gaucho1978/BACCAble/hardware/box/baccable_lastest_case_for_new_PCB/preview5.jpg

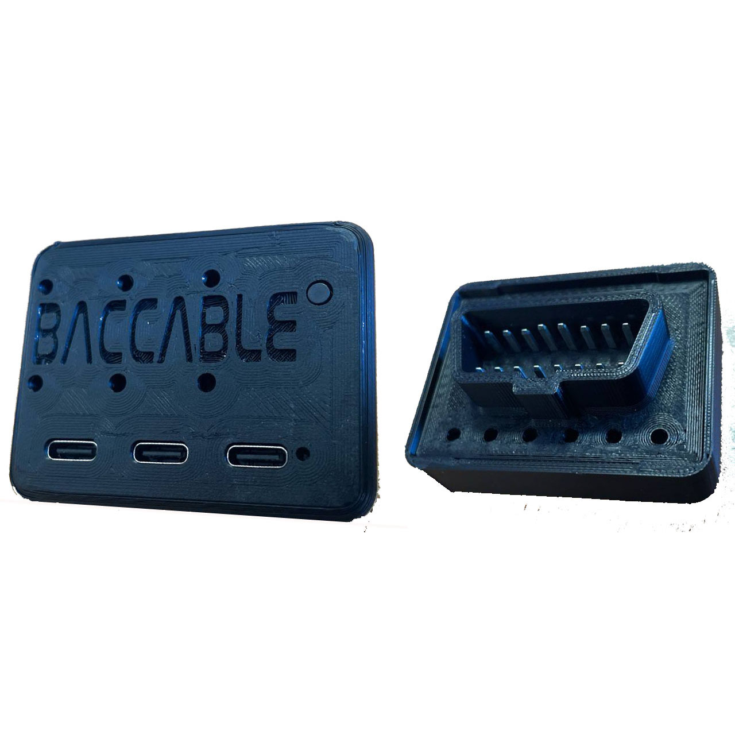
hardware/box/baccable_lastest_case_for_new_PCB/preview5.jpg
