gaucho1978/BACCAble/hardware/box/canableDykbRadioNanoOnly/box.png

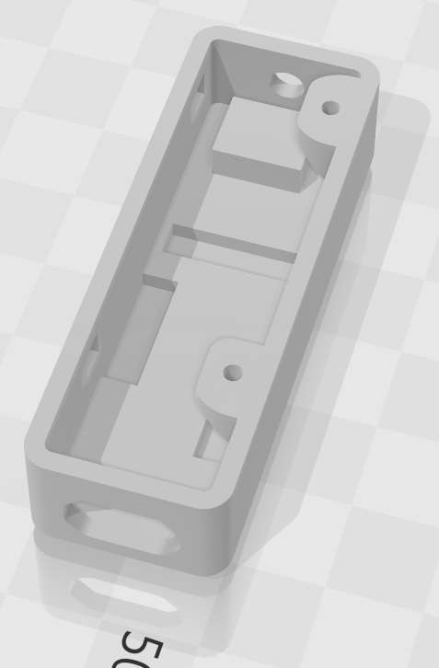
hardware/box/canableDykbRadioNanoOnly/box.png
