gaucho1978/BACCAble/hardware/box/canableDykbRadioNanoOnly/cap.png

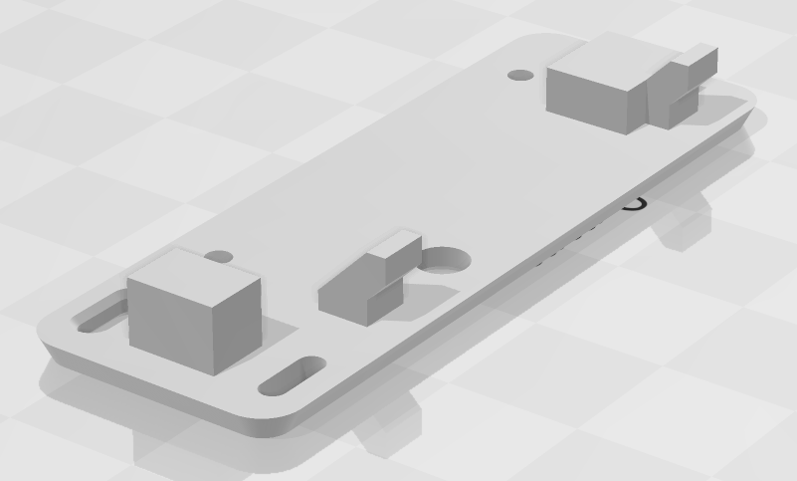
hardware/box/canableDykbRadioNanoOnly/cap.png
