gaucho1978/BACCAble/hardware/box/canableWithDcDcAndTB/box.png

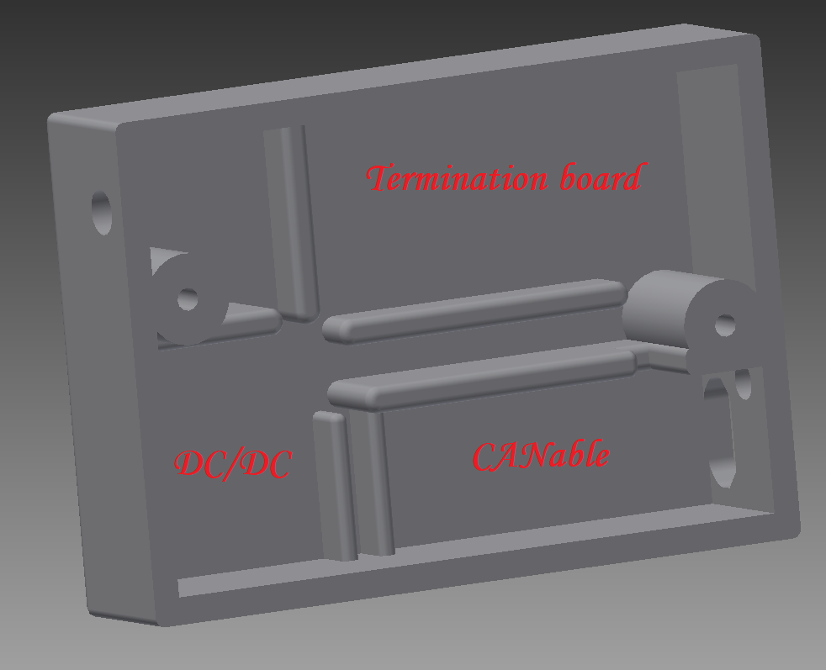
hardware/box/canableWithDcDcAndTB/box.png
