gaucho1978/BACCAble/hardware/box/canableWithDcDcAndTB/cap.png

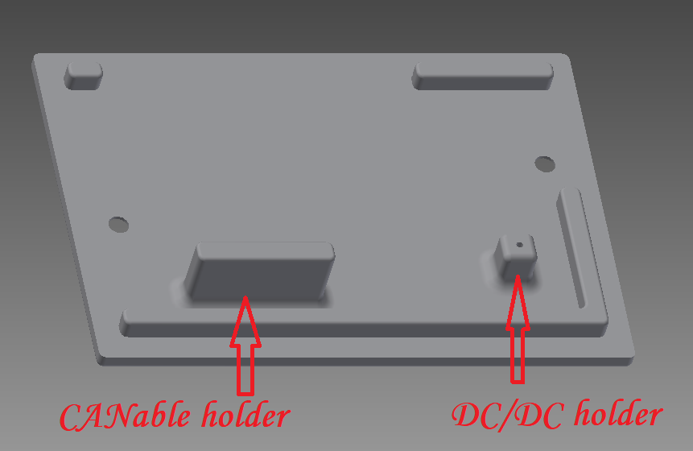
hardware/box/canableWithDcDcAndTB/cap.png
