gaucho1978/BACCAble/hardware/newBaccableDedicatedPcb/pinout.png

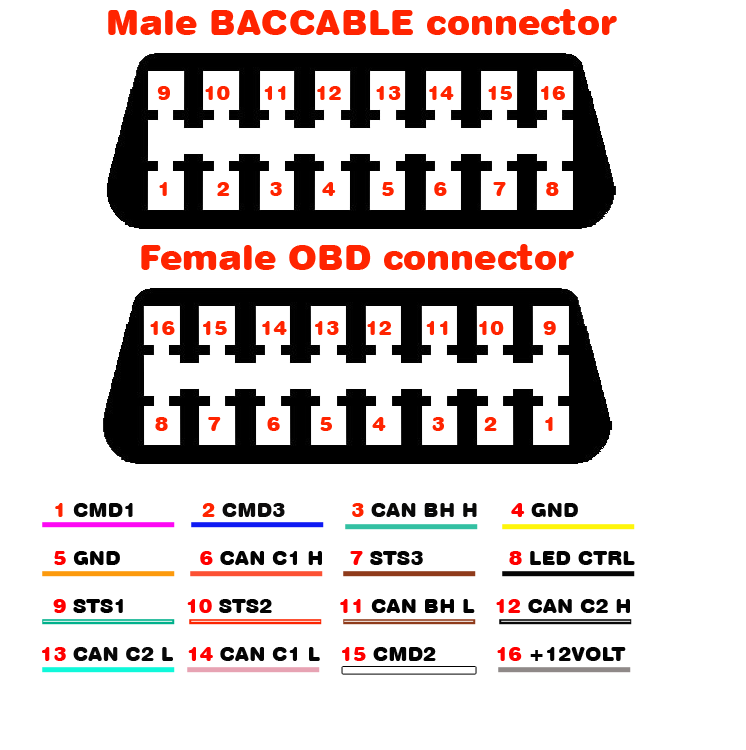
hardware/newBaccableDedicatedPcb/pinout.png
