gaucho1978/BACCAble/hardware/sticker/baccableLabe1l.png

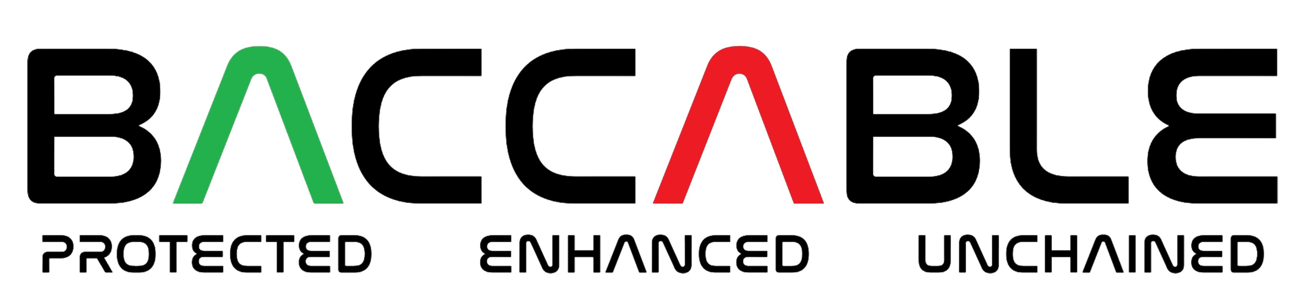
hardware/sticker/baccableLabe1l.png
