gaucho1978/BACCAble/hardware/system_interconnection/IMG_3511.jpeg

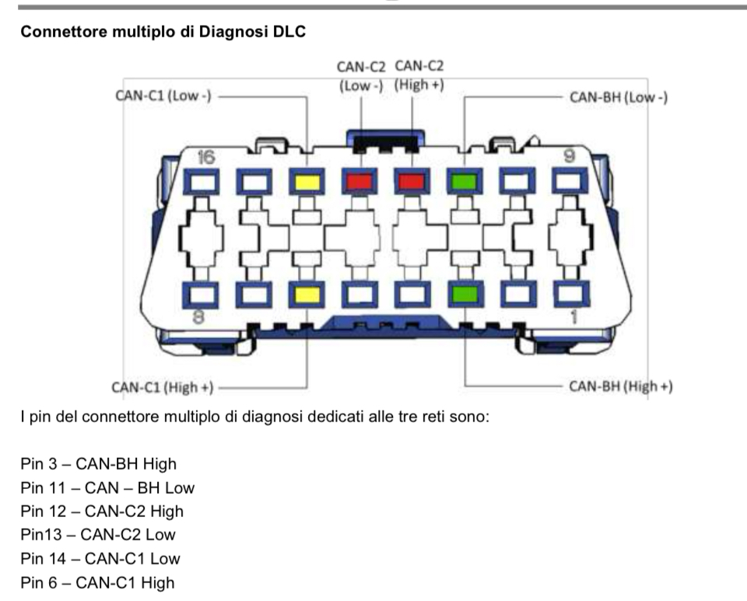
hardware/system_interconnection/IMG_3511.jpeg
