gaucho1978/BACCAble/hardware/system_interconnection/route.png

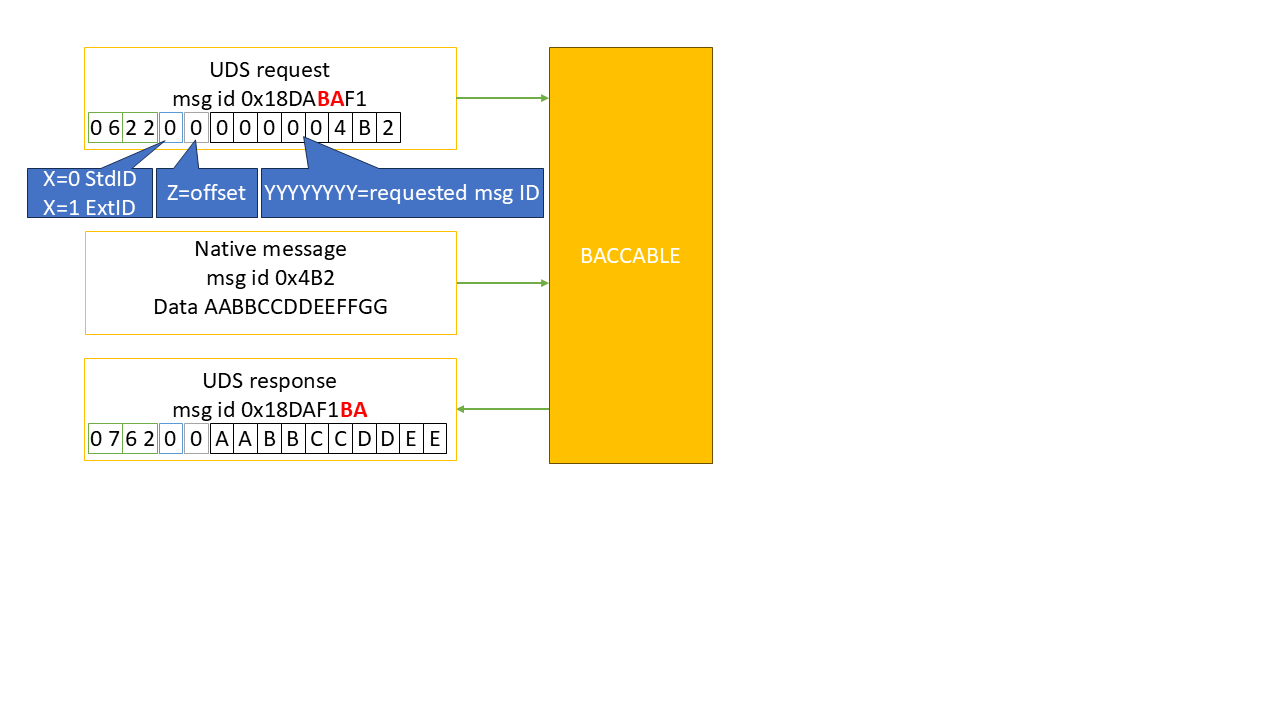
hardware/system_interconnection/route.png
