gaucho1978/BACCAble/hardware/system_interconnection/SCHEMA_DI_INTERCONNESSIONE.png

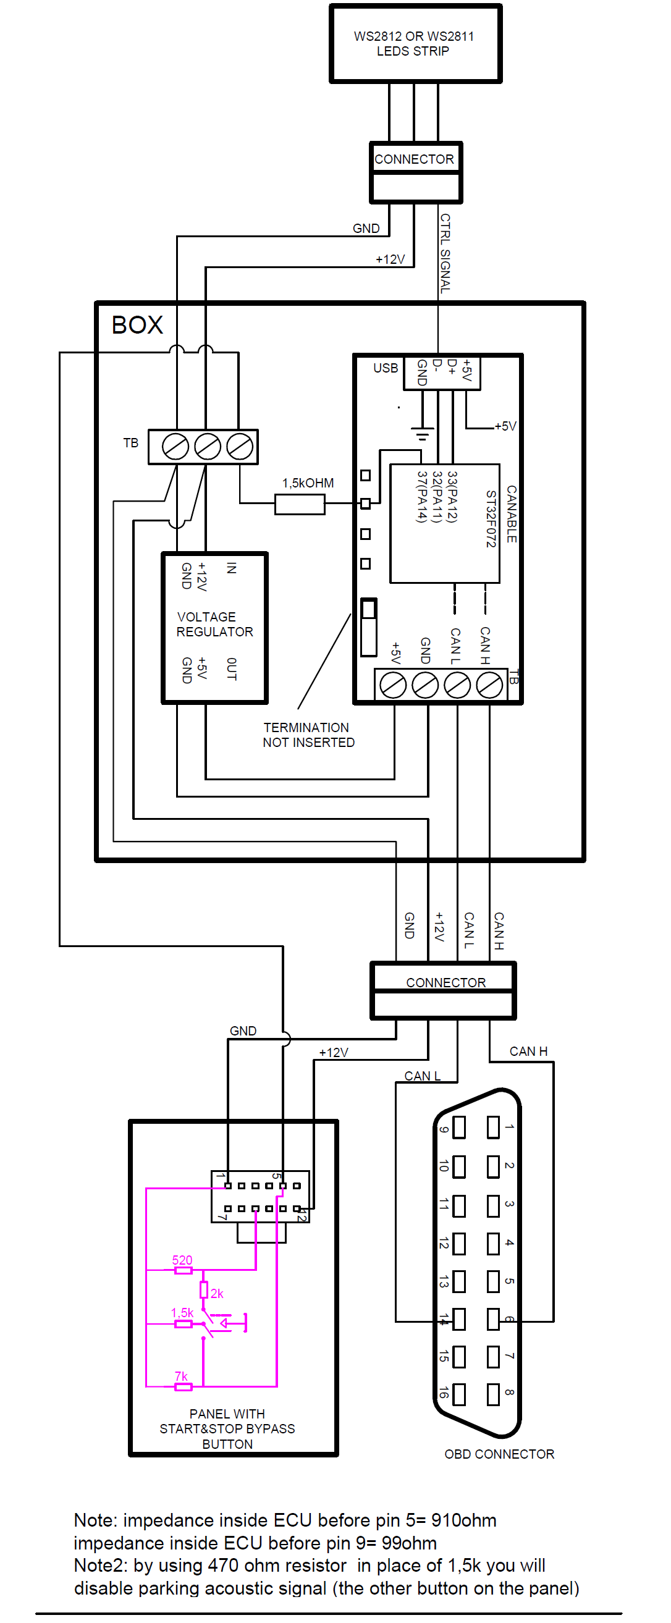
hardware/system_interconnection/SCHEMA_DI_INTERCONNESSIONE.png
