gaucho1978/BACCAble/hardware/box/baccable_lastest_case_for_new_PCB_V2/Imported Components/Baccable4/Baccable4.htm

Autodesk Inventor Translation Report | mercoledì 9 aprile 2025 (18:47)
Source File: | E:\Dati\Documenti_Emanuele\Linguaggi_di_Programmazione\ST MCU\baccable\canable\CANableAndLedsStripController\hardware\box\baccable_lastest_case_for_new_PCB\Baccable4.stp
Translator Type: | STEP | Sending System: | Open CASCADE 6.2
Author: | Author | Translation Time: | 00:00:15
Options
Import Type: | N/A
Entity Types to Import: | Solids, Surfaces
Import into Repair Environment: | No
Import Assembly as Single Part: | Multiple Solid Part
Create Surfaces As: | Single Composite Feature
Check Parts during Load: | No
Auto Stitch: | N/A
Enable Advanced Healing: | No
+/- | Name | Inventor File | Status
[+] [-] | Baccable4.ipt | E:\Dati\Documenti_Emanuele\Linguaggi_di_Programmazione\ST MCU\baccable\canable\CANableAndLedsStripController\hardware\box\baccable_lastest_case_for_new_PCB\Imported Components\Baccable4\Baccable4.ipt | Warning
Severity | Entity Id | Message
Warning | 10938 | Some Surfaces have been simplified
Warning | 19486 | Some Surfaces have been simplified
Warning | 34496 | Some Surfaces have been simplified
Warning | 38605 | Some Surfaces have been simplified
Warning | 52556 | Some Surfaces have been simplified
Warning | 58078 | Degenerate Surface Detected - Please Run the Quality Check Tool
Warning | 58159 | Degenerate Surface Detected - Please Run the Quality Check Tool
Warning | 58291 | Degenerate Surface Detected - Please Run the Quality Check Tool
Warning | 58372 | Degenerate Surface Detected - Please Run the Quality Check Tool
Warning | 56693 | Some Surfaces have been simplified
Warning | 61650 | Degenerate Surface Detected - Please Run the Quality Check Tool
Warning | 61729 | Degenerate Surface Detected - Please Run the Quality Check Tool
Warning | 61811 | Degenerate Surface Detected - Please Run the Quality Check Tool
Warning | 61890 | Degenerate Surface Detected - Please Run the Quality Check Tool
Warning | 64640 | Degenerate Surface Detected - Please Run the Quality Check Tool
Warning | 64721 | Degenerate Surface Detected - Please Run the Quality Check Tool
Warning | 64853 | Degenerate Surface Detected - Please Run the Quality Check Tool
Warning | 64934 | Degenerate Surface Detected - Please Run the Quality Check Tool
Warning | 67202 | Degenerate Surface Detected - Please Run the Quality Check Tool
Warning | 67281 | Degenerate Surface Detected - Please Run the Quality Check Tool
Warning | 67363 | Degenerate Surface Detected - Please Run the Quality Check Tool
Warning | 67442 | Degenerate Surface Detected - Please Run the Quality Check Tool
Warning | 64459 | Some Surfaces have been simplified
Warning | 72437 | Some Surfaces have been simplified
Warning | 244824 | Some Surfaces have been simplified
