gaucho1978/BACCAble/firmware/ledsStripController/Core/Src/functions_C1baccable.c

/*
 * C1baccableFunctions.c
 *
 *  Created on: May 2, 2025
 *      Author: GauchoHP
 *      Common functions for C1baccable
 */
#include <functions_C1baccable.h>

	extern uint32_t _end;      // Fine della sezione .bss (fornito dal linker)
	extern uint32_t _estack;   // Top dello stack (fornito dal linker)
	//uint8_t tmpArr3[2]={C2BusID,C2cmdRaceMaskDefault};

#if defined(C1baccable)
	void C1baccableInitCheck(){
		#ifndef DISABLE_LOW_CONSUME
			lowConsume_init();
		#endif
		immobilizerEnabled = (uint8_t)readFromFlash(1);  //parameter1 stored in ram, so that we can get it. By default Immo is enabled
		if(immobilizerEnabled) executeDashboardBlinks=2; //shows the user that the immobilizer is active (or not)
		function_smart_disable_start_stop_enabled=(uint8_t)readFromFlash(2);  //parameter2 stored in ram, so that we can get it. By default S&S is enabled
		function_led_strip_controller_enabled=(uint8_t)readFromFlash(3); //By default led is disabled
		function_shift_indicator_enabled=(uint8_t)readFromFlash(4); //By default it is disabled
		shift_threshold= (uint16_t)readFromFlash(5);
		function_ipc_my23_is_installed=	(uint8_t)readFromFlash(6);
		function_route_msg_enabled=(uint8_t)readFromFlash(7);
		function_dyno_mode_master_enabled=(uint8_t)readFromFlash(8);
		function_acc_virtual_pad_enabled=(uint8_t)readFromFlash(9);
		function_front_brake_forcer_master=(uint8_t)readFromFlash(10);
		function_4wd_disabler_enabled=(uint8_t)readFromFlash(11);
		function_remote_start_Enabled=(uint8_t)readFromFlash(12);
		function_clear_faults_enabled=(uint8_t)readFromFlash(13);
		function_esc_tc_customizator_enabled=(uint8_t)readFromFlash(14);
		function_read_faults_enabled=(uint8_t)readFromFlash(15);
		function_is_diesel_enabled=(uint8_t)readFromFlash(16);
		total_pages_in_params_setup_dashboard_menu = function_is_diesel_enabled ? total_pages_in_dashboard_menu_diesel : total_pages_in_dashboard_menu_gasoline;

		function_regeneration_alert_enabled=(uint8_t)readFromFlash(17);
		launch_torque_threshold= (uint16_t)readFromFlash(18);
		function_seatbelt_alarm_enabled= (uint16_t)readFromFlash(19);
		function_pedal_booster_enabled= (uint16_t)readFromFlash(20);
		function_disable_odometer_blink= (uint16_t)readFromFlash(21);
		function_show_race_mask= (uint16_t)readFromFlash(22);
		function_park_mirror= (uint16_t)readFromFlash(23);
		function_acc_autostart= (uint16_t)readFromFlash(24);
		function_close_windows_with_door_lock=(uint16_t)readFromFlash(25);
		function_open_windows_with_door_lock=(uint16_t)readFromFlash(26);
		HAS_function_enabled=(uint16_t)readFromFlash(27);
		QV_exhaust_flap_function_enabled=(uint16_t)readFromFlash(28);
		pedal_map_power=(int8_t)(uint8_t)readFromFlash(29);
		parkSensorsMuteFunctionEnabled=(uint8_t)readFromFlash(30);
		snifferFunctionEnabled=(uint8_t)readFromFlash(31); //sniffer function 24/08/2026
		//started here, at boot, so that snifferInUse blocks low consume straight away: lowConsume_process() runs
		//at the top of C1baccablePeriodicCheck() and its inactivity timeout (3500ms) expires 2ms BEFORE the
		//instructSlaveBoardsTriggerEnabled block below (3502ms), so anything that only sets snifferInUse down
		//there would lose that race and C1 would sleep (and pause the inter chip uart) first.
		//The detection window itself is realigned to the slaves later, see that same block. //sniffer function 24/08/2026
		if(snifferFunctionEnabled) snifferStart();
		//elm327 function 26/08/2026 - same lifecycle, but starting it only brings the usb port up and starts the
		//detection window: the baccable keeps working normally until a host actually enumerates us (see
		//elm327CheckActivationTimeout()). The two modes share the single usb cdc port, so they are mutually
		//exclusive: the setup menu already clears one when the other is enabled, this is just the safety net.
		elm327FunctionEnabled=(uint8_t)readFromFlash(32);
		if(elm327FunctionEnabled && snifferFunctionEnabled==0) elm327Start();
		//arise trigger to notify enabled functions to slave boards with dedicated messages,after some seconds
		allProcessorsWakeupTime=currentTime;
		instructSlaveBoardsTriggerEnabled=1;

		readShownParamsFromFlash();
	}

	void setSchizzaforteMap(uint8_t map){
		uint8_t tmpArr0[UART1_BUFFER_SIZE]={'#',0xb6,};

		// Schizzaforte Operative commands:
		//				First Character: #
		//				Second Character:	0x00=set Bypass map, 0x49=set All weather map, 0x92=set Natural map, 0xdb=set Dynamic map,
		//													0x24=set Race map, 0x6d=get current Map, 0xb6=define a Map
		//				Next Characters:	In case of command 0xb6(Define a Map), more 7 chars are sent:
		//													3)map to write (0x00=set Bypass map, 0x49=set All weather map, 0x92=set Natural map,
		//														0xdb=set Dynamic map, 0x24=set Race map),
		//													4)polynomialcurve[][0]
		//													5)polynomialcurve[][1]
		//													6)polynomialcurve[][2]
		//													7)polynomialcurve[][3]
		//													8)polynomialcurve[][4]
		//													9)checksum (calculated)
		// Current selected Map is sent as Reply: 0x10=Bypass, 0x59=All weather, 0xa2=Natural, 0xeb=Dynamic, 0x34=Race

		//map: 2=Bypass, 3=All Weather Map, 4=Natural Map, 5=Dynamic Map, 6=Race Map



		switch(map){
			case 3: //A map
				//prepare power amplification factor
				//input range -10+10, output range -16+16
				if (pedal_map_power >= 0){
					pedal_map_power_adapted = (int8_t)(pedal_map_power * 1.6f+0.5f);
				}else{
					pedal_map_power_adapted = (int8_t)(pedal_map_power * 0.6f-0.5f);
				}

				tmpArr0[2]=0x49;	//A map
				tmpArr0[3]=96+pedal_map_power_adapted;	//amplitude
				tmpArr0[4]=128;		//width
				tmpArr0[5]=154;		//position
				break;
			case 4: //N map
				//prepare power amplification factor
				//input range -10+10, output range -16+32
				if (pedal_map_power >= 0) {
					pedal_map_power_adapted = (int8_t)(pedal_map_power * 3.2f + 0.5f);
				} else {
					pedal_map_power_adapted = (int8_t)(pedal_map_power * 1.6f - 0.5f);
				}

				tmpArr0[2]=0x92;
				tmpArr0[3]=128+pedal_map_power_adapted;		//amplitude
				tmpArr0[4]=128;		//width
				tmpArr0[5]=154;		//position
				break;
			case 5: //D Map
				//prepare power amplification factor
				//input range -10+10, output range -32+20
				if (pedal_map_power >= 0) {
					pedal_map_power_adapted = (int8_t)(pedal_map_power * 2.0f + 0.5f);
				} else {
					pedal_map_power_adapted = (int8_t)(pedal_map_power * 3.2f - 0.5f);
				}
				tmpArr0[2]=0xdb;
				tmpArr0[3]=192+pedal_map_power_adapted;		//amplitude
				tmpArr0[4]=128;		//width
				tmpArr0[5]=154;		//position
				break;
			case 6: //R map
				//prepare power amplification factor
				//input range -10+10, output range -18+24
				if (pedal_map_power >= 0) {
					pedal_map_power_adapted = (int8_t)(pedal_map_power * 2.4f + 0.5f);
				} else {
					pedal_map_power_adapted = (int8_t)(pedal_map_power * 1.8f - 0.5f);
				}
				tmpArr0[2]=0x24;
				tmpArr0[3]=230+pedal_map_power_adapted;		//amplitude
				tmpArr0[4]=128;		//width
				tmpArr0[5]=154;		//position
				break;
			case 2: //bypass
			default: //bypass
				tmpArr0[2]=0x00;
				break;
		}

		tmpArr0[8]=calculateCRC(tmpArr0,UART1_BUFFER_SIZE); //calculate checksum

		//send message
		addToUART1SendQueue(tmpArr0, 9);

	}


	//elm327 function 26/08/2026 - BEGIN
	//Only ram is touched here, so this is safe from anywhere: bringing usb up blocks for a few milliseconds and
	//is deferred to elm327UsbStartIfRequested(), exactly like snifferStart() does.
	void elm327Start(void){
		elm327InUse=1;
		elm327ActivationConfirmed=0;
		elm327ActivationTime=currentTime;	//starts the host detection window (SNIFFER_ACTIVATION_TIMEOUT_MS)
		elm327UsbStartRequested=1;
	}

	//Leaves the mode for good: interpreter off, bridge disarmed on all three chips, usb port down.
	//elm327_set_enabled(0) does all of that (see elm327.c), including usb_device_detach().
	void elm327Stop(void){
		uint8_t wasConfirmed=elm327ActivationConfirmed;
		elm327InUse=0;
		elm327ActivationConfirmed=0;
		elm327UsbStartRequested=0;
		if(wasConfirmed){
			elm327_set_enabled(0);
		}else{
			usb_device_detach(); //never confirmed: the port was only up waiting for a host, nothing else to undo
		}
		//while the mode was running we were not watching the can bus at all, so the last received message would
		//look minutes old and low consume would reset the other two chips the moment we resume. Start the
		//inactivity count from now instead.
		lastReceivedCanMsgTime=currentTime;
		//the slaves spent that time serving the bridge: resend them every function status, as after a wake up
		allProcessorsWakeupTime=currentTime;
		instructSlaveBoardsTriggerEnabled=1;
	}

	//Brings the usb port up. Called from the main loop only: usb_device_attach() waits on HAL_Delay().
	void elm327UsbStartIfRequested(void){
		if(elm327UsbStartRequested==0) return;
		elm327UsbStartRequested=0;
		usb_device_attach(); //idempotent, and it selects the elm327 descriptors on its own
	}

	//Called every main loop iteration while the function is on. Mirrors snifferCheckActivationTimeout(), but
	//the interpreter is switched on only once a host has really enumerated us: until then the baccable must
	//keep working normally, because turning ELM327 on freezes the dashboard and takes over the serial line.
	void elm327CheckActivationTimeout(void){
		if(elm327InUse==0) return;
		if(hUsbDeviceFS.dev_state==USBD_STATE_CONFIGURED){
			if(elm327ActivationConfirmed==0){
				elm327ActivationConfirmed=1;
				elm327_set_enabled(1); //only NOW the baccable steps aside and the bridge is armed
			}
			elm327ActivationTime=currentTime;
			return;
		}
		if(currentTime-elm327ActivationTime<SNIFFER_ACTIVATION_TIMEOUT_MS) return; //still within the grace window
		elm327Stop(); //host never showed up, or went away: back to being a plain baccable
	}
	//elm327 function 26/08/2026 - END

	void C1baccablePeriodicCheck(){
		#ifndef DISABLE_LOW_CONSUME
			lowConsume_process();
		#endif

		if(QV_exhaust_flap_function_enabled){

			// Timeout management for chinese valves radiocontrol
			if (exhaustValveMosfetCommandTime) {
				if(currentTime - exhaustValveMosfetCommandTime > 1000){ //if timeout has passed
					HAL_GPIO_WritePin(Q10mosfet, GPIO_PIN_RESET); //open the transistor (release the button)
					HAL_GPIO_WritePin(Q11mosfet, GPIO_PIN_RESET); //open the transistor (release the button)
					exhaustValveMosfetCommandTime = 0;
				}
			}

			// if a request to press the button on the radiocontrol was made
			if (ChineseExhaustValveRequest){ //O=open, C=close, 0x00=none
			    HAL_GPIO_WritePin(Q10mosfet_Port,(ChineseExhaustValveRequest == 'O') ? Q10mosfet_Pin : Q11mosfet_Pin,GPIO_PIN_SET); //close transistor (press button)
			    chineseValveIsOpened = (ChineseExhaustValveRequest == 'O'); //store valves status
			    exhaustValveMosfetCommandTime = currentTime; //store time when button was pressed
			    ChineseExhaustValveRequest = 0; //mark the request as executed
			}

			// if valve was open and engine had been shutted off
			if (chineseValveIsOpened && currentRpmSpeed == 0){
			    HAL_GPIO_WritePin(Q11mosfet, GPIO_PIN_SET); //close transistor
			    exhaustValveMosfetCommandTime = currentTime; //store time when button was pressed
			    chineseValveIsOpened = 0; //update valves status
			}


			switch(ForceQVexhaustValveOpened){
				case 1: //send connection request
				case 2: //send presence
				case 3: //overwrite param
				case 4: //return control to ECU
					if(currentTime-lastSentQVexhaustValveMsgTime>500){ //each 500msec send a message
						if(currentRpmSpeed==0) ForceQVexhaustValveOpened=4; //return control to ecu
						onboardLed_blue_on();
						//onboardLed_red_on();
						can_tx(&forceQVexhaustValveMsgHeader[ForceQVexhaustValveOpened-1], forceQVexhaustValveMsgData[ForceQVexhaustValveOpened-1]); //send connect message
						lastSentQVexhaustValveMsgTime=currentTime;
						switch(ForceQVexhaustValveOpened){
							case 1: //connection request was sent
							case 2: //presence was sent
								ForceQVexhaustValveOpened++; //prepare to send next
								break;
							case 3: //param overwrite was sent
								ForceQVexhaustValveOpened--; //prepare to send tester presence
								break;
							case 4: //return control to ECU was sent
								ForceQVexhaustValveOpened=0; //sequence end
								break;
							default:  //we will never come here
								break;
						}

					}
					break;
				default: //do nothing
					break;
			}

		}

		if(ESCandTCinversion){
			if(currentRpmSpeed==0) ESCandTCinversion=0;
			if((currentTime-lastSent384)>50){
				lastSent384=currentTime;
				DNA_msg_data[1] = (DNA_msg_data[1] & ~0x7C) | 0x30;  //set Race mode (0x30) to show on IPC the race screen
				//uint8_t tmpCounter=(DNA_msg_data[6] & 0x0F)+1;
				//if(tmpCounter>0x0F) tmpCounter=0;
				//DNA_msg_data[6]= (DNA_msg_data[6] & 0xF0) | tmpCounter;   //increment counter
				DNA_msg_data[7]=calculateCRC(DNA_msg_data,DNA_msg_header.DLC); //update CRC
				can_tx((CAN_TxHeaderTypeDef *)&DNA_msg_header, DNA_msg_data); //transmit the modified packet
			}
		}


		if(instructSlaveBoardsTriggerEnabled){
			if((currentTime-allProcessorsWakeupTime)>TIMING__C1____DELAY_BEFORE_SERIAL_INSTRUCT_OF_C2BH_AFTER_OTHER_CHIP_WAKE_MS){
				//onboardLed_red_blink(5);
				instructSlaveBoardsTriggerEnabled=0; //avoid to return here


				//send messages to slave boards
				uint8_t tmpArr0[2]={C2_Bh_BusID,C2_Bh_cmdFunction_ESC_TC_Enabled};
				if(!function_esc_tc_customizator_enabled) tmpArr0[1]=C2_Bh_cmdFunction_ESC_TC_Disabled;
				addToUARTSendQueue(tmpArr0, 2);

				//send messages to slave boards
				uint8_t tmpArr1[3]={C2_Bh_BusID,C2_Bh_cmdSetPedalBoostStatus,function_pedal_booster_enabled};
				addToUARTSendQueue(tmpArr1, 3);

				//send the message to BH to inform about the status of the function disable_odometer_blink
				uint8_t tmpArr2[2]={BhBusID,BHcmdOdometerBlinkDefault};
				if(function_disable_odometer_blink) tmpArr2[1]=BHcmdOdometerBlinkDisable;
				addToUARTSendQueue(tmpArr2, 2);

				//Now let's inform the C2 Baccable
				uint8_t tmpArr3[2]={C2BusID,C2cmdRaceMaskDefault};
				if(function_show_race_mask) tmpArr3[1]=C2cmdShowRaceMask;
				addToUARTSendQueue(tmpArr3, 2);

				//Now let's inform the BH Baccable
				uint8_t tmpArr4[2]={BhBusID,BHcmdFunctParkMirrorDisabled};
				if(function_park_mirror) tmpArr4[1]=BHcmdFunctParkMirrorEnabled;
				addToUARTSendQueue(tmpArr4, 2);

				//notify to C2 and BH HAS function status
				uint8_t tmpArr5[2]={C2_Bh_BusID,C2_Bh_cmdFunctHAS_Disabled};
				if(HAS_function_enabled) tmpArr5[1]=C2_Bh_cmdFunctHAS_Enabled;
				addToUARTSendQueue(tmpArr5, 2);

				//notify to C2 the park sensors mute function status
				uint8_t tmpArr6[2]={C2BusID,C2cmdFunctParkSensorsMuteDisabled};
				if(parkSensorsMuteFunctionEnabled) tmpArr6[1]=C2cmdFunctParkSensorsMuteEnabled;
				addToUARTSendQueue(tmpArr6, 2);
				parkMuteBrakeSent=0xFF; //C2 may have just woken up: the next 0x107 sends it the brake state again //park mute brake from C1 10/10/2026

				//notify to C2 and BH the sniffer function status //sniffer function 24/08/2026
				uint8_t tmpArr7[2]={C2_Bh_BusID,C2_Bh_cmdSnifferDisabled};
				if(snifferFunctionEnabled){
					tmpArr7[1]=C2_Bh_cmdSnifferEnabled;
					//restart our own host detection window from this instant, so it runs alongside the one the
					//slaves are starting right now on receiving this very message, instead of being measured from
					//our own earlier boot: otherwise C1 would give up (and allow sleep, pausing the inter chip
					//uart) while a slave is still legitimately waiting for its host. snifferInUse is already 1
					//since boot - see C1baccableInitCheck() - so this does not affect the sleep guard at all.
					snifferActivationTime=currentTime; //sniffer function 24/08/2026
				}
				addToUARTSendQueue(tmpArr7, 2);
			}
		}

		if(function_led_strip_controller_enabled==1){
			//don't act as canable. One USB port pin is used to control leds.
			vuMeterInit(); //initialize leds strip controller - this is called many times to divide the operations on more loops
			if(ledsStripIsOn){ //if the strip is on,
				if(currentTime-timeSinceLastReceivedAcceleratorMessage>10000 ){ //if no can interesting message for 10 seconds,  shutdown the leds to save energy
					shutdownLedsStrip();
					ledsStripIsOn=0; //entriamo solo una volta
				}
			}
		}

		//dyno debug 04/10/2026 - 4wd and dyno status changes, detected here in the main loop: _4wd_disabled is written by the
		//menu, the engine off logic and the sequence below, DynoModeEnabledOnMaster by the uart rx interrupt (no tracing allowed there)
		if(_4wd_disabled!=snifferLast4wdDisabled){
			SNIFFER_DEBUG2(0x2300, snifferLast4wdDisabled, ((uint32_t)function_4wd_disabler_enabled<<8)|_4wd_disabled); //4wd: status changed. v1=old, v2=new (byte1=function enabled, byte0=_4wd_disabled; 1 = ECU reset loop running) //dyno debug 04/10/2026
			snifferLast4wdDisabled=_4wd_disabled;
		}
		if(DynoModeEnabledOnMaster!=snifferLastDynoEnabledOnMaster){
			SNIFFER_DEBUG2(0x2301, DynoModeEnabledOnMaster, _4wd_disabled); //4wd: dyno status reported by C2 changed. v1=new dyno status, v2=current _4wd_disabled //dyno debug 04/10/2026
			snifferLastDynoEnabledOnMaster=DynoModeEnabledOnMaster;
		}

		faultsAbsProcess(); //ABS faults sent by C2 for Read Faults //readFaults ABS 10/10/2026
		//readFaults debug 05/10/2026 - read faults state changes, detected here in the main loop (start from menu, timeout, end, exit)
		if(faultsStateMachine!=snifferLastFaultsState){
			SNIFFER_DEBUG2(0x2500, snifferLastFaultsState, faultsStateMachine); //read faults: state changed. v1=old, v2=new (0xFF idle, 0 session, 1 ReadDTC, 2 multiframe, 3 list ready, 4 TIMEOUT) //readFaults debug 05/10/2026
			snifferLastFaultsState=faultsStateMachine;
		}

		if(function_4wd_disabler_enabled==1){
			if(_4wd_disabled>0){
				uint8_t tempDeltaTime=0;
				if(_4wd_disabled>1) tempDeltaTime=70;
				if(currentTime-last_sent_drive_train_msg_time>30+tempDeltaTime){ //enter here once each 100msec, then each 30msec
					last_sent_drive_train_msg_time=currentTime;
					onboardLed_blue_on();
					can_tx(&driveTrainControlModuleResetMsgHeader[_4wd_disabled-1], driveTrainControlModuleResetMsgData[_4wd_disabled-1]); //send drive train control module message
					if(_4wd_disabled>1) _4wd_disabled--;
				}
			}
		}

		if(executeDashboardBlinks>0){ //if we shall execute a blink to give a feedback to the user
			if(currentTime-last_sent_dashboard_blink_msg_time>500){ //enter here once each halfsecond
				last_sent_dashboard_blink_msg_time=currentTime;//return here after half second
				//change the message
				if(executeDashboardBlinks % 2==0){ //select one time reduced brightness and one time high brightness, so that in any condition the change is visible on the dashboard
					dashboardBlinkMsgData[4]=0x00; //max bright
				}else{
					dashboardBlinkMsgData[4]=0xF0; //reduced bright
				}
				executeDashboardBlinks = executeDashboardBlinks -1 ;//decrease blinks counter
				onboardLed_blue_on();
				//send the message
				can_tx(&dashboardBlinkMsgHeader, dashboardBlinkMsgData);
			}
		}


		if(immobilizerEnabled){
			//the following it is used only by IMMOBILIZER functionality
			if(floodTheBus){ //WHEN THIS IS ACTIVATED, THE THIEF WILL NOT BE ABLE TO CONNECT TO RFHUB, AND CAR WILL NOT SWITCH ON.
				if(currentTime-floodTheBusLastTimeSent>10){
					can_tx(&panicAlarmStartMsgHeader[0], panicAlarmStartMsgData[0]); //sends the message on can bus that resets the connection to RFHUB
					floodTheBusLastTimeSent=currentTime;
				}

				if(!panicAlarmActivated){ //if panic alarm is not activated, we shall activate it after 1 second (1 second to avoid stop and start simultaneous)
					if(currentTime-floodTheBusStartTime>1000){
						for (uint8_t i=0;i<15;i++){
							can_tx(&panicAlarmStartMsgHeader[1], panicAlarmStartMsgData[1]);
						}
						can_tx(&panicAlarmStartMsgHeader[2], panicAlarmStartMsgData[2]);
						panicAlarmActivated=1;
					}
				}
				if(currentTime-floodTheBusStartTime>10000){ //if the bus is flooded since 10 seconds, stop flooding it
					floodTheBus=0; //stop flooding
					//stop the panic alarm
					for (uint8_t i=0;i<15;i++){
						can_tx(&panicAlarmStartMsgHeader[1], panicAlarmStartMsgData[1]);
					}
					can_tx(&panicAlarmStartMsgHeader[2], panicAlarmStartMsgData[2]);
					panicAlarmActivated=0;
				}


			}
		}

		if(function_smart_disable_start_stop_enabled){
			if(startAndStopEnabled){
				if(currentTime>10000){ //first 10 seconds don't do anything to avoid to disturb other startup functions or immobilizer
					if(engineOnSinceMoreThan5seconds>=500){ //if motor is on since at least 5 seconds

						if(startAndstopCarStatus==0){//if start & stop was found disabled in car, we don't need to do anything. Avoid to enter here; We enter here in example if board is switched when the car is running and S&S was still manually disabled by the pilot
							startAndStopEnabled=0;
							requestToDisableStartAndStop=0;
						}else{
							if(lastTimeStartAndstopDisablerButtonPressed==0){ //first time we arrive here, go inside
								requestToDisableStartAndStop=1;
							}
						}
					}
				}
			}
		}

		/*
		if(seatbeltAlarmDisabled==0xff ){ //if the status is unknown
			if(engineOnSinceMoreThan5seconds>=200){ //if motor is on since at least 2 seconds
				//get the status of the seatbelt alarm

				uds_parameter_request_msg_header.ExtId=0x18DA60F1;
				uds_parameter_request_msg_data[0]=0x03;
				uds_parameter_request_msg_data[1]=0x22;
				uds_parameter_request_msg_data[2]=0x55;
				uds_parameter_request_msg_data[3]=0xA0;
				uds_parameter_request_msg_header.DLC=4;
				can_tx(&uds_parameter_request_msg_header, uds_parameter_request_msg_data); //transmit the request
				seatbeltAlarmDisabled=0xfe; //status is in aquisition
				seatbeltAlarmStatusRequestTime=currentTime;
				last_sent_uds_parameter_request_Time=currentTime;
			}
		}
		*/

		if(((seatbeltAlarmDisabled==0xfe) || (seatbeltAlarmDisabled==0x10) || (seatbeltAlarmDisabled==0x20) || (seatbeltAlarmDisabled==0x11) || (seatbeltAlarmDisabled==0x21)) && (currentTime-seatbeltAlarmStatusRequestTime>10000)){ //if operations in progress but timeout was reached
			seatbeltAlarmDisabled=0xff;//return to unknown status
		}


		if(((seatbeltAlarmDisabled==1) || (seatbeltAlarmDisabled==0xff) ) && (function_seatbelt_alarm_enabled==1)){ //the alarm is disabled (or unknown) and the use wants to enable it
			if(engineOnSinceMoreThan5seconds>=200){
				//request to enable Seatbelt Alarm
				//send diag session request
				uds_parameter_request_msg_header.ExtId=0x18DA60F1;
				uds_parameter_request_msg_data[0]=0x02;
				uds_parameter_request_msg_data[1]=0x10;
				uds_parameter_request_msg_data[2]=0x03;
				uds_parameter_request_msg_header.DLC=3;
				can_tx(&uds_parameter_request_msg_header, uds_parameter_request_msg_data); //transmit the diag session request

				seatbeltAlarmDisabled=0x20; //request to enable SeatBelt alarm in progress(send write param)
				seatbeltAlarmStatusRequestTime=currentTime;
				last_sent_uds_parameter_request_Time=currentTime;
			}
		}

		if((seatbeltAlarmDisabled==0 || seatbeltAlarmDisabled==0xff)  && function_seatbelt_alarm_enabled==0){ //alarm is enabled (or unknown) and user wants to disable it
			if(engineOnSinceMoreThan5seconds>=200){
				//request to disable Seatbelt Alarm
				//send diag session request
				uds_parameter_request_msg_header.ExtId=0x18DA60F1;
				uds_parameter_request_msg_data[0]=0x02;
				uds_parameter_request_msg_data[1]=0x10;
				uds_parameter_request_msg_data[2]=0x03;
				uds_parameter_request_msg_header.DLC=3;
				can_tx(&uds_parameter_request_msg_header, uds_parameter_request_msg_data); //transmit the diag session request

				seatbeltAlarmDisabled=0x10; //request to disable SeatBelt alarm in progress(send write param)
				seatbeltAlarmStatusRequestTime=currentTime;
				last_sent_uds_parameter_request_Time=currentTime;
			}
		}

		if(function_pedal_booster_enabled){ //if enabled, communicate with schizzaForte each 250msec
			if(currentRpmSpeed<400) currentSchizzaforteMap='-'; //if engine is stopped. Forget the pedal map setting, so that baccable will be forced to set it again on schizzaforte

			if(function_pedal_booster_enabled==8){ // Kids Limiter
				// Independent check 1: ensure map A with minimum power is active (handles boot and any drift)
				if(currentRpmSpeed>400 && currentSchizzaforteMap!='A'){
					if((currentTime-last_queued_serial_to_schizzaForte_msg_time)>(4*TIMING__C1____SCHIZZAFORTE_SERIAL_TIMEOUT_REPLY_MS)){
						last_queued_serial_to_schizzaForte_msg_time=currentTime;
						int8_t saved_pedal_map_power=pedal_map_power;
						pedal_map_power=-10;
						setSchizzaforteMap(3); //A map with minimum power
						pedal_map_power=saved_pedal_map_power;
					}
				}
				// Independent check 2: override throttle to 0 when RPM or speed exceed thresholds
				uint32_t kidsRpmLimit = function_is_diesel_enabled ? 3000 : 4000;
				if((currentRpmSpeed>kidsRpmLimit || currentSpeed_km_h>100.0f) && currentRpmSpeed>400){
					if((currentTime-last_queued_serial_to_schizzaForte_msg_time)>400){
						last_queued_serial_to_schizzaForte_msg_time=currentTime;
						uint8_t kidsLimMsg[UART1_BUFFER_SIZE]={'#',0xff,0x00,0,0,0,0,0,0};
						kidsLimMsg[8]=calculateCRC(kidsLimMsg,UART1_BUFFER_SIZE);
						addToUART1SendQueue(kidsLimMsg, 9);
					}
				}
			}else{
				if(mapCommandNotApplied() && (currentRpmSpeed>400)){ //only if the map command was not correctly received and engine is on
					if((currentTime - last_queued_serial_to_schizzaForte_msg_time)>(4 * TIMING__C1____SCHIZZAFORTE_SERIAL_TIMEOUT_REPLY_MS) ){
						last_queued_serial_to_schizzaForte_msg_time=currentTime; //avoid to Return Here

						if(function_pedal_booster_enabled==1){ // 1=Auto: set map according to DNA selector
							//function_pedal_booster_enabled: 0=disabled, 1=Automatic Map, 2=Bypass, 3=All Weather Map, 4=Natural Map, 5=Dynamic Map, 6=Race Map, 7=Hybrid Align, 8=Kids Limiter
							switch(currentDNAmode){
								case 0x00: //Natural
									setSchizzaforteMap(4);
									break;
								case 0x08: //Dynamic
									setSchizzaforteMap(5);
									break;
								case 0x10: //All Weather
									setSchizzaforteMap(3);
									break;
								case 0x30: //Race
									setSchizzaforteMap(6);
									break;
								default:
									setSchizzaforteMap(2); //bypass
							}
						}else if(function_pedal_booster_enabled==7){ // 7=Hybrid Align: N map in A/N/D, Race map in Race
							if(currentDNAmode==0x30){
								setSchizzaforteMap(6); //Race map when DNA is in Race
							}else{
								setSchizzaforteMap(4); //Natural map when DNA is in A, N or D
							}
						}else{
							setSchizzaforteMap(function_pedal_booster_enabled); //direct map for values 2-6
						}
					}
				}
			}
		}

		if(playMotorJingle){ //if  jingle was requested, check if we have to disable it
			if(currentDNAmode!=0 || currentRpmSpeed< 400){ //engine off or drive style not Natural
				playMotorJingle=0;
			}
		}

		if(playMotorJingle){ //if we have to execute jingle


			//once each 400msec play one note with the engine
			if((currentTime - last_queued_serial_to_schizzaForte_msg_time)>(4 * TIMING__C1____SCHIZZAFORTE_SERIAL_TIMEOUT_REPLY_MS) ){
				last_queued_serial_to_schizzaForte_msg_time=currentTime; //avoid to Return Here
				//play it: force motor RPM for one time slot

				// Schizzaforte Operative commands:
				//				First Character: #
				//				Second Character:	0x6d=get current Map, 0xb6=define a Map, 0xff=set accelerator percentage
				//				Next Characters:	In case of command 0xb6(Define a Map), more 7 chars are sent:
				//													3)map to write (0x00=set Bypass map, 0x49=set All weather map, 0x92=set Natural map,
				//														0xdb=set Dynamic map, 0x24=set Race map),
				//													4)polynomialcurve[][0]
				//													5)polynomialcurve[][1]
				//													6)polynomialcurve[][2]
				//													7)polynomialcurve[][3]
				//													8)polynomialcurve[][4]
				//													9)checksum (calculated)
				//				Next Characters:	In case of command 0xff (set Accelerator), more 7 chars are sent:
				//													3)accelerator value (0-255= 0 to 1 percentage)
				//													4)0 //not used
				//													5)0 //not used
				//													6)0 //not used
				//													7)0 //not used
				//													8)0 //not used
				//													9)checksum (calculated)
				// Current selected Map is sent as Reply to any request: 0x10=Bypass, 0x59=All weather, 0xa2=Natural, 0xeb=Dynamic, 0x34=Race

				uint8_t tmpArr0[UART1_BUFFER_SIZE]={'#',0xff,};
				tmpArr0[2]=jingleArray[255-(playMotorJingle--)]; //set accelerator value from jingle array
				tmpArr0[8]=calculateCRC(tmpArr0,UART1_BUFFER_SIZE); //calculate checksum

				//send message
				addToUART1SendQueue(tmpArr0, 9);
			}
		}


		if(shutdownDashboardMenuRequestTime>0){
			if(currentTime-shutdownDashboardMenuRequestTime>39000){
				baccableDashboardMenuVisible=0; //stop sending params request when motor is off
				clearDashboardBaccableMenu(); //ripulisci la stringa
				baccabledashboardMenuWasVisible=1; //allows the menu to automatically turn on when motor rotates
				shutdownDashboardMenuRequestTime=0; //avoid to return here
			}
		}
		//send a parameter request each xx msec if dashboard menu shall be visible
		//baccableDashboardMenuVisible=1; //force menu always on, just for debug
		if((currentTime-last_sent_uds_parameter_request_Time>500) && baccableDashboardMenuVisible ){
			last_sent_uds_parameter_request_Time=currentTime;


			switch(dashboard_menu_indent_level){
				case 0: //main menu
					sendMainDashboardPageToSlaveBaccable();
					break;
				case 1:
					if(main_dashboardPageIndex==1){ //we are in show params submenu
						clearFaultsRequest=0; //ensure we don't perform more tasks simoultaneously
						currentParamElementSelection=!currentParamElementSelection;
						if(uds_params_array[function_is_diesel_enabled][dashboardPageIndex].udsParamId[currentParamElementSelection]== uds_params_array[function_is_diesel_enabled][dashboardPageIndex].udsParamId[!currentParamElementSelection]){
							currentParamElementSelection=0; //single param
						}

						if(single_uds_params_array[uds_params_array[function_is_diesel_enabled][dashboardPageIndex].udsParamId[currentParamElementSelection]].reqId>0xFF){ //if req id is greather than 0xFF it is a standard UDS request.
							//request current parameter to ECU
							uds_parameter_request_msg_header.ExtId=single_uds_params_array[uds_params_array[function_is_diesel_enabled][dashboardPageIndex].udsParamId[currentParamElementSelection]].reqId;

							memcpy(&uds_parameter_request_msg_data[0],&single_uds_params_array[uds_params_array[function_is_diesel_enabled][dashboardPageIndex].udsParamId[currentParamElementSelection]].reqData,single_uds_params_array[uds_params_array[function_is_diesel_enabled][dashboardPageIndex].udsParamId[currentParamElementSelection]].reqLen );
							uds_parameter_request_msg_header.DLC=single_uds_params_array[uds_params_array[function_is_diesel_enabled][dashboardPageIndex].udsParamId[currentParamElementSelection]].reqLen;
							//onboardLed_blue_on();
							can_tx(&uds_parameter_request_msg_header, uds_parameter_request_msg_data); //transmit the request
						}else{ //<0xff reqId means special value that we use to get particular values
							float nativeVal=getNativeParam((uint8_t)uds_params_array[function_is_diesel_enabled][dashboardPageIndex].udsParamId[currentParamElementSelection]);
							if(maxHold_enabled){
								if(isnan(dashboardParamCouple[currentParamElementSelection])){
									dashboardParamMaxHold[currentParamElementSelection]=nativeVal; //first update after navigation: reset max hold
								}else if(nativeVal > dashboardParamMaxHold[currentParamElementSelection]){
									dashboardParamMaxHold[currentParamElementSelection]=nativeVal; //new maximum found
								}
								dashboardParamCouple[currentParamElementSelection]=dashboardParamMaxHold[currentParamElementSelection];
							}else{
								dashboardParamCouple[currentParamElementSelection]=nativeVal;
							}
							sendDashboardPageToSlaveBaccable();  //Send params to BH board
						}
					}

					if(main_dashboardPageIndex==9){
						sendSetupDashboardPageToSlaveBaccable();
					}
					if(main_dashboardPageIndex==10){
						sendParamsSetupDashboardPageToSlaveBaccable();
					}
					if(main_dashboardPageIndex==2){ //readFaults 12/08/2026
						// Timeout stati attesa 0/1/2: 2 secondi senza risposta dalla ECU in lettura (BODY o ECM) //readFaults ECM 10/10/2026
						if(faultsStateMachine < 3){
							// readFaults fix 05/10/2026 - dopo un 7F xx 78 (responsePending) la ECU ha fino a P2*server (5 s) per rispondere
							//readFaults ABS 10/10/2026 - ABS: C2 is asked about once a second (processUART), and answers 'B' while reading
							uint32_t faultsTimeout = (faultsEcu==FAULTS_ECU_ABS) ? 5000 : (faultsResponsePending ? 5000 : 2000);
							if(currentTime - faultsTimer > faultsTimeout){
								SNIFFER_DEBUG2(0x2507, faultsStateMachine, faultsResponsePending); //read faults: timeout, no reply from the ECU being read (BODY or ECM, see 0x2509). v1=state, v2=1 if waiting after responsePending //readFaults debug 05/10/2026
								faultsEcuEnded(1); // BODY: TIMEOUT display. ECM: list with the BODY faults //readFaults ECM 10/10/2026
							}
						}
						// Stato 4 TIMEOUT: dopo 1 secondo ritorna al menu principale
						if(faultsStateMachine == 4){
							if(currentTime - faultsTimer > 1000){
								faultsStateMachine = 0xFF;
								dashboard_menu_indent_level = 0;
							}
						}
						sendMainDashboardPageToSlaveBaccable(); // aggiorna display (WAIT / DTC / TIMEOUT)
					}
					break;
				default:
					break; //unexpected
			}
		}

		//pumpForce test25/07/2026 - BEGIN
		// -----------------------------------------------------------------------
		// PUMP FORCE — Innesco sequenza UDS e invio periodico IO Control
		//
		// Abilitato da function_pump_force_enabled = 1.
		// Dopo 10 secondi dal boot (currentTime > 10000) la macchina a stati viene
		// avviata inviando una richiesta di sessione diagnostica estesa (10 03) all'ECM.
		// Le risposte ECM (50 03, 67 01, 67 02, 7F) sono gestite in processingExtendedMessage.c
		// che aggiorna pumpForceStateMachine e preimposta pumpForceTxHeader/pumpForceTxData.
		//
		// In stato 3 (accesso sicurezza concesso): invia 2F 50 11 03 FF ogni 200ms.
		// Timeout negli stati 0/1/2: se non arriva risposta entro 500ms → abort senza retry.
		// In caso di errore o timeout: function_pump_force_enabled rimane =1 ma
		// pumpForceStateMachine va a 0xFF (inattivo) → nessun re-invio automatico.
		// -----------------------------------------------------------------------
		if (function_pump_force_enabled) {

			// Innesco iniziale: prima esecuzione dopo 10s, macchina ferma (stato 0xFF) per test
			/*
			if (pumpForceStateMachine == 0xFF && currentTime > 10000) {
				// Apri sessione diagnostica estesa con l'ECM: invia DiagnosticSessionControl 10 03
				pumpForceTxHeader.DLC = 3;
				pumpForceTxData[0] = 0x02; // PCI: single frame, 2 byte dati
				pumpForceTxData[1] = 0x10; // SID: DiagnosticSessionControl
				pumpForceTxData[2] = 0x03; // sessionType: extendedDiagnosticSession
				can_tx(&pumpForceTxHeader, pumpForceTxData);
				pumpForceStateMachine = 0;           // attendi risposta 50 03 dalla ECM
				lastPumpForceMsgTime = currentTime;  // timestamp di inizio per calcolo timeout
			}
			*/

			// Timeout handshake (stati 0, 1, 2): se non arriva risposta entro 500ms → abbandona
			// Il booleano function_pump_force_enabled NON viene reimpostato (nessun retry)
			if (pumpForceStateMachine < 3 && pumpForceStateMachine != 0xFF) {
				if (currentTime - lastPumpForceMsgTime > 500) {
					pumpForceStateMachine = 0xFF; // timeout: sequenza abortita definitivamente
				}
			}

			// Stato 3: accesso sicurezza concesso → invia IO Control ogni 200ms
			// pumpForceTxHeader (DLC=6) e pumpForceTxData ([05,2F,50,11,03,FF,...])
			// sono stati impostati in processingExtendedMessage.c alla transizione 2→3
			if (pumpForceStateMachine == 3) {
				if (currentTime - lastPumpForceMsgTime >= 200) {
					can_tx(&pumpForceTxHeader, pumpForceTxData); // 2F 50 11 03 FF
					lastPumpForceMsgTime = currentTime;
				}
			}
		}
		//pumpForce test25/07/2026 - END
	}

	//verifies if message sent to schizzaforte was correctly applied
	uint8_t mapCommandNotApplied(void){

		switch(function_pedal_booster_enabled){
			case 0: //0=disabled
				//return 0; //not required to set map
				break;
			case 1: //1=Automatic Map
				switch(currentDNAmode){
					case 0x00: //Natural
						if(currentSchizzaforteMap=='N') return 0; //map applied
						break;
					case 0x08: //Dynamic
						if(currentSchizzaforteMap=='D') return 0; //map applied
						break;
					case 0x10: //All Weather
						if(currentSchizzaforteMap=='A') return 0; //map applied
						break;
					case 0x30: //Race
						if(currentSchizzaforteMap=='R') return 0; //map applied
						break;
					default:
						//
				}

				break;
			case 2: //2=Bypass
				if(currentSchizzaforteMap=='B') return 0; //map applied
				break;
			case 3: //3=All Weather Map
				if(currentSchizzaforteMap=='A') return 0; //map applied
				break;
			case 4: //4=Natural Map
				if(currentSchizzaforteMap=='N') return 0; //map applied
				break;
			case 5: //5=Dynamic Map
				if(currentSchizzaforteMap=='D') return 0; //map applied
				break;
			case 6: //6=Race Map
				if(currentSchizzaforteMap=='R') return 0; //map applied
				break;
			case 7: //7=Hybrid Align: N map for A/N/D, Race map for Race
				if(currentDNAmode==0x30){ //Race
					if(currentSchizzaforteMap=='R') return 0; //map applied
				}else{ //A, N, D → Natural map
					if(currentSchizzaforteMap=='N') return 0; //map applied
				}
				break;
			case 8: //8=Kids Limiter: throttle override, map shall be bypass
				if(currentSchizzaforteMap=='B') return 0; //map applied
			default:
				//return 1; //not correctly applied
		}

		return 1; //not correctly applied
	}

	void sendMainDashboardPageToSlaveBaccable(){
		uint8_t tmpStrLen=0;
		uartTxMsg[0]= BhBusIDparamString;//first char shall be a # to talk with slave canable connected to BH can bus
		char tmpfloatString[5]; //temp array

		// 4WD disabled overlay management // 4wd constraint relax change 24/08/2026
		// writes go straight into uartTxMsg (the transient send buffer), never into
		// dashboard_main_menu_array: that array is persistent menu label storage, and many
		// switch cases below only patch a few characters or none at all, so overwriting a
		// whole row there would permanently corrupt that page's label after the overlay clears
		if(function_4wd_disabler_enabled && _4wd_disabled > 0) { // 4wd constraint relax change 24/08/2026
			if(currentTime - last_4wd_disabled_overlay_time >= 6000) { // 4wd constraint relax change 24/08/2026
				last_4wd_disabled_overlay_time = currentTime; // 4wd constraint relax change 24/08/2026
				show_4wd_disabled_overlay = 1; // 4wd constraint relax change 24/08/2026
			} // 4wd constraint relax change 24/08/2026
			if(show_4wd_disabled_overlay) { // 4wd constraint relax change 24/08/2026
				if(currentTime - last_4wd_disabled_overlay_time > 1000) { // 4wd constraint relax change 24/08/2026
					show_4wd_disabled_overlay = 0; // 1 sec elapsed. hide overlay // 4wd constraint relax change 24/08/2026
				} // 4wd constraint relax change 24/08/2026
				memset(&uartTxMsg[1], ' ', DASHBOARD_MESSAGE_MAX_LENGTH); // 4wd constraint relax change 24/08/2026
				uint8_t msg[] = ">>4WD DISABLED<<"; // 4wd constraint relax change 24/08/2026
				memcpy(&uartTxMsg[1], msg, 16); // 4wd constraint relax change 24/08/2026
				addToUARTSendQueue(uartTxMsg, UART_BUFFER_SIZE); // 4wd constraint relax change 24/08/2026
				return; // 4wd constraint relax change 24/08/2026
			} // 4wd constraint relax change 24/08/2026
		} // 4wd constraint relax change 24/08/2026

		//update records if required
		switch(main_dashboardPageIndex){
			case 2: //READ_FAULTS_ENABLED //readFaults 12/08/2026
				if(function_read_faults_enabled==1 && dashboard_menu_indent_level==1){
					static const char hx[16]={'0','1','2','3','4','5','6','7','8','9','A','B','C','D','E','F'};
					memset(dashboard_main_menu_array[2], ' ', DASHBOARD_MESSAGE_MAX_LENGTH);
					switch(faultsStateMachine){
						case 0: case 1: case 2: // in attesa risposta BODY o ECM //readFaults ECM 10/10/2026
							dashboard_main_menu_array[2][0]='W';
							dashboard_main_menu_array[2][1]='A';
							dashboard_main_menu_array[2][2]='I';
							dashboard_main_menu_array[2][3]='T';
							break;
						case 3: // lista DTC disponibile
							if(faultsDTCcount==0){
								dashboard_main_menu_array[2][0]='N';
								dashboard_main_menu_array[2][1]='O';
								dashboard_main_menu_array[2][2]=' ';
								dashboard_main_menu_array[2][3]='F';
								dashboard_main_menu_array[2][4]='A';
								dashboard_main_menu_array[2][5]='U';
								dashboard_main_menu_array[2][6]='L';
								dashboard_main_menu_array[2][7]='T';
								dashboard_main_menu_array[2][8]='S';
							}else{
								uint8_t b0=faultsDTCbytes[faultsDTCsubmenuIndex][0];
								uint8_t b1=faultsDTCbytes[faultsDTCsubmenuIndex][1];
								uint8_t b2=faultsDTCbytes[faultsDTCsubmenuIndex][2];
								// readFaults fix 05/10/2026 - DTC in formato SAE J2012, come negli strumenti di diagnosi:
								// "BODY B10AA-4A 1/2". I 2 bit alti del primo byte danno la lettera (P/C/B/U), i 2 successivi
								// la prima cifra, poi 3 cifre esadecimali; il terzo byte e' il tipo di guasto (FTB) dopo il
								// trattino. Prima si mostravano i 3 byte grezzi ("BODY 90AA4A").
								static const char dtcLetter[4]={'P','C','B','U'};
								// readFaults ECM 10/10/2026 - prefisso della ECU: i primi faultsDTCbodyCount guasti sono del BODY, i
								// successivi dell'ECM. "ENGINE " non ci sta nei 18 caratteri insieme al contatore: sul display
								// standard si usa "ECM" (allineato a "BODY", codice dalla colonna 5), sul display grande "ENGINE".
								#if DASHBOARD_MESSAGE_MAX_LENGTH >= 24
									static const char ecmPrefix[]="ENGINE ";
								#else
									static const char ecmPrefix[]="ECM  ";
								#endif
								static const char bodyPrefix[]="BODY ";
								static const char absPrefix[]="ABS  "; //readFaults ABS 10/10/2026
								const char* prefix=(faultsDTCsubmenuIndex<faultsDTCbodyCount) ? bodyPrefix : ((faultsDTCsubmenuIndex<faultsDTCecmEnd) ? ecmPrefix : absPrefix);
								uint8_t c=0; // colonna corrente
								while(prefix[c]){ dashboard_main_menu_array[2][c]=prefix[c]; c++; }
								dashboard_main_menu_array[2][c++]=dtcLetter[b0>>6];
								dashboard_main_menu_array[2][c++]=(char)('0'+((b0>>4)&0x3));
								dashboard_main_menu_array[2][c++]=hx[b0&0xF];
								dashboard_main_menu_array[2][c++]=hx[b1>>4];
								dashboard_main_menu_array[2][c++]=hx[b1&0xF];
								dashboard_main_menu_array[2][c++]='-';
								dashboard_main_menu_array[2][c++]=hx[b2>>4];
								dashboard_main_menu_array[2][c++]=hx[b2&0xF];
								// Contatore dopo uno spazio (colonna 14 con BODY/ECM; la riga ha 18 caratteri): "n/m" per n da 1 a 9 ("9/40" = 4
								// caratteri), solo "n" da 10 in poi ("10/40" non ci starebbe). m e' il totale dei guasti validi
								// nella risposta, anche oltre i FAULTS_DTC_MAX della lista: con 40 guasti si scorre da 1/40 a 20
								// e si sa che ce ne sono altri. Oltre 99 si mostra 99 (non ci sono altri caratteri).
								uint8_t n=(uint8_t)(faultsDTCsubmenuIndex+1);
								uint8_t m=(faultsDTCtotal>99)?99:(uint8_t)faultsDTCtotal;
								uint8_t pos=(uint8_t)(c+1); //readFaults ECM 10/10/2026
								if(n<10){
									dashboard_main_menu_array[2][pos++]=(char)('0'+n);
									dashboard_main_menu_array[2][pos++]='/';
									if(m>=10) dashboard_main_menu_array[2][pos++]=(char)('0'+m/10);
									dashboard_main_menu_array[2][pos]=(char)('0'+m%10);
								}else{
									dashboard_main_menu_array[2][pos++]=(char)('0'+n/10);
									dashboard_main_menu_array[2][pos]=(char)('0'+n%10);
								}
							}
							break;
						case 4: // TIMEOUT
							dashboard_main_menu_array[2][0]='T';
							dashboard_main_menu_array[2][1]='I';
							dashboard_main_menu_array[2][2]='M';
							dashboard_main_menu_array[2][3]='E';
							dashboard_main_menu_array[2][4]='O';
							dashboard_main_menu_array[2][5]='U';
							dashboard_main_menu_array[2][6]='T';
							break;
						default:
							break;
					}
				}else if(dashboard_menu_indent_level==0){
					//readFaults fix 05/10/2026 - while reading, WAIT / DTC / TIMEOUT are written into this very row of the main
					//menu: back on the main menu (RES, timeout, end of list) the row kept the last DTC shown instead of the
					//menu entry. Put the label back whenever the main menu is shown.
					static const uint8_t readFaultsLabel[]={'R','e','a','d',' ','F','a','u','l','t','s'};
					memset(dashboard_main_menu_array[2], ' ', DASHBOARD_MESSAGE_MAX_LENGTH);
					memcpy(dashboard_main_menu_array[2], readFaultsLabel, sizeof(readFaultsLabel));
				}
				break;
			case 3:
				if(function_clear_faults_enabled==1){
					if(clearFaultsRequest>0){
						memcpy(dashboard_main_menu_array[main_dashboardPageIndex], "WAIT...     ", 12);
						commandsMenuEnabled=0; //disable menu movement
					}else{
						memcpy(dashboard_main_menu_array[main_dashboardPageIndex], "CLEAR FAULTS", 12);
						commandsMenuEnabled=1; //enable menu movement
					}
				}
				break;
			case 4: //immo
				if(immobilizerEnabled){
					dashboard_main_menu_array[main_dashboardPageIndex][14]='N'; //on
					dashboard_main_menu_array[main_dashboardPageIndex][15]=' ';
				}else{
					dashboard_main_menu_array[main_dashboardPageIndex][14]='F'; //off
					dashboard_main_menu_array[main_dashboardPageIndex][15]='F';
				}
				break;
			case 5: //dyno
				if(printStopTheCar>0){
					printStopTheCar--;
					uint8_t stopTheCarMsg[13]={BhBusIDparamString,'S','T','O','P',' ','T','H','E',' ','C','A','R'};
					addToUARTSendQueue(stopTheCarMsg, 13);//print message "stop the car"
					return;
				}
				break;
			case 6: //ESC/TC
				break;
			case 7: //front brake
				if(printStopTheCar>0){
					printStopTheCar--;
					uint8_t stopTheCarMsg[13]={BhBusIDparamString,'S','T','O','P',' ','T','H','E',' ','C','A','R'};
					addToUARTSendQueue(stopTheCarMsg, 13);//print message "stop the car"
					return;
				}

				if(printEnableDyno>0){
					printEnableDyno--;
					uint8_t enableDynoMsg[12]={BhBusIDparamString,'E','N','A','B','L','E',' ','D','Y','N','O'};
					addToUARTSendQueue(enableDynoMsg, 12);//print message "Enable Dyno"
					return;
				}
				//update the string
				if(front_brake_forced==0){
					//update text {'F','r','o','n','t',' ','B','r','a','k','e',' ','N','o','r','m','a','l' },
					dashboard_main_menu_array[main_dashboardPageIndex][0]='F';
					dashboard_main_menu_array[main_dashboardPageIndex][1]='r';
					dashboard_main_menu_array[main_dashboardPageIndex][2]='o';
					dashboard_main_menu_array[main_dashboardPageIndex][3]='n';
					dashboard_main_menu_array[main_dashboardPageIndex][4]='t';
					dashboard_main_menu_array[main_dashboardPageIndex][5]=' ';
					dashboard_main_menu_array[main_dashboardPageIndex][6]='B';
					dashboard_main_menu_array[main_dashboardPageIndex][7]='r';
					dashboard_main_menu_array[main_dashboardPageIndex][8]='a';
					dashboard_main_menu_array[main_dashboardPageIndex][9]='k';
					dashboard_main_menu_array[main_dashboardPageIndex][10]='e';
					dashboard_main_menu_array[main_dashboardPageIndex][11]=' ';
					dashboard_main_menu_array[main_dashboardPageIndex][12]='N'; //normal
					dashboard_main_menu_array[main_dashboardPageIndex][13]='o'; //
					dashboard_main_menu_array[main_dashboardPageIndex][14]='r'; //
					dashboard_main_menu_array[main_dashboardPageIndex][15]='m';
					dashboard_main_menu_array[main_dashboardPageIndex][16]='a';
					dashboard_main_menu_array[main_dashboardPageIndex][17]='l';
				}else{
					if(launch_assist_enabled==1){
						if(torque>50){ //assist active and torque greather than minimum threshold. the minimum thr allows to view the menu "...assist" before the following string is printed
							//prepare variables

							//show torque
							dashboard_main_menu_array[main_dashboardPageIndex][0]='L';
							dashboard_main_menu_array[main_dashboardPageIndex][1]='a';
							dashboard_main_menu_array[main_dashboardPageIndex][2]='u';
							dashboard_main_menu_array[main_dashboardPageIndex][3]='n';
							dashboard_main_menu_array[main_dashboardPageIndex][4]='c';
							dashboard_main_menu_array[main_dashboardPageIndex][5]='h';
							dashboard_main_menu_array[main_dashboardPageIndex][6]=' ';

							floatToStr(tmpfloatString,(float)torque,0,4);
							switch(strlen(tmpfloatString)){
								case 1:
									dashboard_main_menu_array[main_dashboardPageIndex][7]=' ';
									dashboard_main_menu_array[main_dashboardPageIndex][8]=' ';
									dashboard_main_menu_array[main_dashboardPageIndex][9]=tmpfloatString[0];
									break;
								case 2:
									dashboard_main_menu_array[main_dashboardPageIndex][7]=' ';
									dashboard_main_menu_array[main_dashboardPageIndex][8]=tmpfloatString[0];
									dashboard_main_menu_array[main_dashboardPageIndex][9]=tmpfloatString[1];
									break;
								default:
									dashboard_main_menu_array[main_dashboardPageIndex][7]=tmpfloatString[0];
									dashboard_main_menu_array[main_dashboardPageIndex][8]=tmpfloatString[1];
									dashboard_main_menu_array[main_dashboardPageIndex][9]=tmpfloatString[2];
									break;
							}

							dashboard_main_menu_array[main_dashboardPageIndex][10]='N';
							dashboard_main_menu_array[main_dashboardPageIndex][11]='m';
							dashboard_main_menu_array[main_dashboardPageIndex][12]='/';

							floatToStr(tmpfloatString,(float)launch_torque_threshold,0,4);
							if(strlen(tmpfloatString)==2){
								dashboard_main_menu_array[main_dashboardPageIndex][13]=' ';
								dashboard_main_menu_array[main_dashboardPageIndex][14]=tmpfloatString[0];
								dashboard_main_menu_array[main_dashboardPageIndex][15]=tmpfloatString[1];
							}else{
								dashboard_main_menu_array[main_dashboardPageIndex][13]=tmpfloatString[0];
								dashboard_main_menu_array[main_dashboardPageIndex][14]=tmpfloatString[1];
								dashboard_main_menu_array[main_dashboardPageIndex][15]=tmpfloatString[2];
							}

							dashboard_main_menu_array[main_dashboardPageIndex][16]='N';
							dashboard_main_menu_array[main_dashboardPageIndex][17]='m';
						}else{
							//update text
							dashboard_main_menu_array[main_dashboardPageIndex][0]='F';
							dashboard_main_menu_array[main_dashboardPageIndex][1]='r';
							dashboard_main_menu_array[main_dashboardPageIndex][2]='o';
							dashboard_main_menu_array[main_dashboardPageIndex][3]='n';
							dashboard_main_menu_array[main_dashboardPageIndex][4]='t';
							dashboard_main_menu_array[main_dashboardPageIndex][5]=' ';
							dashboard_main_menu_array[main_dashboardPageIndex][6]='B';
							dashboard_main_menu_array[main_dashboardPageIndex][7]='r';
							dashboard_main_menu_array[main_dashboardPageIndex][8]='a';
							dashboard_main_menu_array[main_dashboardPageIndex][9]='k';
							dashboard_main_menu_array[main_dashboardPageIndex][10]='e';
							dashboard_main_menu_array[main_dashboardPageIndex][11]=' ';
							dashboard_main_menu_array[main_dashboardPageIndex][12]='A'; //assist (launch control)
							dashboard_main_menu_array[main_dashboardPageIndex][13]='s'; //
							dashboard_main_menu_array[main_dashboardPageIndex][14]='s'; //
							dashboard_main_menu_array[main_dashboardPageIndex][15]='i';
							dashboard_main_menu_array[main_dashboardPageIndex][16]='s';
							dashboard_main_menu_array[main_dashboardPageIndex][17]='t';
						}
					}else{ //launch assist not enabled
						//update text
						dashboard_main_menu_array[main_dashboardPageIndex][0]='F';
						dashboard_main_menu_array[main_dashboardPageIndex][1]='r';
						dashboard_main_menu_array[main_dashboardPageIndex][2]='o';
						dashboard_main_menu_array[main_dashboardPageIndex][3]='n';
						dashboard_main_menu_array[main_dashboardPageIndex][4]='t';
						dashboard_main_menu_array[main_dashboardPageIndex][5]=' ';
						dashboard_main_menu_array[main_dashboardPageIndex][6]='B';
						dashboard_main_menu_array[main_dashboardPageIndex][7]='r';
						dashboard_main_menu_array[main_dashboardPageIndex][8]='a';
						dashboard_main_menu_array[main_dashboardPageIndex][9]='k';
						dashboard_main_menu_array[main_dashboardPageIndex][10]='e';
						dashboard_main_menu_array[main_dashboardPageIndex][11]=' ';
						dashboard_main_menu_array[main_dashboardPageIndex][12]='F'; //forced
						dashboard_main_menu_array[main_dashboardPageIndex][13]='o'; //
						dashboard_main_menu_array[main_dashboardPageIndex][14]='r'; //
						dashboard_main_menu_array[main_dashboardPageIndex][15]='c';
						dashboard_main_menu_array[main_dashboardPageIndex][16]='e';
						dashboard_main_menu_array[main_dashboardPageIndex][17]='d';
					}
				}
				break;
			case 8: //4wd
				if(printStopTheCar>0){
					printStopTheCar--;
					uint8_t stopTheCarMsg[13]={BhBusIDparamString,'S','T','O','P',' ','T','H','E',' ','C','A','R'};
					addToUARTSendQueue(stopTheCarMsg, 13);//print message "stop the car"
					return;
				}
				//nothing to do
				break;
			case 15: //Max Hold: update ON/OFF text
				dashboard_main_menu_array[15][10] = maxHold_enabled ? 'N' : 'F';
				dashboard_main_menu_array[15][11] = maxHold_enabled ? ' ' : 'F';
				break;
			default:
				//nothing to do
				break;
		}

		//add string to record
		switch(main_dashboardPageIndex){
			case 0:
				tmpStrLen=strlen(FW_VERSION);
				if(tmpStrLen>DASHBOARD_MESSAGE_MAX_LENGTH) tmpStrLen=DASHBOARD_MESSAGE_MAX_LENGTH;
				memcpy(&uartTxMsg[1],FW_VERSION,tmpStrLen);
				if (tmpStrLen < DASHBOARD_MESSAGE_MAX_LENGTH) { //if required pad with spaces
					memset(&uartTxMsg[1+tmpStrLen], ' ', UART_BUFFER_SIZE-(1+tmpStrLen)); //set to zero remaining chars
				}
				break;
			default:
				memcpy(&uartTxMsg[1], dashboard_main_menu_array[main_dashboardPageIndex],UART_BUFFER_SIZE-1);
				break;
		}



		//send to slave baccable
		addToUARTSendQueue(uartTxMsg, UART_BUFFER_SIZE);

	}

	void sendSetupDashboardPageToSlaveBaccable(){
		//uint8_t tmpStrLen=0;
		uartTxMsg[0]= BhBusIDparamString;//first char shall be a # to talk with slave canable connected to BH can bus

		char tmpfloatString[5]; //temp array for shift and launch threshods
		//update records if required
		switch(setup_dashboardPageIndex){
			case 0: //{'S','A','V','E','&','E','X','I','T',},
				break;
			case 1: //{'[',' ',']','S','t','a','r','t','&','S','t','o','p'},
				dashboard_setup_menu_array[setup_dashboardPageIndex][0]=checkbox_symbols[function_smart_disable_start_stop_enabled];
				break;
			case 2: //{'[',' ',']','-','-','-','-','-','-','-','-','-','-','-',},
				floatToStr(tmpfloatString,(float)launch_torque_threshold,0,4);
				if(strlen(tmpfloatString)==2){
					dashboard_setup_menu_array[setup_dashboardPageIndex][13]=' ';
					dashboard_setup_menu_array[setup_dashboardPageIndex][14]=tmpfloatString[0];
					dashboard_setup_menu_array[setup_dashboardPageIndex][15]=tmpfloatString[1];
				}else{
					dashboard_setup_menu_array[setup_dashboardPageIndex][13]=tmpfloatString[0];
					dashboard_setup_menu_array[setup_dashboardPageIndex][14]=tmpfloatString[1];
					dashboard_setup_menu_array[setup_dashboardPageIndex][15]=tmpfloatString[2];
				}


				break;
			case 3: //{'[',' ',']','L','e','d',' ','C','o','n','t','r','o','l','l','e','r',},
				dashboard_setup_menu_array[setup_dashboardPageIndex][0]=checkbox_symbols[function_led_strip_controller_enabled];
				break;
			case 4: //{'[',' ',']','S','h','i','f','t',' ','I','n','d','i','c','a','t','o','r'},
				dashboard_setup_menu_array[setup_dashboardPageIndex][0]=checkbox_symbols[function_shift_indicator_enabled];
				break;
			case 5: //{'S','h','i','f','t',' ','R','P','M',' ','3','0','0','0',},
				floatToStr(tmpfloatString,(float)shift_threshold,0,5);
				dashboard_setup_menu_array[setup_dashboardPageIndex][10]=tmpfloatString[0];
				dashboard_setup_menu_array[setup_dashboardPageIndex][11]=tmpfloatString[1];
				dashboard_setup_menu_array[setup_dashboardPageIndex][12]=tmpfloatString[2];
				dashboard_setup_menu_array[setup_dashboardPageIndex][13]=tmpfloatString[3];
				break;
			case 6: //{'[',' ',']','M','y','2','3',' ','I','P','C', },
				dashboard_setup_menu_array[setup_dashboardPageIndex][0]=checkbox_symbols[function_ipc_my23_is_installed];
				break;
			case 7: //{'O',' ',' ','R','e','g','e','n','.',' ','A','l','e','r','t',' ',' ',' '},
				dashboard_setup_menu_array[setup_dashboardPageIndex][0]=checkbox_symbols[function_regeneration_alert_enabled];
				break;
			case 8: //{'O',' ',' ','S','e','a','t','b','e','l','t',' ','A','l','a','r','m',' '},
				dashboard_setup_menu_array[setup_dashboardPageIndex][0]=checkbox_symbols[function_seatbelt_alarm_enabled];
				break;
			case 9: //{'[',' ',']','R','o','u','t','e',' ','M','e','s','s','a','g','e','s', },
				dashboard_setup_menu_array[setup_dashboardPageIndex][0]=checkbox_symbols[function_route_msg_enabled];
				break;
			case 10: //{'[',' ',']','E','S','C','/','T','C',' ','C','u','s','t','o','m','.',},
				dashboard_setup_menu_array[setup_dashboardPageIndex][0]=checkbox_symbols[function_esc_tc_customizator_enabled];
				break;
			case 11: //{'[',' ',']','D','y','n','o',},
				dashboard_setup_menu_array[setup_dashboardPageIndex][0]=checkbox_symbols[function_dyno_mode_master_enabled];
				break;
			case 12: //{'[',' ',']','A','C','C',' ','V','i','r','t','u','a','l',' ','P','a','d'},
				dashboard_setup_menu_array[setup_dashboardPageIndex][0]=checkbox_symbols[function_acc_virtual_pad_enabled];
				break;
			case 13: //{'[',' ',']','B','r','a','k','e','s',' ','O','v','e','r','r','i','d','e'},
				dashboard_setup_menu_array[setup_dashboardPageIndex][0]=checkbox_symbols[function_front_brake_forcer_master];
				break;
			case 14: //{'[',' ',']','4','W','D',' ','D','i','s','a','b','l','e','r',},
				dashboard_setup_menu_array[setup_dashboardPageIndex][0]=checkbox_symbols[function_4wd_disabler_enabled];
				break;
			case 15: //{'[',' ',']','C','l','e','a','r',' ','F','a','u','l','t','s',},
				dashboard_setup_menu_array[setup_dashboardPageIndex][0]=checkbox_symbols[function_clear_faults_enabled];
				break;
			case 16: //{'[',' ',']','R','e','a','d',' ',' ','F','a','u','l','t','s',},
				dashboard_setup_menu_array[setup_dashboardPageIndex][0]=checkbox_symbols[function_read_faults_enabled];
				break;
			case 17: //{'[',' ',']','R','e','m','o','t','e',' ','S','t','a','r','t',},
				dashboard_setup_menu_array[setup_dashboardPageIndex][0]=checkbox_symbols[function_remote_start_Enabled];
				break;
			case 18: //{'Ø',' ',' ','D','i','e','s','e','l',' ',' ',' ','P','a','r','a','m','s'},
				if(function_is_diesel_enabled){
					dashboard_setup_menu_array[setup_dashboardPageIndex][3] ='D';
					dashboard_setup_menu_array[setup_dashboardPageIndex][4] ='i';
					dashboard_setup_menu_array[setup_dashboardPageIndex][5] ='e';
					dashboard_setup_menu_array[setup_dashboardPageIndex][6] ='s';
					dashboard_setup_menu_array[setup_dashboardPageIndex][7] ='e';
					dashboard_setup_menu_array[setup_dashboardPageIndex][8] ='l';
					dashboard_setup_menu_array[setup_dashboardPageIndex][9] =' ';
					dashboard_setup_menu_array[setup_dashboardPageIndex][10]=' ';
				}else{
					dashboard_setup_menu_array[setup_dashboardPageIndex][3] ='G';
					dashboard_setup_menu_array[setup_dashboardPageIndex][4] ='a';
					dashboard_setup_menu_array[setup_dashboardPageIndex][5] ='s';
					dashboard_setup_menu_array[setup_dashboardPageIndex][6] ='o';
					dashboard_setup_menu_array[setup_dashboardPageIndex][7] ='l';
					dashboard_setup_menu_array[setup_dashboardPageIndex][8] ='i';
					dashboard_setup_menu_array[setup_dashboardPageIndex][9] ='n';
					dashboard_setup_menu_array[setup_dashboardPageIndex][10]='e';
				}
				break;
			case 19: //odometer blink
				dashboard_setup_menu_array[setup_dashboardPageIndex][0]=checkbox_symbols[function_disable_odometer_blink];
				break;
			case 20: //{'[',' ',']','P','e','d','a','l',' ','B','o','o','s','t','e','r'},
				dashboard_setup_menu_array[setup_dashboardPageIndex][0]=checkbox_symbols[!!function_pedal_booster_enabled]; // double ! coerces to bool
				switch(function_pedal_booster_enabled){
					case 0: //off
						dashboard_setup_menu_array[setup_dashboardPageIndex][10]='o';
						dashboard_setup_menu_array[setup_dashboardPageIndex][11]='o';
						dashboard_setup_menu_array[setup_dashboardPageIndex][12]='s';
						dashboard_setup_menu_array[setup_dashboardPageIndex][13]='t';
						dashboard_setup_menu_array[setup_dashboardPageIndex][14]='e';
						dashboard_setup_menu_array[setup_dashboardPageIndex][15]='r';
						dashboard_setup_menu_array[setup_dashboardPageIndex][16]=' ';
						dashboard_setup_menu_array[setup_dashboardPageIndex][17]=' ';


						break;
					case 1: //Auto
						dashboard_setup_menu_array[setup_dashboardPageIndex][10]='.';
						dashboard_setup_menu_array[setup_dashboardPageIndex][11]=' ';
						dashboard_setup_menu_array[setup_dashboardPageIndex][12]='A';
						dashboard_setup_menu_array[setup_dashboardPageIndex][13]='u';
						dashboard_setup_menu_array[setup_dashboardPageIndex][14]='t';
						dashboard_setup_menu_array[setup_dashboardPageIndex][15]='o';
						dashboard_setup_menu_array[setup_dashboardPageIndex][16]=' ';
						dashboard_setup_menu_array[setup_dashboardPageIndex][17]=' ';
						break;
					case 2: //Bypass
						dashboard_setup_menu_array[setup_dashboardPageIndex][10]='.';
						dashboard_setup_menu_array[setup_dashboardPageIndex][11]=' ';
						dashboard_setup_menu_array[setup_dashboardPageIndex][12]='B';
						dashboard_setup_menu_array[setup_dashboardPageIndex][13]='y';
						dashboard_setup_menu_array[setup_dashboardPageIndex][14]='p';
						dashboard_setup_menu_array[setup_dashboardPageIndex][15]='a';
						dashboard_setup_menu_array[setup_dashboardPageIndex][16]='s';
						dashboard_setup_menu_array[setup_dashboardPageIndex][17]='s';
						break;
					case 3: //All Weather Map
						dashboard_setup_menu_array[setup_dashboardPageIndex][10]='.';
						dashboard_setup_menu_array[setup_dashboardPageIndex][11]=' ';
						dashboard_setup_menu_array[setup_dashboardPageIndex][12]='A';
						dashboard_setup_menu_array[setup_dashboardPageIndex][13]=' ';
						dashboard_setup_menu_array[setup_dashboardPageIndex][14]='M';
						dashboard_setup_menu_array[setup_dashboardPageIndex][15]='a';
						dashboard_setup_menu_array[setup_dashboardPageIndex][16]='p';
						dashboard_setup_menu_array[setup_dashboardPageIndex][17]=' ';
						break;
					case 4: //Natural Map
						dashboard_setup_menu_array[setup_dashboardPageIndex][10]='.';
						dashboard_setup_menu_array[setup_dashboardPageIndex][11]=' ';
						dashboard_setup_menu_array[setup_dashboardPageIndex][12]='N';
						dashboard_setup_menu_array[setup_dashboardPageIndex][13]=' ';
						dashboard_setup_menu_array[setup_dashboardPageIndex][14]='M';
						dashboard_setup_menu_array[setup_dashboardPageIndex][15]='a';
						dashboard_setup_menu_array[setup_dashboardPageIndex][16]='p';
						dashboard_setup_menu_array[setup_dashboardPageIndex][17]=' ';
						break;
					case 5: //Dynamic Map
						dashboard_setup_menu_array[setup_dashboardPageIndex][10]='.';
						dashboard_setup_menu_array[setup_dashboardPageIndex][11]=' ';
						dashboard_setup_menu_array[setup_dashboardPageIndex][12]='D';
						dashboard_setup_menu_array[setup_dashboardPageIndex][13]=' ';
						dashboard_setup_menu_array[setup_dashboardPageIndex][14]='M';
						dashboard_setup_menu_array[setup_dashboardPageIndex][15]='a';
						dashboard_setup_menu_array[setup_dashboardPageIndex][16]='p';
						dashboard_setup_menu_array[setup_dashboardPageIndex][17]=' ';
						break;
					case 6: //Race Map
						dashboard_setup_menu_array[setup_dashboardPageIndex][10]='.';
						dashboard_setup_menu_array[setup_dashboardPageIndex][11]=' ';
						dashboard_setup_menu_array[setup_dashboardPageIndex][12]='R';
						dashboard_setup_menu_array[setup_dashboardPageIndex][13]=' ';
						dashboard_setup_menu_array[setup_dashboardPageIndex][14]='M';
						dashboard_setup_menu_array[setup_dashboardPageIndex][15]='a';
						dashboard_setup_menu_array[setup_dashboardPageIndex][16]='p';
						dashboard_setup_menu_array[setup_dashboardPageIndex][17]=' ';
						break;
					case 7: //Hybrid Align
						dashboard_setup_menu_array[setup_dashboardPageIndex][10]='.';
						dashboard_setup_menu_array[setup_dashboardPageIndex][11]=' ';
						dashboard_setup_menu_array[setup_dashboardPageIndex][12]='H';
						dashboard_setup_menu_array[setup_dashboardPageIndex][13]='y';
						dashboard_setup_menu_array[setup_dashboardPageIndex][14]='b';
						dashboard_setup_menu_array[setup_dashboardPageIndex][15]='r';
						dashboard_setup_menu_array[setup_dashboardPageIndex][16]='i';
						dashboard_setup_menu_array[setup_dashboardPageIndex][17]='d';
						break;
					case 8: //Kids Limiter
						dashboard_setup_menu_array[setup_dashboardPageIndex][10]='.';
						dashboard_setup_menu_array[setup_dashboardPageIndex][11]=' ';
						dashboard_setup_menu_array[setup_dashboardPageIndex][12]='K';
						dashboard_setup_menu_array[setup_dashboardPageIndex][13]='i';
						dashboard_setup_menu_array[setup_dashboardPageIndex][14]='d';
						dashboard_setup_menu_array[setup_dashboardPageIndex][15]='s';
						dashboard_setup_menu_array[setup_dashboardPageIndex][16]=' ';
						dashboard_setup_menu_array[setup_dashboardPageIndex][17]=' ';
						break;
					default: //we will never end here
						break;
				}
				break;
			case 21: // 'P','e','d','a','l',' ','P','o','w','e','r',':',' ','0',' ',' ',' ',' '
				floatToStr(tmpfloatString,(float)pedal_map_power,0,4);
				dashboard_setup_menu_array[setup_dashboardPageIndex][12]=tmpfloatString[0];
				dashboard_setup_menu_array[setup_dashboardPageIndex][13]=tmpfloatString[1];
				dashboard_setup_menu_array[setup_dashboardPageIndex][14]=tmpfloatString[2];
				dashboard_setup_menu_array[setup_dashboardPageIndex][15]=tmpfloatString[3];
				break;
			case 22:
				dashboard_setup_menu_array[setup_dashboardPageIndex][0]=checkbox_symbols[function_park_mirror];
				break;
			case 23:
				dashboard_setup_menu_array[setup_dashboardPageIndex][0]=checkbox_symbols[!!function_acc_autostart];
				switch(function_acc_autostart){
					case 0: //off
						dashboard_setup_menu_array[setup_dashboardPageIndex][17]=' ';
						break;
					case 1: //simulates RES button press
						dashboard_setup_menu_array[setup_dashboardPageIndex][17]='R';
						break;
					case 2: //simulates + button press
						dashboard_setup_menu_array[setup_dashboardPageIndex][17]='+';
						break;
					default: //we will never end here
						break;
				}
				break;
			case 24:
				dashboard_setup_menu_array[setup_dashboardPageIndex][0]=checkbox_symbols[!!function_close_windows_with_door_lock];
				switch(function_close_windows_with_door_lock){
					case 0: //off
						dashboard_setup_menu_array[setup_dashboardPageIndex][17]=' ';
						break;
					case 1: //Close Windows 1
						dashboard_setup_menu_array[setup_dashboardPageIndex][17]='1';
						break;
					case 2: //Close Windows 2
						dashboard_setup_menu_array[setup_dashboardPageIndex][17]='2';
						break;
					default: //we will never end here
						break;
				}
				break;
			case 25:
				dashboard_setup_menu_array[setup_dashboardPageIndex][0]=checkbox_symbols[!!function_open_windows_with_door_lock];
				switch(function_open_windows_with_door_lock){
					case 0: //off
						dashboard_setup_menu_array[setup_dashboardPageIndex][17]=' ';
						break;
					case 1: //Close Windows 1
						dashboard_setup_menu_array[setup_dashboardPageIndex][17]='1';
						break;
					case 2: //Close Windows 2
						dashboard_setup_menu_array[setup_dashboardPageIndex][17]='2';
						break;
					default: //we will never end here
						break;
				}
				break;
			case 26:
				dashboard_setup_menu_array[setup_dashboardPageIndex][0]=checkbox_symbols[HAS_function_enabled];
				break;
			case 27:
				dashboard_setup_menu_array[setup_dashboardPageIndex][0]=checkbox_symbols[QV_exhaust_flap_function_enabled];
				break;
			case 28: //{'O',' ',' ','F','r','o','n','t',' ','P','a','r','k',' ','M','u','t','e'}
				dashboard_setup_menu_array[setup_dashboardPageIndex][0]=checkbox_symbols[parkSensorsMuteFunctionEnabled];
				break;
			case 29: //{'O',' ',' ','S','N','I','F','F','E','R'} //sniffer function 24/08/2026
				dashboard_setup_menu_array[setup_dashboardPageIndex][0]=checkbox_symbols[snifferFunctionEnabled];
				break;
			case 30: //{'O',' ',' ','E','L','M','3','2','7'} //elm327 function 26/08/2026
				dashboard_setup_menu_array[setup_dashboardPageIndex][0]=checkbox_symbols[elm327FunctionEnabled];
				break;
			default:
				break;
		}

		memcpy(&uartTxMsg[1], &dashboard_setup_menu_array[setup_dashboardPageIndex],UART_BUFFER_SIZE-1);
		//send to slave baccable
		addToUARTSendQueue(uartTxMsg, UART_BUFFER_SIZE);


	}

	void sendParamsSetupDashboardPageToSlaveBaccable(){
		uartTxMsg[0]= BhBusIDparamString;//first char shall be a # to talk with slave canable connected to BH can bus
		switch(params_setup_dashboardPageIndex){
			case 0: //{'S','A','V','E','&','E','X','I','T',},
				uartTxMsg[1]='S';
				uartTxMsg[2]='A';
				uartTxMsg[3]='V';
				uartTxMsg[4]='E';
				uartTxMsg[5]=' ';
				uartTxMsg[6]='&';
				uartTxMsg[7]=' ';
				uartTxMsg[8]='E';
				uartTxMsg[9]='X';
				uartTxMsg[10]='I';
				uartTxMsg[11]='T';
				uartTxMsg[12]=0;
				uartTxMsg[13]=0;
				uartTxMsg[14]=0;
				uartTxMsg[15]=0;
				uartTxMsg[16]=0;
				uartTxMsg[17]=0;
				uartTxMsg[18]=0;

				break;
			default: //hidden or shown params
				uartTxMsg[1]=checkbox_symbols[shownParamsArray[params_setup_dashboardPageIndex-1]];
				uartTxMsg[2]=' ';
				uartTxMsg[3]=' ';

				char tmpName[DASHBOARD_MESSAGE_MAX_LENGTH + 5];

				memcpy(
				    tmpName,
				    uds_params_array[function_is_diesel_enabled][params_setup_dashboardPageIndex - 1].name,
				    strlen(uds_params_array[function_is_diesel_enabled][params_setup_dashboardPageIndex - 1].name) + 1
				);

				uint8_t tmpStrLen=removePatterns(tmpName); //remove special patterns from template
				if(tmpStrLen>UART_BUFFER_SIZE-4) tmpStrLen=UART_BUFFER_SIZE-4;
				memcpy(&uartTxMsg[4], tmpName,tmpStrLen); //copy entire string, to fill it with 0 at the end.
				memset(&uartTxMsg[4+tmpStrLen], 0x20, UART_BUFFER_SIZE-4-tmpStrLen);

				//uint8_t tmpStrLenName=strlen((char *)uds_params_array[function_is_diesel_enabled][params_setup_dashboardPageIndex-1].name);
				//uint8_t tmpStrLenUnits=strlen((char *)single_uds_params_array[uds_params_array[function_is_diesel_enabled][params_setup_dashboardPageIndex-1].udsParamId[currentParamElementSelection]].replyMeasurementUnit);
				//uint8_t tmpCharsToWrite=UART_BUFFER_SIZE-4-tmpStrLenName; //number of chars that we can still use in the string
				//if(tmpCharsToWrite>tmpStrLenUnits+1) tmpCharsToWrite= tmpStrLenUnits+1; //if we have more space than what we have to write, set the total number of chars to write
				//if(tmpCharsToWrite>0){
				//	uartTxMsg[4+tmpStrLenName]=' '; //add a space
				//	tmpCharsToWrite--;
				//}
				//if(tmpCharsToWrite>0) memcpy(&uartTxMsg[4+tmpStrLenName+1], &single_uds_params_array[uds_params_array[function_is_diesel_enabled][params_setup_dashboardPageIndex-1].udsParamId[currentParamElementSelection]].replyMeasurementUnit,tmpCharsToWrite);

				break;
		}

		//send to slave baccable
		addToUARTSendQueue(uartTxMsg, UART_BUFFER_SIZE);


	}

	void sendDashboardPageToSlaveBaccable(){
		uartTxMsg[0]= BhBusIDparamString;//first char shall be a # to talk with slave canable connected to BH can bus

		// 4WD disabled overlay management // 4wd constraint relax change 24/08/2026
		if(function_4wd_disabler_enabled && _4wd_disabled > 0) { // 4wd constraint relax change 24/08/2026
			if(currentTime - last_4wd_disabled_overlay_time >= 5000) { // 4wd constraint relax change 24/08/2026
				last_4wd_disabled_overlay_time = currentTime; // 4wd constraint relax change 24/08/2026
				show_4wd_disabled_overlay = 1; // 4wd constraint relax change 24/08/2026
			} // 4wd constraint relax change 24/08/2026
			if(show_4wd_disabled_overlay) { // 4wd constraint relax change 24/08/2026
				if(currentTime - last_4wd_disabled_overlay_time > 1000) { // 4wd constraint relax change 24/08/2026
					show_4wd_disabled_overlay = 0; // 1 sec elapsed. hide overlay // 4wd constraint relax change 24/08/2026
				} // 4wd constraint relax change 24/08/2026
				memset(&uartTxMsg[1], ' ', DASHBOARD_MESSAGE_MAX_LENGTH); // 4wd constraint relax change 24/08/2026
				uint8_t msg[] = ">>4WD DISABLED<<"; // 4wd constraint relax change 24/08/2026
				memcpy(&uartTxMsg[1], msg, 16); // 4wd constraint relax change 24/08/2026
				addToUARTSendQueue(uartTxMsg, UART_BUFFER_SIZE); // 4wd constraint relax change 24/08/2026
				return; // 4wd constraint relax change 24/08/2026
			} // 4wd constraint relax change 24/08/2026
		} // 4wd constraint relax change 24/08/2026

		char stringToPrint[25];
		buildLineWithFormat( uds_params_array[function_is_diesel_enabled][dashboardPageIndex].name ,  dashboardParamCouple, uds_params_array[function_is_diesel_enabled][dashboardPageIndex].udsParamId, stringToPrint); //build string to print

		uint8_t tmpStrLen=strlen(stringToPrint);
		if(tmpStrLen>DASHBOARD_MESSAGE_MAX_LENGTH) tmpStrLen=DASHBOARD_MESSAGE_MAX_LENGTH; //truncate it. no space left
		memcpy(&uartTxMsg[1], &stringToPrint,tmpStrLen); //prepare name of parameter

		if (tmpStrLen < DASHBOARD_MESSAGE_MAX_LENGTH) { //if required pad with zeros
			memset(&uartTxMsg[1+tmpStrLen], ' ', UART_BUFFER_SIZE-(1+tmpStrLen)); //set to zero remaining chars
		}
		addToUARTSendQueue(uartTxMsg, UART_BUFFER_SIZE);
	}

	float getNativeParam(uint8_t paramId){

		switch(paramId){ //do preliminary additional stuff for special parameters (not uds)
			case 0: //print oil pressure
				return (float) oilPressure * single_uds_params_array[paramId].replyScale;
				break;
			case 1: //power in CV
				return (float)torque * (float)currentRpmSpeed * single_uds_params_array[paramId].replyScale ;
				break;
			case 2: //torque in NM
				return (float)torque;
				break;
			case 3: //battery state of charge (%)
				return (float)batteryStateOfCharge  * single_uds_params_array[paramId].replyScale;
				break;
			case 4: //battery current (A)
				return ((float)batteryCurrent * single_uds_params_array[paramId].replyScale) + single_uds_params_array[paramId].replyScaleOffset;
				break;
			case 5: //engine oil temperature
				return ((float)oilTemperature * single_uds_params_array[paramId].replyScale) + single_uds_params_array[paramId].replyScaleOffset;
				break;
			case 6: //current gear
				return (float)currentGear;
				break;
			case 7: //current speed (km/h)
				return currentSpeed_km_h;
				break;
			case 8: //DPF Regeneration type
				return (float)dieselEngineRegenerationMode;
				break;
			case 9: //stat 0-100km/h
				return chronometerElapsedTime_0_100_km_h; // >=20=MISSED , increase in progress= GO
				break;
			case 10: //stat 100-200km/h
				return chronometerElapsedTime_100_200_km_h; // >=40=MISSED , increase in progress= GO
				break;
			case 11: //Best stat 0-100km/h
				return readStatisticsFromFlash(1);
				break;
			case 12: //Best stat 100-200km/h
				return readStatisticsFromFlash(2);
				break;
			case 13: //seat belt alarm status
				return seatbeltAlarmDisabled;
				break;
			case 14://debug param.
				break;
			case 15://current Drive Style
				return currentDNAmode;
				break;
			case 16://free RAM
				return getFreeRAM();
				break;
			case 17://Pedal current Map
				return currentSchizzaforteMap;
				break;
			case 18://brake pedal press percentage, from 0x107 //brake in show params 10/10/2026
				return brakeTravelStatus;
				break;
			default:
				break;
		}
		return 0;
		}

	//buildLineWithFormat composes string to print, starting from template string and float parameters
	// syntax: $n.yf or $enum
	// n = 0..6 (integer part), y = 0..3 (decimal)

	void buildLineWithFormat(const char* template, float values[2], const uint8_t paramId[2], char* result) {
		//onboardLed_red_blink(5);
	    int i = 0;   // indice output
	    int which = 0; // 0 = val1, 1 = val2

	    for (const char* p = template; *p && i < DASHBOARD_MESSAGE_MAX_LENGTH; p++) {
	        if (*p == '$'){ //special char. it could be a param in the format $x.yf or in the format $enum
	        	if (*(p+2) == '.'){ //it should be a param in the format $x.yf
	        		if(*(p+4) == 'f'){
	        			if ((*(p+1) >= '0' && *(p+1) <= '9')  && (*(p+3) >= '0' && *(p+3) <= '9')) {
							int n = *(p+1) - '0'; // parte intera max
							int y = *(p+3) - '0'; // decimali
							int maxLen = n + (y>0 ? 1 : 0) + y;

							char buf[maxLen+1]; // buffer dimensionato sul campo

							switch(single_uds_params_array[paramId[which]].reqId){
								case 0x1A: //0-100 stat
									if(values[which]>20.0){ //missed
										for (const char* q=speedStatisticEnumStrings[0]; *q && i<DASHBOARD_MESSAGE_MAX_LENGTH ; q++) result[i++] = *q; //MISSED
									}else{
										if(statistics_0_100_started){
											for (const char* q=speedStatisticEnumStrings[1]; *q && i<DASHBOARD_MESSAGE_MAX_LENGTH ; q++) result[i++] = *q; //GO
										}else{ //show time
											floatToStr(buf, values[which], y, maxLen+1);
											for (char* q=buf; *q && i<DASHBOARD_MESSAGE_MAX_LENGTH && (q-buf)<maxLen; q++) result[i++] = *q;
										}
									}
									break;
								case 0x1B: //100-200 stat
									if(values[which]>40.0){ //missed
										for (const char* q=speedStatisticEnumStrings[0]; *q && i<DASHBOARD_MESSAGE_MAX_LENGTH ; q++) result[i++] = *q; //MISSED
									}else{
										if(statistics_100_200_started){
											for (const char* q=speedStatisticEnumStrings[1]; *q && i<DASHBOARD_MESSAGE_MAX_LENGTH ; q++) result[i++] = *q; //GO
										}else{ //show time
											floatToStr(buf, values[which], y, maxLen+1);
											for (char* q=buf; *q && i<DASHBOARD_MESSAGE_MAX_LENGTH && (q-buf)<maxLen; q++) result[i++] = *q;
										}
									}
									break;
								case 0x1C: //Best 0-100
									if(values[which]>20.0){ //missed
										for (const char* q=speedStatisticEnumStrings[0]; *q && i<DASHBOARD_MESSAGE_MAX_LENGTH ; q++) result[i++] = *q; //MISSED
									}else{
										floatToStr(buf, values[which], y, maxLen+1);
										for (char* q=buf; *q && i<DASHBOARD_MESSAGE_MAX_LENGTH && (q-buf)<maxLen; q++) result[i++] = *q;
									}
									break;
								case 0x1D: //Best 100-200
									if(values[which]>40.0){ //missed
										for (const char* q=speedStatisticEnumStrings[0]; *q && i<DASHBOARD_MESSAGE_MAX_LENGTH ; q++) result[i++] = *q; //MISSED
									}else{
										floatToStr(buf, values[which], y, maxLen+1);
										for (char* q=buf; *q && i<DASHBOARD_MESSAGE_MAX_LENGTH && (q-buf)<maxLen; q++) result[i++] = *q;
									}
									break;

								default:
									floatToStr(buf, values[which], y, maxLen+1);

									for (char* q=buf; *q && i<DASHBOARD_MESSAGE_MAX_LENGTH && (q-buf)<maxLen; q++) result[i++] = *q;
							}


							which++;
							p += 4; // salta "n.yf"
	        			}else { result[i++] = *p; }
	        		}else { result[i++] = *p; }
	        	}else if (*(p+4) == 'm'){ //$enum enumerator

	        		switch(single_uds_params_array[paramId[which]].reqId){
						case 0x17: //if Current gear request data - currentGear
							if ((uint8_t)values[which]<11){
								result[i++] = gearArray[(uint8_t)values[which]];
							}else{
								result[i++] = '-';
							}
							break;
						case 0x19:
							if((uint8_t)values[which]>6) values[which]=7;
							for (const char* q=dpfRegenEnumStrings[(uint8_t)values[which]]; *q && i<DASHBOARD_MESSAGE_MAX_LENGTH ; q++) result[i++] = *q;
							break;

						case 0x1E:
							if((uint8_t)values[which]>1) values[which]=2;
							for (const char* q=setbeltEnumStrings[(uint8_t)values[which]]; *q && i<DASHBOARD_MESSAGE_MAX_LENGTH ; q++) result[i++] = *q;
							break;
						case 0x20:
							switch(currentDNAmode){
								case 0x00: //Natural
									result[i++]='N';
									break;
								case 0x08: //Dynamic
									result[i++]='D';
									break;
								case 0x10: //All Weather
									result[i++]='A';
									break;
								case 0x30: //Race
									result[i++]='R';
									break;
								default:
									result[i++]='?';
							}
							break;
						case 0x22: //current Pedal Map
							result[i++]=currentSchizzaforteMap;
							break;
						default:
							break;
	        		}
	        		which++;
	        		p += 4; // salta "enum"
	        	}else { result[i++] = *p; }
	        }else { result[i++] = *p; }
	    }
	    result[i] = '\0';
	}

	uint8_t removePatterns(char *str) {
	    char *p;
	    while ((p = strstr(str, "$")) != NULL) {
	        // Controllo che ci siano almeno 5 caratteri dopo '$'
	        if (strlen(p) >= 5) {
	            // pattern valido se termina con 'f' o 'm'
	            if (p[4] == 'f' || p[4] == 'm') {
	                // Rimuovo i 5 caratteri ($xxx[fm])
	                memmove(p, p + 5, strlen(p + 5) + 1);
	                continue; // riparto da qui
	            }
	        }
	        str = p + 1; // continuo la ricerca
	    }
	    return (uint8_t)strlen(str);

	}


	/**
	 * Calcola la RAM libera approssimativa
	 * Ritorna: bytes di RAM libera tra heap e stack
	 */
	uint32_t getFreeRAM(void) {
	    uint32_t stack_top;
	    uint32_t heap_end = (uint32_t)&_end;

	    // Ottieni il valore corrente dello stack pointer
	    stack_top = (uint32_t)__get_MSP();

	    // La RAM libera è lo spazio tra la fine dell'heap e lo stack corrente
	    if (stack_top > heap_end) {
	        return stack_top - heap_end;
	    }
	    return 0;
	}



	void clearDashboardBaccableMenu(){
		//prepare empty message
		uartTxMsg[0]=BhBusIDparamString; //# to send message to baccable slave connected to BH can bus
		for(uint8_t i=1;i<UART_BUFFER_SIZE;i++){
			uartTxMsg[i]=0x20; //space char
		}
		//send it
		addToUARTSendQueue(uartTxMsg, UART_BUFFER_SIZE);

	}

	// this function scales value received from can bus. It is assumed that pedal position (or motor rpm) will change vumeter volume represented with the leds strip
	float scaleVolume(uint8_t vol){
		//Scale this value to get a percentage between 0 and 100
		//sniffed data on can bus: msg id=0x412 , fourth byte goes from 0x33(51) to 0xE6(230)
		if (vol>50){
			vol=vol-51;
		}
		return (float)(((float)vol*100.0f)/180.0f);
	}

	uint8_t saveOnflash(){ //store params permanently on flash
		//last page to store on flash is 0x0801 F800 (we can store 2 bytes each time)
		// and we shall erase entire page before write. one page size is FLASH_PAGE_SIZE (2048 bytes in st32F072)
		HAL_FLASH_Unlock(); //unlock flash

		//erase flash
		FLASH_EraseInitTypeDef eraseInitStruct;
		uint32_t pageError=0;
		eraseInitStruct.TypeErase= FLASH_TYPEERASE_PAGES;
		eraseInitStruct.PageAddress=LAST_PAGE_ADDRESS; //last page address begin
		eraseInitStruct.NbPages=1;
		if(HAL_FLASHEx_Erase(&eraseInitStruct,&pageError)!=HAL_OK){ //error during erase
			HAL_FLASH_Lock();
			onboardLed_red_blink(8);
			return 254; //error
		}

		//it seems that stm32F072 supports only writing 2byte words
		//write parameter
		uint8_t paramsNumber=32; //elm327 function 26/08/2026 - was 31
		uint16_t params[40] = {
		  immobilizerEnabled,
		  function_smart_disable_start_stop_enabled,
		  function_led_strip_controller_enabled,
		  function_shift_indicator_enabled,
		  shift_threshold,
		  function_ipc_my23_is_installed,
		  function_route_msg_enabled,
		  function_dyno_mode_master_enabled,
		  function_acc_virtual_pad_enabled,
		  function_front_brake_forcer_master,
		  function_4wd_disabler_enabled,
		  function_remote_start_Enabled,
		  function_clear_faults_enabled,
		  function_esc_tc_customizator_enabled,
		  function_read_faults_enabled,
		  function_is_diesel_enabled,
		  function_regeneration_alert_enabled,
		  launch_torque_threshold,
		  function_seatbelt_alarm_enabled,
		  function_pedal_booster_enabled,
		  function_disable_odometer_blink,
		  function_show_race_mask,
		  function_park_mirror,
		  function_acc_autostart,
		  function_close_windows_with_door_lock,
		  function_open_windows_with_door_lock,
		  HAS_function_enabled,
		  QV_exhaust_flap_function_enabled,
		  (uint8_t)pedal_map_power,
		  parkSensorsMuteFunctionEnabled,  //slot 30: FRONT_PARK_MUTE
		  snifferFunctionEnabled,  //slot 31: SNIFFER //sniffer function 24/08/2026
		  elm327FunctionEnabled,  //slot 32: ELM327 //elm327 function 26/08/2026
		};

		for (uint8_t i = 0; i < paramsNumber; i++) {
		    if (HAL_FLASH_Program(FLASH_TYPEPROGRAM_HALFWORD, LAST_PAGE_ADDRESS + (i * 4), params[i]) != HAL_OK) {
		        HAL_FLASH_Lock();
		        onboardLed_red_blink(9);
		        return 255;
		    }
		}

		//lock the flash
		HAL_FLASH_Lock();
		return 0;
	}

	uint8_t resetStatisticsOnFlash(){

	HAL_FLASH_Unlock(); //unlock flash

			//erase flash
			FLASH_EraseInitTypeDef eraseInitStruct;
			uint32_t pageError=0;
			eraseInitStruct.TypeErase= FLASH_TYPEERASE_PAGES;
			eraseInitStruct.PageAddress=LAST_PAGE_ADDRESS_STATISTICS;
			eraseInitStruct.NbPages=1;
			if(HAL_FLASHEx_Erase(&eraseInitStruct,&pageError)!=HAL_OK){ //error during erase
				HAL_FLASH_Lock();
				onboardLed_red_blink(8);
				return 254; //error
			}
			HAL_FLASH_Lock();
			return 0;
	}

	uint8_t saveStatisticsOnFlash(){
		//compare current stats with best stored times
		uint8_t weShallWriteFlash=0;
		uint16_t params[10];
		if(chronometerElapsedTime_0_100_km_h<readStatisticsFromFlash(1)){
			params[0]=(uint16_t)(chronometerElapsedTime_0_100_km_h *1000);
			weShallWriteFlash=1;
		}else{
			params[0]=(uint16_t)(readStatisticsFromFlash(1) * 1000);
		}

		if(chronometerElapsedTime_100_200_km_h<readStatisticsFromFlash(2)){
			params[1]=(uint16_t)(chronometerElapsedTime_100_200_km_h *1000);
			weShallWriteFlash=1;
		}else{
			params[1]=(uint16_t)(readStatisticsFromFlash(2) * 1000);
		}


		if(weShallWriteFlash){ //if new best time was found, save again all stats
			HAL_FLASH_Unlock(); //unlock flash

			//erase flash
			FLASH_EraseInitTypeDef eraseInitStruct;
			uint32_t pageError=0;
			eraseInitStruct.TypeErase= FLASH_TYPEERASE_PAGES;
			eraseInitStruct.PageAddress=LAST_PAGE_ADDRESS_STATISTICS;
			eraseInitStruct.NbPages=1;
			if(HAL_FLASHEx_Erase(&eraseInitStruct,&pageError)!=HAL_OK){ //error during erase
				HAL_FLASH_Lock();
				onboardLed_red_blink(8);
				return 254; //error
			}

			//it seems that stm32F072 supports only writing 2byte words
			//write parameter

			for (uint8_t i = 0; i < 9; i++) {
				if (HAL_FLASH_Program(FLASH_TYPEPROGRAM_HALFWORD, LAST_PAGE_ADDRESS_STATISTICS + (i * 4), params[i]) != HAL_OK) {
					HAL_FLASH_Lock();
					onboardLed_red_blink(9);
					return 255;
				}
			}

			//lock the flash
			HAL_FLASH_Lock();
			return 0;

		}
		return 253;
	}


	uint8_t saveShownParamsOnflash(){
		//compare current stats with best stored times
		uint8_t weShallWriteFlash=0;
		uint16_t params[30];
		weShallWriteFlash=1;
		if(weShallWriteFlash){ //save shown params
			HAL_FLASH_Unlock(); //unlock flash

			//erase flash
			FLASH_EraseInitTypeDef eraseInitStruct;
			uint32_t pageError=0;
			eraseInitStruct.TypeErase= FLASH_TYPEERASE_PAGES;
			eraseInitStruct.PageAddress=LAST_PAGE_ADDRESS_SHOWN_PARAMS;
			eraseInitStruct.NbPages=1;
			if(HAL_FLASHEx_Erase(&eraseInitStruct,&pageError)!=HAL_OK){ //error during erase
				HAL_FLASH_Lock();
				onboardLed_red_blink(8);
				return 254; //error
			}

			//let's prepare variables
			compress_to_uint16(shownParamsArray, total_pages_in_params_setup_dashboard_menu, params);

			//it seems that stm32F072 supports only writing 2byte words
			//write parameter

			for (uint8_t i = 0; i < 30; i++) {
				if (HAL_FLASH_Program(FLASH_TYPEPROGRAM_HALFWORD, LAST_PAGE_ADDRESS_SHOWN_PARAMS + (i * 4), params[i]) != HAL_OK) {
					HAL_FLASH_Lock();
					onboardLed_red_blink(9);
					return 255;
				}
			}

			//lock the flash
			HAL_FLASH_Lock();
			return 0;

		}
		return 253;
	}

	void compress_to_uint16(const uint8_t *input, size_t input_len, uint16_t *output) {
	    size_t out_index = 0;
	    uint16_t acc = 0;
	    uint8_t bit_count = 0;

	    for (size_t i = 0; i < input_len; ++i) {
	        acc = (acc << 1) | (input[i] & 1); // inserisce il bit in MSB-first
	        bit_count++;

	        if (bit_count == 16) {
	            output[out_index++] = acc;
	            acc = 0;
	            bit_count = 0;
	        }
	    }

	    // Scrive l'ultimo uint16_t se ci sono bit residui
	    if (bit_count > 0) {
	        acc <<= (16 - bit_count); // allinea i bit a sinistra
	        output[out_index] = acc;
	    }
	}


	void decompress_from_uint16(const uint16_t *input, size_t input_len, uint8_t *output, size_t output_len) {
	    size_t out_index = 0;

	    for (size_t i = 0; i < input_len && out_index < output_len; ++i) {
	        uint16_t value = input[i];
	        for (int b = 15; b >= 0 && out_index < output_len; --b) {
	            output[out_index++] = (value >> b) & 1;
	        }
	    }
	}

	void readShownParamsFromFlash(){
		//read from flash
		uint16_t params[30];
		for (uint8_t b = 0; b<30; b++) {
			params[b]=*(volatile uint16_t*)(LAST_PAGE_ADDRESS_SHOWN_PARAMS+(b*4));
		}

		//decompress
		decompress_from_uint16(params, 30, shownParamsArray, 240);

		}

	float readStatisticsFromFlash(uint8_t paramId){ // 1=0-100km/h, 2=100/200km/h
		if(paramId<1) return 0;
		uint16_t tmpParam=*(volatile uint16_t*)(LAST_PAGE_ADDRESS_STATISTICS+((paramId-1)*4));

		return (float)(((float)tmpParam)/1000.0);

	}

	uint16_t readFromFlash(uint8_t paramId){
		if(paramId<1) return 0;
		uint16_t tmpParam=*(volatile uint16_t*)(LAST_PAGE_ADDRESS+((paramId-1)*4));
		switch(paramId){
			case 1: //IMMOBILIZER_ENABLED (1=enabled 0=disabled)
				if(tmpParam>1){
					#if defined(IMMOBILIZER_ENABLED)
						return 1;
					#else
						return 0;
					#endif
				}
				break;
			case 2: //SMART_DISABLE_START_STOP enable status (1=enabled 0=disabled)
				if(tmpParam>1){
					#if defined(SMART_DISABLE_START_STOP)
						return 1;
					#else
						return 0;
					#endif
				}
				break;
			case 3: //LED_STRIP_CONTROLLER_ENABLED  (1=enabled 0=disabled)
				if(tmpParam>1){
					#if defined(LED_STRIP_CONTROLLER_ENABLED)
						return 1;
					#else
						return 0;
					#endif
				}
				break;
			case 4: //SHIFT_INDICATOR_ENABLED  (1=enabled 0=disabled)
				if(tmpParam>1){
					#if defined(SHIFT_INDICATOR_ENABLED)
						return 1;
					#else
						return 0;
					#endif
				}
				break;
			case 5: //SHIFT_THRESHOLD
				if(tmpParam==0xFFFF){
					#if defined(SHIFT_THRESHOLD)
						return SHIFT_THRESHOLD;
					#else
						return 3500; // another default value
					#endif
				}
				break;
			case 6: //IPC_MY23_IS_INSTALLED  (1=enabled 0=disabled)
				if(tmpParam>1){
					#if defined(IPC_MY23_IS_INSTALLED)
						return 1;
					#else
						return 0;
					#endif
				}
				break;
			case 7: //ROUTE_MSG  (1=enabled 0=disabled)
				if(tmpParam>1){
					#if defined(ROUTE_MSG)
						return 1;
					#else
						return 0;
					#endif
				}
				break;
			case 8: //DYNO_MODE_MASTER  (1=enabled 0=disabled)
				if(tmpParam>1){
					#if defined(DYNO_MODE_MASTER)
						return 1;
					#else
						return 0;
					#endif
				}
				break;
			case 9: //ACC_VIRTUAL_PAD  (1=enabled 0=disabled)
				if(tmpParam>1){
					#if defined(ACC_VIRTUAL_PAD)
						return 1;
					#else
						return 0;
					#endif
				}
				break;
			case 10: //FRONT_BRAKE_FORCER_MASTER  (1=enabled 0=disabled)
				if(tmpParam>1){
					#if defined(FRONT_BRAKE_FORCER_MASTER)
						return 1;
					#else
						return 0;
					#endif
				}
				break;
			case 11: //_4WD_DISABLER  (1=enabled 0=disabled)
				if(tmpParam>1){
					#if defined(_4WD_DISABLER)
						return 1;
					#else
						return 0;
					#endif
				}
				break;
			case 12: //REMOTE_START_ENABLED  (1=enabled 0=disabled)
				if(tmpParam>1){
					#if defined(REMOTE_START_ENABLED)
						return 1;
					#else
						return 0;
					#endif
				}
				break;
			case 13: //CLEAR_FAULTS_ENABLED  (1=enabled 0=disabled)
				if(tmpParam>1){
					#if defined(CLEAR_FAULTS_ENABLED)
						return 1;
					#else
						return 0;
					#endif
				}
				break;
			case 14: //ESC_TC_CUSTOMIZATOR_MASTER  (1=enabled 0=disabled)
				if(tmpParam>1){
					#if defined(ESC_TC_CUSTOMIZATOR_MASTER)
						return 1;
					#else
						return 0;
					#endif
				}
				break;
			case 15: //READ_FAULTS_ENABLED  (1=enabled 0=disabled)
				if(tmpParam>1){
					#if defined(READ_FAULTS_ENABLED)
						return 1;
					#else
						return 0;
					#endif
				}
				break;
			case 16: //IS_DIESEL  (1=enabled 0=disabled)
					if(tmpParam>1){
						#if defined(IS_DIESEL)
							return 1;
						#else
							return 0;
						#endif
					}
					break;
			case 17: //REGENERATION_ALERT_ENABLED  (1=enabled 0=disabled)
					if(tmpParam>1){
						#if defined(REGENERATION_ALERT_ENABLED)
							return 1;
						#else
							return 0;
						#endif
					}
					break;
			case 18: //LAUNCH_THRESHOLD
				if(tmpParam==0xFFFF){
					#if defined(LAUNCH_THRESHOLD)
						return LAUNCH_THRESHOLD;
					#else
						return 100; // another default value
					#endif
				}
				break;
			case 19: //SEATBELT_ALARM_DISABLED
				if(tmpParam>1){
					#if defined(SEATBELT_ALARM_DISABLED)
						return 0;
					#else
						return 1;
					#endif
				}
				break;
			case 20: //PEDAL_BOOSTER_ENABLED
				if(tmpParam>8){
					#if defined(PEDAL_BOOSTER_ENABLED)
						return PEDAL_BOOSTER_ENABLED;
					#else
						return 0;
					#endif
				}
				break;
			case 21: //DISABLE_ODOMETER_BLINK
				if(tmpParam>1){
					#if defined(DISABLE_ODOMETER_BLINK)
						return 1;
					#else
						return 0;
					#endif
				}
				break;
			case 22: //SHOW_RACE_MASK
				if(tmpParam>1){
					#if defined(SHOW_RACE_MASK)
						return 1;
					#else
						return 0;
					#endif
				}
				break;
			case 23: //PARK_MIRROR
				if(tmpParam>1){
					#if defined(PARK_MIRROR)
						return 1;
					#else
						return 0;
					#endif
				}
				break;
			case 24: //ACC_AUTOSTART
				if(tmpParam>2){
					#if defined(ACC_AUTOSTART)
						return ACC_AUTOSTART;
					#else
						return 0;
					#endif
				}
				break;
			case 25: //CLOSE_WINDOWS
				if(tmpParam>2){
					#if defined(CLOSE_WINDOWS)
						return CLOSE_WINDOWS;
					#else
						return 0;
					#endif
				}
				break;
			case 26: //OPEN_WINDOWS
				if(tmpParam>2){
					#if defined(OPEN_WINDOWS)
						return OPEN_WINDOWS;
					#else
						return 0;
					#endif
				}
				break;
			case 27: //HAS_VIRTUAL_PAD
				if(tmpParam>1){
					#if defined(HAS_VIRTUAL_PAD)
						return 1;
					#else
						return 0;
					#endif
				}
				break;
			case 28: //QV_EXHAUST_FLAP_FUNCTION_ENABLED
				if(tmpParam>1){
					#if defined(QV_EXHAUST_FLAP_FUNCTION_ENABLED)
						return 1;
					#else
						return 0;
					#endif
				}
				break;
			case 29: //pedal map amplification factor
				if(tmpParam==0xFFFF){
					#if defined(PEDAL_MAP_POWER)
						return PEDAL_MAP_POWER;
					#else
						return 0; // another default value
					#endif
				}
				break;
			case 30: //FRONT_PARK_MUTE (1=enabled 0=disabled)
				if(tmpParam>1){
					#if defined(FRONT_PARK_MUTE) //user_config 28/08/2026
						return 1;
					#else
					return 0; // flash non inizializzata: default disabilitato
					#endif
				}
				break;
			case 31: //SNIFFER (1=enabled 0=disabled) //sniffer function 24/08/2026
				if(tmpParam>1){
					#if defined(SNIFFER) //user_config 28/08/2026
						return 1;
					#else
					return 0; // flash non inizializzata: default disabilitato
					#endif
				}
				break;
			case 32: //ELM327 (1=enabled 0=disabled) //elm327 function 26/08/2026
				if(tmpParam>1){
					#if defined(ELM327) //user_config 28/08/2026
						return 1;
					#else
					return 0; // flash non inizializzata: default disabilitato
					#endif
				}
				break;
			default:
				return 0;
				break;
		}
		return tmpParam;
	}

	uint8_t getParamIndexFromReqId(uint32_t searchedReqId){

		for (uint8_t i=0;i<total_pages_in_params_setup_dashboard_menu;i++){
			if(single_uds_params_array[uds_params_array[function_is_diesel_enabled][i].udsParamId[0]].reqId==searchedReqId) return i;
		}
		//if not found, search it in second param
		for (uint8_t i=0;i<total_pages_in_params_setup_dashboard_menu;i++){
			if(single_uds_params_array[uds_params_array[function_is_diesel_enabled][i].udsParamId[1]].reqId==searchedReqId) return i;
		}
		return 0; //means not found, or param0 (it could be an exception)
	}




	uint8_t getNextVisibleParam(uint8_t curIndex) {

	    uint8_t index = curIndex;
	    while (index < total_pages_in_params_setup_dashboard_menu && !shownParamsArray[index]) index++;

	    if (index >= total_pages_in_params_setup_dashboard_menu) index = 0; //if all hidden, restart from the beginning
	    while (index < curIndex && !shownParamsArray[index]) index++;

	    return index;
	}

	uint8_t getPreviousVisibleParam(uint8_t curIndex) {

	    uint8_t index = curIndex;
	    while (index >= 0 && !shownParamsArray[index]) index--;

	    if (index >= total_pages_in_params_setup_dashboard_menu) index = total_pages_in_params_setup_dashboard_menu-1; //if all hidden, restart from the end
	    while (index > curIndex && !shownParamsArray[index]) index--;

	    return index;
	}

	// Event-driven max hold update for native CAN parameters.
	// Called directly at the extraction point of each native CAN variable,
	// so peaks are captured at CAN bus rate (e.g. every 10ms) rather than at the 500ms display cycle.
	// Only updates dashboardParamMaxHold; display (dashboardParamCouple) is still refreshed at 500ms.
	// Fast-returns if max hold is inactive or the params view is not shown.
	void nativeMaxHoldUpdate(uint8_t paramId){
		if(!maxHold_enabled || dashboard_menu_indent_level!=1 || main_dashboardPageIndex!=1 || !baccableDashboardMenuVisible) return;
		for(uint8_t sel=0; sel<2; sel++){
			if(uds_params_array[function_is_diesel_enabled][dashboardPageIndex].udsParamId[sel]==paramId){
				if(!isnan(dashboardParamCouple[sel])){ //only after the 500ms cycle has set the initial value
					float value=getNativeParam(paramId);
					if(value > dashboardParamMaxHold[sel]){
						dashboardParamMaxHold[sel]=value;
					}
				}
				break;
			}
		}
	}

	//readFaults ECM 10/10/2026 - Read Faults reads the BODY (0x18DA40F1 -> 0x18DAF140) and then, if the list is not full,
	//the ECM (0x18DA10F1 -> 0x18DAF110) in the same way: its faults are appended to the list, shown as ECM (ENGINE on the
	//large display). The UDS sequence is the same for both (see processingExtendedMessage.c).

	//starts the sequence towards one ECU: extended session request (10 03), the reply moves on to ReadDTC.
	//The DTC list (faultsDTCcount, faultsDTCtotal) is not touched: the ECM faults are added after the BODY ones.
	void faultsStartEcuSession(uint8_t ecu){
		faultsEcu              = ecu;
		faultsTxHeader.ExtId   = (ecu==FAULTS_ECU_ECM) ? 0x18DA10F1 : 0x18DA40F1;
		faultsRxReceived       = 0;
		faultsRxExpected       = 0;
		faultsRecordFill       = 0;
		faultsRxNextSN         = 1;
		faultsResponsePending  = 0;
		faultsTimer            = currentTime;
		faultsStateMachine     = 0;
		faultsTxHeader.DLC     = 3;
		faultsTxData[0]        = 0x02; // PCI: SF 2 byte
		faultsTxData[1]        = 0x10; // SID: DiagnosticSessionControl
		faultsTxData[2]        = 0x03; // sub: extendedDiagnosticSession
		can_tx(&faultsTxHeader, faultsTxData);
	}

	//readFaults ABS 10/10/2026 - the ABS is on the C2 bus: C2 reads it and C1 collects the faults over uart (uart.h, FAULTS
	//ABS PROTOCOL). Here only the start request is queued; the periodic message to C2 (processUART) then asks the faults
	//from faultsAbsNextIndex, and faultsAbsProcess decodes the answers. State 0 = waiting for C2, as for BODY and ECM.
	static void faultsStartAbs(void){
		faultsEcu              = FAULTS_ECU_ABS;
		faultsAbsNextIndex     = 0;
		faultsAbsInboxTail     = faultsAbsInboxHead; // answers of a previous reading are dropped
		faultsResponsePending  = 0;
		faultsTimer            = currentTime;
		faultsStateMachine     = 0;
		uint8_t tmpArr[2]={C2BusID,C2cmdAbsFaultsStart};
		addToUARTSendQueue(tmpArr, 2);
	}

	//the ECU being read has finished: failed=0 whole response decoded, failed=1 negative response or timeout.
	//BODY ok and list not full: the ECM is read too. BODY failed: TIMEOUT, as before. ECM ok or failed and list not full:
	//the ABS is read too (by C2). At the end the list is shown, with the faults of the ECUs that answered.
	void faultsEcuEnded(uint8_t failed){
		SNIFFER_DEBUG2(0x2509, ((uint32_t)faultsEcu<<8)|failed, ((uint32_t)faultsDTCtotal<<16)|faultsDTCcount); //read faults: one ECU finished. v1=byte1 ECU (0 BODY, 1 ECM, 2 ABS), byte0 1 if failed (refused/timeout), v2=high 16 bit valid DTC in total, low 16 bit DTC in the list //readFaults ECM 10/10/2026
		faultsResponsePending = 0;
		if(faultsEcu==FAULTS_ECU_BODY){
			if(failed){
				faultsStateMachine = 4; // TIMEOUT display
				faultsTimer        = currentTime;
				return;
			}
			faultsDTCbodyCount=faultsDTCcount;
			faultsDTCecmEnd=faultsDTCcount; //readFaults ABS 10/10/2026
			if(faultsDTCcount<FAULTS_DTC_MAX){
				faultsStartEcuSession(FAULTS_ECU_ECM); // the list has room: read the ECM too (display stays on WAIT)
				return;
			}
		}else if(faultsEcu==FAULTS_ECU_ECM){ //readFaults ABS 10/10/2026
			faultsDTCecmEnd=faultsDTCcount;
			if(faultsDTCcount<FAULTS_DTC_MAX){
				faultsStartAbs(); // the list has still room: the ABS too (display stays on WAIT)
				return;
			}
		}
		faultsDTCsubmenuIndex = 0;
		faultsStateMachine    = 3; // DTC list ready
	}

	//readFaults ABS 10/10/2026 - two hex chars ('0'-'9', 'A'-'F') to a byte, -1 if they are not hex digits
	static int16_t faultsHexByte(const uint8_t *p){
		int16_t v=0;
		for(uint8_t i=0; i<2; i++){
			uint8_t c=p[i];
			v=(int16_t)(v<<4);
			if(c>='0' && c<='9') v=(int16_t)(v+(c-'0'));
			else if(c>='A' && c<='F') v=(int16_t)(v+(c-'A'+10));
			else return -1;
		}
		return v;
	}

	//readFaults ABS 10/10/2026 - decodes the C1cmdAbsFaultsReply messages copied by the uart interrupt (main loop only).
	//'B' C2 is still reading, 'E' the ABS did not answer (or is busy with dyno/front brake): the list keeps BODY and ECM.
	//'R' the faults from index [6]: appended if it is the index asked, otherwise (late or repeated message) ignored.
	void faultsAbsProcess(void){
		while(faultsAbsInboxTail!=faultsAbsInboxHead){
			uint8_t m[UART_BUFFER_SIZE];
			for(uint8_t i=0; i<UART_BUFFER_SIZE; i++) m[i]=faultsAbsInbox[faultsAbsInboxTail][i];
			faultsAbsInboxTail=(uint8_t)((faultsAbsInboxTail+1)%FAULTS_ABS_INBOX_LEN);

			if(faultsEcu!=FAULTS_ECU_ABS || faultsStateMachine!=0) continue; //not collecting the ABS (any more): dropped
			SNIFFER_DEBUG2(0x250A, ((uint32_t)m[2])|((uint32_t)m[5]<<8)|((uint32_t)m[6]<<16), ((uint32_t)faultsAbsNextIndex<<8)|faultsDTCcount); //read faults: ABS answer from C2. v1=byte0 status ('B' reading, 'E' failed, 'R' ready), byte1 kept ('A'+n), byte2 first index ('A'+i), v2=byte1 index asked, byte0 DTC in the list

			if(m[2]=='B'){ faultsTimer=currentTime; continue; } //C2 is reading: the timeout restarts
			if(m[2]=='E'){ faultsEcuEnded(1); continue; }
			if(m[2]!='R') continue;

			int16_t total=faultsHexByte(&m[3]);
			uint8_t kept=(uint8_t)(m[5]-'A');
			uint8_t first=(uint8_t)(m[6]-'A');
			if(total<0 || kept>ABS_FAULTS_DTC_MAX || first!=faultsAbsNextIndex) continue;
			faultsTimer=currentTime;
			if(faultsAbsNextIndex==0) faultsDTCtotal=(uint16_t)(faultsDTCtotal+total); //the ABS total, counted once in "n/m"

			for(uint8_t j=0; j<2; j++){
				uint8_t i=(uint8_t)(first+j);
				if(i>=kept || faultsDTCcount>=FAULTS_DTC_MAX) break;
				int16_t b0=faultsHexByte(&m[7+6*j]);
				int16_t b1=faultsHexByte(&m[9+6*j]);
				int16_t b2=faultsHexByte(&m[11+6*j]);
				if(b0<0 || b1<0 || b2<0) break; //corrupted: asked again from this index
				faultsDTCbytes[faultsDTCcount][0]=(uint8_t)b0;
				faultsDTCbytes[faultsDTCcount][1]=(uint8_t)b1;
				faultsDTCbytes[faultsDTCcount][2]=(uint8_t)b2;
				faultsDTCcount++;
				faultsAbsNextIndex=(uint8_t)(i+1);
			}
			if(faultsAbsNextIndex>=kept || faultsDTCcount>=FAULTS_DTC_MAX) faultsEcuEnded(0); //all the ABS faults, or list full
		}
	}


#endif
