gaucho1978/BACCAble/firmware/ledsStripController/Core/Src/uart.c

#include "uart.h"
#include "stm32f0xx_hal.h"
#include "main.h"
//#include "globalVariables.h"
//extern void Error_Handler(void);

#define QUEUE_SIZE 10  // max queue size

typedef struct {
    uint8_t tx_buffer[QUEUE_SIZE][UART_BUFFER_SIZE];
    uint8_t head;
    uint8_t tail;
    uint8_t count;
} SendQueue;

SendQueue queue_instance= {0};
SendQueue *tx_queue = &queue_instance;



uint32_t last_sent_serial_msg_time=0;

uint32_t lastMsgSentToC2Time=0;
uint32_t lastMsgSentToBHTime=0;

uint8_t rxBuffer[UART_BUFFER_SIZE]; //buffer to receive the message from uart

#if defined(C1baccable)
	uint32_t last_sent_serial_to_schizzaForte_msg_time=0;
	uint8_t rxBufferUart1[UART1_BUFFER_SIZE]; //buffer to receive the message from uart (schizzaForte)
	SendQueue queue_instance_uart1= {0};
	SendQueue *tx_queue_uart1 = &queue_instance_uart1;

#endif

uint8_t rxIndex = 0;
uint8_t syncObtained=0;

//weCanSendAMessageReply identifies last time a message was received by BH and C2 baccable (used by BH and C2 baccable)
//requestToSendOneFrame is Set to 1 to send one frame on dashboard
//uartTxMsg array contains the serial message to send
//clearFaultsRequest, if enabled, sends  messages to clear faults

void uart_init(){

    __HAL_RCC_GPIOA_CLK_ENABLE(); //enable clock for Uart2

    // Configure PA14 as Half-Duplex TX/RX
    GPIO_InitTypeDef GPIO_InitStruct = {0};
    GPIO_InitStruct.Pin = GPIO_PIN_14;
    GPIO_InitStruct.Mode = GPIO_MODE_AF_OD;      // Open-Drain to support both TX and RX on the same pin
    GPIO_InitStruct.Pull = GPIO_PULLUP;          // Necessary to avoid floating states
    GPIO_InitStruct.Speed = GPIO_SPEED_FREQ_HIGH;
    GPIO_InitStruct.Alternate = GPIO_AF1_USART2;
    HAL_GPIO_Init(GPIOA, &GPIO_InitStruct);

	#if defined(C1baccable)
		__HAL_RCC_GPIOB_CLK_ENABLE(); //enable clock for Uart1 (to schizzaforte)

		// Configure PB6 as Half-Duplex TX/RX (to schizzaforte)
		GPIO_InitStruct.Pin = GPIO_PIN_6;
		//GPIO_InitStruct.Mode = GPIO_MODE_AF_PP;
		//GPIO_InitStruct.Pull = GPIO_NOPULL;
		GPIO_InitStruct.Speed = GPIO_SPEED_FREQ_MEDIUM;
		GPIO_InitStruct.Alternate = GPIO_AF0_USART1;
		HAL_GPIO_Init(GPIOB, &GPIO_InitStruct);
	    //HAL_GPIO_WritePin(GPIOB, GPIO_PIN_6, GPIO_PIN_SET);

	#endif

	HAL_Delay(4); //let's wait that electric signal on serial line get stabilized.
	//HAL_Delay(100);onboardLed_red_on();
	__HAL_RCC_USART2_CLK_ENABLE(); //enable clock for usart2

	// Configure USART2 in Half-Duplex mode
    huart2.Instance = USART2;
    huart2.Init.BaudRate = 38400; //38400;
    huart2.Init.WordLength = UART_WORDLENGTH_8B;
    huart2.Init.StopBits = UART_STOPBITS_1;
    huart2.Init.Parity = UART_PARITY_NONE;
    huart2.Init.Mode = UART_MODE_TX_RX;  // Enable both TX and RX
    huart2.Init.HwFlowCtl = UART_HWCONTROL_NONE;
    huart2.Init.OverSampling = UART_OVERSAMPLING_16;
    huart2.AdvancedInit.AdvFeatureInit = UART_ADVFEATURE_NO_INIT;

    if (HAL_HalfDuplex_Init(&huart2) != HAL_OK) Error_Handler(500); //error

    // **Enable the interrupt in the NVIC (if not already set in CubeMX)**
    HAL_NVIC_SetPriority(USART2_IRQn, 0, 0);
    HAL_NVIC_EnableIRQ(USART2_IRQn);

    // **Enable reception in interrupt mode**
    HAL_UART_Receive_IT(&huart2, &rxBuffer[0], 1);  // Start receiving one byte

	#if defined(C1baccable)
    	__HAL_RCC_USART1_CLK_ENABLE(); //enable clock for usart1 (to schizzaforte)

		huart1.Instance = USART1;
		huart1.Init.BaudRate = 9600;
		huart1.Init.WordLength = UART_WORDLENGTH_8B;
		huart1.Init.StopBits = UART_STOPBITS_1;
		huart1.Init.Parity = UART_PARITY_NONE;
		huart1.Init.Mode = UART_MODE_TX_RX;   // richiesto anche in half-duplex
		huart1.Init.HwFlowCtl = UART_HWCONTROL_NONE;
		huart1.Init.OverSampling = UART_OVERSAMPLING_16;
		huart1.AdvancedInit.AdvFeatureInit = UART_ADVFEATURE_NO_INIT;

		//volatile uint32_t tmp = huart1.Instance->CR1; //fake reading, just to let uart1 be prepared
		//(void)tmp;

		//for (voltile int i = 0; i < 10000; i++); //just for test, to allow electric signal to stabilize

		if (HAL_HalfDuplex_Init(&huart1) != HAL_OK) Error_Handler(750);

		// **Enable the interrupt in the NVIC (if not already set in CubeMX)**
		HAL_NVIC_SetPriority(USART1_IRQn, 0, 0);
		HAL_NVIC_EnableIRQ(USART1_IRQn);

		// **Enable reception in interrupt mode**
		HAL_UART_Receive_IT(&huart1, &rxBufferUart1[0], 1);  // Start receiving one byte


	#endif

}

//interrupt called when message is received
void HAL_UART_RxCpltCallback(UART_HandleTypeDef *huart) {
	#if defined(C1baccable)
		if (huart->Instance == USART1) { //message from schizzaForte
			//record current mode
			switch(rxBufferUart1[0]){ // 0x10=Bypass, 0x59=All weather, 0xa2=Natural, 0xeb=Dynamic, 0x34=Race
				case 0x10:
					currentSchizzaforteMap='B';
					break;
				case 0x59:
					currentSchizzaforteMap='A';
					break;
				case 0xa2:
					currentSchizzaforteMap='N';
					break;
				case 0xeb:
					currentSchizzaforteMap='D';
					break;
				case 0x34:
					currentSchizzaforteMap='R';
					break;
				default:
					currentSchizzaforteMap='?';
					break;
			}
			// rxBufferUart1[0]
			onboardLed_blue_on();
			HAL_UART_Receive_IT(&huart1, &rxBufferUart1[0], 1); //receive one char

			#if defined(ACT_AS_SCHIZZAFORTE_SERIAL_CONTROLLER) //if schizzaforte gateway is enabled
				CDC_Transmit_FS(rxBufferUart1, (uint16_t)1);
			#endif
		}

	#endif

    if (huart->Instance == USART2) { //message from other baccable chips
		// evaluate received message
		//elm327 function 28/08/2026 - the diagnostic bridge uses its own destinations (0x0E/0x0F/0x10), which
		//continue the numbering past C1_C2_BusID (0x0D): the upper bound of the valid-start-byte check is raised
		//to ELMLINK_TO_MASTER so the sync state machine assembles the whole 19-byte bridge frame before we touch
		//it. The bridge block is handed to elmlink_on_uart_frame() only once the frame is complete (inside the
		//syncObtained branch below): that is what makes the single-wire framing reliable.
		#if defined(C1baccable) || defined(C2baccable) || defined(BHbaccable)
			#define UART_LAST_MSG_ID ELMLINK_TO_MASTER
		#else
			#define UART_LAST_MSG_ID C1_C2_BusID
		#endif
    	if((rxBuffer[0]>=C1BusID) && (rxBuffer[0]<=UART_LAST_MSG_ID)){ //if the received char indicates the beginning of a message
			if(syncObtained){ //if we were sync, we can process the message, since the first char is correct and the sync indicates that te remaining part too is complete
				#if defined(ACT_AS_CANABLE)
					onboardLed_blue_on();
				#endif

				//elm327 function 28/08/2026 - a complete, synchronised bridge frame is now in rxBuffer. Return 2 means
				//the checksum is wrong, i.e. the framing slipped by a byte on the single-wire line: drop the sync and
				//re-acquire one byte at a time, otherwise the link stays desynced forever and every remote bus dies
				//after the first busy session. Return 1 means the block was ours and is consumed here.
				#if defined(C1baccable) || defined(C2baccable) || defined(BHbaccable)
				{
					uint8_t br = elmlink_on_uart_frame((const uint8_t *)rxBuffer);
					if(br == 2){
						syncObtained = 0;
						HAL_UART_Receive_IT(&huart2, &rxBuffer[0], 1);
						return;
					}
					if(br){
						HAL_UART_Receive_IT(&huart2, &rxBuffer[0], UART_BUFFER_SIZE);
						return;
					}
				}
				#endif

				switch(rxBuffer[0]){
					case C1BusID: //message directed to baccable connected to C1 bus

						#if defined(C1baccable)
							switch(rxBuffer[1]){
								case C1cmdForceFrontBrake:
									front_brake_forced=1; //update status
									launch_assist_enabled=1; //enable launch assist
									break;
								case C1cmdNormalFrontBrake:
									front_brake_forced=0;
									launch_assist_enabled=0; //disable launch assist
									break;
								case C1cmdDynoActive:
									DynoModeEnabledOnMaster=1; //dyno active
									break;
								case C1cmdDynoNotActive:
									DynoModeEnabledOnMaster=0; //dyno not active
									break;
								case C1cmdLaneDoubleTap:
									if(HAS_function_enabled) HAS_buttonPressRequested=5; //press HAS for 5 times (5 messages)
									break;
								case C1cmdLaneSingleTap: //request to C2 to execute the ESC/TC toggle
									//onboardLed_red_on();
									uint8_t tmpArr2[2]={C2BusID,C2cmdtoggleEscTc};
									addToUARTSendQueueDuringInterrupt(tmpArr2, 2);
									break;
								//sniffer function 24/08/2026 - BEGIN
								//tracked per slave: the sniffer enable command is broadcast to C2 and BH together,
								//so the one with no cable attached always times out, and with a single shared
								//command its "disconnected" would clear the state the other slave had just
								//legitimately reported (and C1 would sleep with a session still in use).
								case C1usbConnectedFromC2: //usb connected to C2. avoid sleep
									usbConnectedToC2=1;
									usbConnectedToSlave=1;
									break;
								case C1usbDisconnectedFromC2: //C2 usb no longer configured
									usbConnectedToC2=0;
									usbConnectedToSlave=usbConnectedToBH;
									break;
								case C1usbConnectedFromBH: //usb connected to BH. avoid sleep
									usbConnectedToBH=1;
									usbConnectedToSlave=1;
									break;
								case C1usbDisconnectedFromBH: //BH usb no longer configured
									usbConnectedToBH=0;
									usbConnectedToSlave=usbConnectedToC2;
									break;
								case C1cmdAbsFaultsReply: //ABS faults from C2: only copied here, decoded in the main loop (faultsAbsProcess) //readFaults ABS 10/10/2026
									{
										uint8_t next=(uint8_t)((faultsAbsInboxHead+1)%FAULTS_ABS_INBOX_LEN);
										if(next!=faultsAbsInboxTail){ //full: dropped, C1 asks the same index again
											for(uint8_t i=0; i<UART_BUFFER_SIZE; i++) faultsAbsInbox[faultsAbsInboxHead][i]=rxBuffer[i];
											faultsAbsInboxHead=next;
										}
									}
									break;
								//sniffer function 24/08/2026 - END
								default:
									break;
							}
							onboardLed_blue_on();
						#endif
						break;
					case C2BusID: //message directed to baccable connected to C2 bus
						#if defined(C2baccable)
							switch (rxBuffer[1]){
								case C2cmdtoggleDyno: //dyno request
									if(front_brake_forced==0) dynoToggle();
									break;
								case C2cmdtoggleEscTc: // ESC/TC request
									//if we can, enable it
									if(function_esc_tc_customizator_enabled){
										if(!(DynoModeEnabled || DynoStateMachine!=0xff)) ESCandTCinversion=!ESCandTCinversion;
										uint8_t tmpArr1[2]={C1_Bh_BusID, C1BHcmdShowRaceScreen};
										if(ESCandTCinversion && function_show_race_mask){ //if enabled and race screen requested, notify C1 and BH
											addToUARTSendQueueDuringInterrupt(tmpArr1, 2);
										}else{
											tmpArr1[1]=C1BHcmdStopShowRaceScreen;
											addToUARTSendQueueDuringInterrupt(tmpArr1, 2);
										}
									}
									break;
								case C2cmdForceFrontBrake: //force front brake
									front_brake_forced=5;
									break;
								case C2cmdNormalFrontBrake: //release the brake - we set it to 255, just to trigger serial msg sending in the main (sync) and not here (async), since async may cause concurrent variables write
									front_brake_forced=255;
									break;
								case C2cmdRaceMaskDefault: //do not request to show race mask
									function_show_race_mask=0;
									break;
								case C2cmdShowRaceMask: //request to show race mask
									function_show_race_mask=1;
									break;
								case C2cmdToggleHas: //request to press HAS button for more consecutive messages
									HAS_buttonPressRequested=5;
									break;
								case C2cmdGetStatus:
									//nothing to do, since we just need to set weCanSendAMessageReply
									break;
								case C2cmdFunctParkSensorsMuteDisabled: //park sensors mute disabled
									parkSensorsMuteFunctionEnabled = 0;
									break;
								case C2cmdFunctParkSensorsMuteEnabled: //park sensors mute enabled
									parkSensorsMuteFunctionEnabled = 1;
									break;
								case C2cmdParkMuteBrakeReleased: //brake released, from C1 //park mute brake from C1 10/10/2026
									parkMuteBrakePressed = 0;
									break;
								case C2cmdParkMuteBrakePressed: //brake pressed, from C1 //park mute brake from C1 10/10/2026
									parkMuteBrakePressed = 1;
									break;
								case C2cmdAbsFaultsStart: //C1 asks to read the ABS faults: started in the main loop (absFaultsProcess) //readFaults ABS 10/10/2026
									absFaultsStartRequest = 1;
									break;
								case C2cmdAbsFaultsGet: //C1 asks the ABS faults from index rxBuffer[2]-'A': answered in the main loop //readFaults ABS 10/10/2026
									if(rxBuffer[2]>='A' && rxBuffer[2]<('A'+ABS_FAULTS_DTC_MAX)) absFaultsGetIndex = (uint8_t)(rxBuffer[2]-'A');
									break;
								default:
									break;
							}


							onboardLed_blue_on();
							weCanSendAMessageReply=currentTime;
						#endif

						break;
					case BhBusID: //message directed to baccable connected to BH bus
						#if defined(BHbaccable)
							switch(rxBuffer[1]){
								case BHcmdOdometerBlinkDisable: //odometer blink disable request
									disable_odometer_blink=1;
									break;
								case BHcmdOdometerBlinkDefault: //odometer blink default request
									disable_odometer_blink=0;
									break;
								case BHcmdFunctParkMirrorDisabled: //park mirror disable
									function_park_mirror=0;
									parkMirrorOperativePositionNotStored=1;
									break;
								case BHcmdFunctParkMirrorEnabled: //park mirror enabled
									function_park_mirror=1;
									break;
								case BHcmdFunctParkMirrorStoreCurPos: //park mirror enabled and transfer current mirror position
									function_park_mirror=1;
									storeCurrentParkMirrorPosition=1;
									break;
								default:
							}
							weCanSendAMessageReply=currentTime;
							onboardLed_blue_on();
						#endif
						break;

					case BhBusIDparamString: //message directed to baccable connected to BH bus in order to transfer a parameter to print
						#if defined(BHbaccable)
							memcpy(&dashboardPageStringArray[0], &rxBuffer[1], DASHBOARD_MESSAGE_MAX_LENGTH); //copy array that we will use in the main

							if(ESCandTCinversion){ //if esc/tc is active, don't show baccable menu
								requestToSendOneFrame=0;
							}else{
								if (requestToSendOneFrame<=2) requestToSendOneFrame +=1;//Send one frame
							}
							weCanSendAMessageReply=currentTime;
							onboardLed_blue_on();
						#endif
						break;

					case BhBusIDgetStatus:
						#if defined(BHbaccable)
							weCanSendAMessageReply=currentTime;
							onboardLed_blue_on();
						#endif
						break;

					case BhBusChimeRequest:
						#if defined(BHbaccable)
							weCanSendAMessageReply=currentTime;
							requestToPlayChime=1;
							onboardLed_blue_on();
						#endif
						break;

					case AllSleep: //message directed to all the modules, in order to request low consumption
						//Not used for now..
						break;
					case C2BusIDAllSleepAck: //message directed to baccable on C1 bus, generated by C2 baccable, to inform that he received the sleep request
						//if we are the baccable on C1 bus
						break;
					case BHBusIDAllSleepAck: //message directed to baccable on C1 bus, generated by BH baccable, to inform that he received the sleep request
						//if we are the baccable on C1 bus
						//Not used for now..
						break;
					case AllResetFaults: //message received by baccable on BH and C2 bus. we shall reset all faults
						#if (defined(C2baccable) || defined(BHbaccable))
							clearFaultsRequest=255;

							#if defined(C2baccable)
								weCanSendAMessageReply=currentTime; //we decided that only C2 is allowed to reply
							#endif

							onboardLed_blue_on();
						#endif
						break;

					case C1_C2_BusID: //message received by C1 and C2 baccable.
						#if (defined(C1baccable) || defined(C2baccable))
							if(rxBuffer[1]==C1_C2_cmdLaneDoubleTap){
								if(HAS_function_enabled) HAS_buttonPressRequested=5; //press HAS for 5 times (5 messages)
							}
							onboardLed_blue_on();
						#endif
						break;

					case C1_Bh_BusID: //message received by C1 and BH baccable.
						#if (defined(C1baccable) || defined(BHbaccable))
						//#if defined(C1baccable)
							if(rxBuffer[1]==C1BHcmdShowRaceScreen){
								if(function_esc_tc_customizator_enabled) ESCandTCinversion=1;
							}
							if(rxBuffer[1]==C1BHcmdStopShowRaceScreen){
								ESCandTCinversion=0;
							}
							onboardLed_blue_on();
						#endif
						break;

					case C2_Bh_BusID: //message directed to baccable connected to C2 and BH bus
						#if defined(C2baccable) || defined(BHbaccable)
							switch(rxBuffer[1]){
								case C2_Bh_cmdSetPedalBoostStatus:
									//third byte contains the pedal booster status
									function_pedal_booster_enabled=rxBuffer[2];
									break;
								case C2_Bh_cmdFunctHAS_Disabled:
									HAS_function_enabled=0;
									break;
								case C2_Bh_cmdFunctHAS_Enabled:
									HAS_function_enabled=1;
									break;
								case C2_Bh_cmdFunction_ESC_TC_Disabled:
									function_esc_tc_customizator_enabled=0;
									ESCandTCinversion=0;
									break;
								case C2_Bh_cmdFunction_ESC_TC_Enabled:
									function_esc_tc_customizator_enabled=1;
									break;
								case C2_Bh_cmdFunction_Save_Log_to_File:
									saveToFilesystem();
									break;
								case C2_Bh_cmdSnifferDisabled: //sniffer function 24/08/2026
									snifferStop();
									break;
								case C2_Bh_cmdSnifferEnabled: //sniffer function 24/08/2026 - only ram is touched here, the usb bring up is served by the main loop
									snifferStart();
									break;
								default:
							}

							onboardLed_blue_on();
							#if defined(C2baccable)
								weCanSendAMessageReply=currentTime; //we decided that only C2 can reply, otherwise errors may arise
							#endif
						#endif
						break;

					default:
						//not expected to end up here
						break;
				}

				HAL_UART_Receive_IT(&huart2, &rxBuffer[0], UART_BUFFER_SIZE); //receive next frame  //commented for test
			}else{ //otherwise we were not sync, therefore we need to receive the remaining part of the message
				syncObtained=1;
				HAL_UART_Receive_IT(&huart2, &rxBuffer[1], UART_BUFFER_SIZE-1); //receive remaining part of the frame  //commented for test
			}
    	}else { //we did not receive the begin of the message. discard it
			syncObtained=0; //we lost sync
			//onboardLed_blue_on();
			HAL_UART_Receive_IT(&huart2, &rxBuffer[0], 1); //receive one char  //commented for test
		}
    }
}

// interrupt called when message send is complete
void HAL_UART_TxCpltCallback(UART_HandleTypeDef *huart){

	if (huart->Instance == USART2){
        //message sent. what do we do?
    	onboardLed_blue_on(); //successfully sent
    }

	#if defined(C1baccable)
		if(huart->Instance == USART1){
			//onboardLed_blue_on(); //successfully sent
			CLEAR_BIT(huart1.Instance->CR1, USART_CR1_TE);		//disable TX
			SET_BIT(huart1.Instance->CR1, USART_CR1_RE);		//enable RX
			HAL_UART_Receive_IT(&huart1, &rxBufferUart1[0], 1); //restart RX
		}
	#endif
}

//pause uart
void pauseUart(UART_HandleTypeDef *huart){
	__HAL_UART_DISABLE_IT(huart, UART_IT_RXNE); //disable RX interrupt (RXNE)
    __HAL_UART_DISABLE_IT(huart, UART_IT_ERR); //disable error interrupts (ORE overrun, FE framing, NE noise)

    // deletes all UARTS errors
    __HAL_UART_CLEAR_FLAG(huart,UART_CLEAR_FEF | UART_CLEAR_NEF | UART_CLEAR_OREF | UART_CLEAR_PEF);

	__HAL_UART_FLUSH_DRREGISTER(huart); // Clear RXNE by flushing the data register

	//__HAL_UART_DISABLE(huart);
}

//wake up serial line after pause
void restartUart(UART_HandleTypeDef *huart){
	syncObtained = 0; // sync lost
	// Clear RXNE by flushing the data register
	__HAL_UART_CLEAR_FLAG(huart,UART_CLEAR_FEF | UART_CLEAR_NEF | UART_CLEAR_OREF | UART_CLEAR_PEF);
	__HAL_UART_FLUSH_DRREGISTER(huart);

	//__HAL_UART_ENABLE(huart);

	// Reset HAL internal state
	huart->ErrorCode	= HAL_UART_ERROR_NONE;
	huart->State		= HAL_UART_STATE_READY;

	#if defined(C1baccable)
		if (huart->Instance == USART1) {

			HAL_UART_Receive_IT(huart, &rxBufferUart1[0], 1); //restart receiving one byte
			last_sent_serial_to_schizzaForte_msg_time=currentTime; //avoid to send message in the same moment when interrupt was restarted
		}
	#endif

	if (huart->Instance == USART2) {
		HAL_UART_Receive_IT(huart, &rxBuffer[0], 1);  //restart receiving one byte
		last_sent_serial_msg_time=currentTime; //avoid to send message in the same moment when interrupt was restarted
	}
}


//elm327 function 26/08/2026 - BEGIN
#if defined(C1baccable) || defined(C2baccable) || defined(BHbaccable)
	//Sends one bridge block by writing the data register directly, with reception off while transmitting.
	//HAL_UART_Transmit() is deliberately NOT used: it takes the same lock and the same State field as
	//HAL_UART_Receive_IT(), so if the rx interrupt completed a block mid transmission the re-arm would fail
	//with HAL_BUSY and the port would stay deaf for good. It also waits out any transmission already started
	//by the normal queue (HAL_UART_Transmit_IT), otherwise the two messages would interleave.
	//Every wait has a guard counter: this must never be able to block the main loop forever.
	void uart_link_send(const uint8_t *frame, uint8_t len){
		{
			uint32_t guard = 200000;
			while(((huart2.State == HAL_UART_STATE_BUSY_TX) ||
			       (huart2.State == HAL_UART_STATE_BUSY_TX_RX)) && --guard){}
		}
		{
			uint32_t guard = 200000;
			while(!__HAL_UART_GET_FLAG(&huart2, UART_FLAG_TC) && --guard){}
		}

		__HAL_UART_DISABLE_IT(&huart2, UART_IT_RXNE);
		CLEAR_BIT(huart2.Instance->CR1, USART_CR1_RE);		//reception off while we drive the single wire line

		for(uint8_t i = 0; i < len; i++){
			uint32_t guard = 200000;
			while(!__HAL_UART_GET_FLAG(&huart2, UART_FLAG_TXE) && --guard){}
			if(!guard) break;
			huart2.Instance->TDR = frame[i];
		}
		{
			uint32_t guard = 200000;
			while(!__HAL_UART_GET_FLAG(&huart2, UART_FLAG_TC) && --guard){}	//end of the last byte
		}

		//reception back on, resynchronised from the start of the next block
		syncObtained = 0;
		__HAL_UART_CLEAR_FLAG(&huart2, UART_CLEAR_FEF | UART_CLEAR_NEF | UART_CLEAR_OREF | UART_CLEAR_PEF);
		__HAL_UART_FLUSH_DRREGISTER(&huart2);
		SET_BIT(huart2.Instance->CR1, USART_CR1_RE);
		huart2.ErrorCode = HAL_UART_ERROR_NONE;
		huart2.State     = HAL_UART_STATE_READY;	//this HAL has a single state for TX and RX
		HAL_UART_Receive_IT(&huart2, &rxBuffer[0], 1);
	}
#endif
//elm327 function 26/08/2026 - END

void HAL_UART_ErrorCallback(UART_HandleTypeDef *huart){

	if (( currentTime - lastUartErrorCallback)>1000) onboardLed_red_on();
	lastUartErrorCallback = currentTime;

	/*
	if (huart->ErrorCode & HAL_UART_ERROR_ORE) {
		// Overrun error (full buffer, data loss)
		//onboardLed_red_on();
	}
	if (huart->ErrorCode & HAL_UART_ERROR_FE) {
		// Framing error (08/11/25: when we go to sleep a framing error is arised. why?)
		//onboardLed_red_on();
	}
	if (huart->ErrorCode & HAL_UART_ERROR_NE) {
		// Noise detected
		//onboardLed_red_on();
	}
	if (huart->ErrorCode & HAL_UART_ERROR_PE) {
		// Parity error
		//onboardLed_red_on();
	}

	if (huart->ErrorCode == HAL_UART_ERROR_NONE) {
		// Error not classified
		//onboardLed_red_on();
	}

	if (huart->ErrorCode & HAL_UART_ERROR_DMA) {
		//onboardLed_red_on();
	}

	*/
	pauseUart(huart);
	if ((lowConsumeIsActive==0) || (huart->Instance == USART1)) restartUart(huart);

}
/*
void enter_standby_mode(void) {
	onboardLed_blue_on();
    // Abilita SLEEPDEEP nel registro SCR
    SCB->SCR |= SCB_SCR_SLEEPDEEP_Msk;

    // Abilita la modalità Standby
    PWR->CR |= PWR_CR_PDDS;

    // Abilita il wake-up pin (opzionale)
    //PWR->CSR |= PWR_CSR_EWUP;

    // Entra in Standby Mode
    __WFI();
}

void resetOtherProcessorsSleepStatus(){
	baccableC2_IsSleeping=0;
	baccableBH_IsSleeping=0;
}

uint8_t getOtherProcessorsSleepingStatus(){
	return (baccableC2_IsSleeping && baccableBH_IsSleeping);
}
*/


void addToUARTSendQueue(const uint8_t *data, size_t length) {
	__disable_irq();
	addToUARTSendQueueDuringInterrupt(data,length);
	__enable_irq();
}




void addToUARTSendQueueDuringInterrupt(const uint8_t *data, size_t length) {

	if (tx_queue->count < QUEUE_SIZE) {  // Controlla se la coda è piena
		memset(tx_queue->tx_buffer[tx_queue->tail], 0x20, UART_BUFFER_SIZE);
		if (length>UART_BUFFER_SIZE) length= UART_BUFFER_SIZE;
		memcpy(tx_queue->tx_buffer[tx_queue->tail], data, length);
		tx_queue->tail = (tx_queue->tail + 1) % QUEUE_SIZE;
		tx_queue->count++;
	} else {
		// queue full, ignore the request
		onboardLed_red_on();

	}
}


#if(defined(C1baccable))

	void addToUART1SendQueue(const uint8_t *data, size_t length) { //add to queue message to schizzaforte
		__disable_irq();
		addToUART1SendQueueDuringInterrupt(data,length);
		__enable_irq();
	}

	void addToUART1SendQueueDuringInterrupt(const uint8_t *data, size_t length) {

		if (tx_queue_uart1->count < QUEUE_SIZE) {  // Controlla se la coda è piena
			memset(tx_queue_uart1->tx_buffer[tx_queue_uart1->tail], 0x20, UART1_BUFFER_SIZE);
			if (length>UART1_BUFFER_SIZE) length= UART1_BUFFER_SIZE;
			memcpy(tx_queue_uart1->tx_buffer[tx_queue_uart1->tail], data, length);
			tx_queue_uart1->tail = (tx_queue_uart1->tail + 1) % QUEUE_SIZE;
			tx_queue_uart1->count++;
		} else {
			// queue full, ignore the request
			onboardLed_red_on();

		}
	}

	void processUART1(void) { //process uart toward schizzaForte
		if(currentTime<TIMING__ALL___SERIAL_IGNORE_WINDOW_MS) return;  //give time to schizzaforte to start
		//process messages to schizzaForte

		if (tx_queue_uart1->count == 0) return; // queue empty

		if(currentTime-last_sent_serial_to_schizzaForte_msg_time>TIMING__C1____SCHIZZAFORTE_SERIAL_TIMEOUT_REPLY_MS){ //each 250msec send a message (so that we left the time to receiver to reply)
    		last_sent_serial_to_schizzaForte_msg_time=currentTime;

    		CLEAR_BIT(huart1.Instance->CR1, USART_CR1_RE);	// disable RX
    		SET_BIT(huart1.Instance->CR1, USART_CR1_TE);	// enable TX
    		__HAL_UART_CLEAR_FLAG(&huart1, UART_CLEAR_OREF | UART_CLEAR_NEF | UART_CLEAR_TCF); //clear any error
    		//onboardLed_red_on();
			if (HAL_UART_Transmit_IT(&huart1, tx_queue_uart1->tx_buffer[tx_queue_uart1->head], UART1_BUFFER_SIZE) == HAL_OK){
				// update head index in a circular way
				tx_queue_uart1->head = (tx_queue_uart1->head + 1) % QUEUE_SIZE;
				tx_queue_uart1->count--;

			}else{
				onboardLed_red_on();
			}
		}

	}

#endif

void processUART(void) {

	if(currentTime<TIMING__ALL___SERIAL_IGNORE_WINDOW_MS) return;  //too early

	#if(defined(C1baccable))
		if(lowConsumeIsActive)  return; //other chips are under reset, avoid to send messages   //|| (allProcessorsWakeupTime<TIMING__C1____DELAY_BEFORE_SERIAL_PROCESS_AFTER_OTHER_CHIP_WAKE_MS))
		//onboardLed_blue_on();

		if(currentTime-allProcessorsWakeupTime>TIMING__C1____DELAY_BEFORE_OTHER_CHIP_STATUS_REQUEST_MS){
			if(currentTime-lastMsgSentToC2Time>TIMING__C1____C2_STATUS_REQUEST_TIMEOUT_MS){ //1010
				lastMsgSentToC2Time=currentTime;
				//get status from C2
				//send request thu serial line
				uint8_t tmpArr1[3]={C2BusID,C2cmdGetStatus,' '};
				//readFaults ABS 10/10/2026 - while C1 is collecting the ABS faults, the periodic message to C2 asks them
				//(it opens the reply window of C2 as C2cmdGetStatus does): no extra message in the queue
				if(faultsEcu==FAULTS_ECU_ABS && faultsStateMachine==0){
					tmpArr1[1]=C2cmdAbsFaultsGet;
					tmpArr1[2]=(uint8_t)('A'+faultsAbsNextIndex);
				}
				addToUARTSendQueue(tmpArr1, 3); //commented for test
				onboardLed_blue_on();
			}
			if(currentTime-lastMsgSentToBHTime>TIMING__C1____BH_STATUS_REQUEST_TIMEOUT_MS){ //1260
				lastMsgSentToBHTime=currentTime;
				//get status from BH
				//send request thu serial line
				uint8_t tmpArr2[1]={BhBusIDgetStatus};
				addToUARTSendQueue(tmpArr2, 1);
				onboardLed_blue_on();
			}
		}
	#endif

	if (tx_queue->count == 0) return; // queue empty

    //if we are C2 or BH baccable, we can reply only if we received a message directed to us few milliseconds ago
	#if (defined(C2baccable) || defined(BHbaccable))

		if(currentTime-weCanSendAMessageReply<TIMING__C2_BH_SERIAL_TIMEOUT_REPLY_MS){ //if less than 200msec has passed since last message received from master baccable, send a message

			if( __HAL_UART_GET_FLAG(&huart2, UART_FLAG_TC) ){ //&& (huart2.State == HAL_UART_STATE_READY)
				if(tx_queue->tx_buffer[tx_queue->head][1]==C1cmdLaneSingleTap) onboardLed_red_on(); //just for test
				if (HAL_UART_Transmit_IT(&huart2, tx_queue->tx_buffer[tx_queue->head], UART_BUFFER_SIZE) == HAL_OK){

					// update head index in a circular way
					tx_queue->head = (tx_queue->head + 1) % QUEUE_SIZE;
					tx_queue->count--;
					//onboardLed_blue_on();
				}else{
					onboardLed_red_on();
				}
			}else{
				onboardLed_red_on();
			}
		}
	#endif

    //if we are C1 baccable, we can send a message each 250msec
	#if defined(C1baccable)

    	if(currentTime-last_sent_serial_msg_time>TIMING__C1____SERIAL_TIMEOUT_REPLY_MS){ //each 250msec send a message (so that we left the time to receiver to reply)
			last_sent_serial_msg_time=currentTime;
			if( __HAL_UART_GET_FLAG(&huart2, UART_FLAG_TC) ){ //&& (huart2.State == HAL_UART_STATE_READY)
				if (HAL_UART_Transmit_IT(&huart2, tx_queue->tx_buffer[tx_queue->head], UART_BUFFER_SIZE) == HAL_OK){
					//save time
					switch(tx_queue->tx_buffer[tx_queue->head][0]){
						case C2BusID:
						case C2_Bh_BusID: //only C2 is allowed to reply when this msg is received
						case AllResetFaults: //only C2 is allowed to reply when this msg is received
							lastMsgSentToC2Time=currentTime;
							break;
						case BhBusIDparamString:
						case BhBusIDgetStatus:
						case BhBusChimeRequest:
						case BhBusID:
							lastMsgSentToBHTime=currentTime;
							break;
						default:
					}

					// update head index in a circular way
					tx_queue->head = (tx_queue->head + 1) % QUEUE_SIZE;
					tx_queue->count--;
				}else{
					onboardLed_red_on();


				}
			}
		}



	#endif
}
