gaucho1978/BACCAble/firmware/ledsStripController/Core/Src/processingExtendedMessage.c

/*
 * processingMessage0x00000226.c
 *
 *  Created on: May 3, 2025
 *      Author: GauchoHP
 */

#include "processingExtendedMessage.h"
#include "security_access_mm10ja.h" //pumpForce test25/07/2026 - algoritmo MM10JA per calcolo key ECM

#if defined(C1baccable)
//readFaults fix 05/10/2026 - consumes one byte of the ReadDTCByStatusMask payload ([59][02][availMask] then 4 byte
//records [DTC hi][DTC mid][DTC lo][status]) as it arrives, so a response of any length is decoded without buffering
//it. A record is kept only if its status has testFailed (present now) or confirmedDTC (stored) set: records whose only
//bit is e.g. 0x40 (testNotCompletedSinceLastClear) are not faults. faultsRxReceived counts the payload bytes consumed.
//The first FAULTS_DTC_MAX valid records are kept for the list, faultsDTCtotal counts them all.
static void faultsConsumePayloadByte(uint8_t b){
	uint16_t pos = faultsRxReceived++;
	if (pos < 3) return; // 59 02 availMask: already checked by the caller
	faultsRecord[faultsRecordFill++] = b;
	if (faultsRecordFill < 4) return;
	faultsRecordFill = 0;
	if ((faultsRecord[3] & FAULTS_STATUS_MASK) == 0) return;
	if (faultsDTCtotal < 0xFFFF) faultsDTCtotal++; // counted even beyond FAULTS_DTC_MAX: shown as the total in "n/m"
	if (faultsDTCcount < FAULTS_DTC_MAX) {
		faultsDTCbytes[faultsDTCcount][0] = faultsRecord[0];
		faultsDTCbytes[faultsDTCcount][1] = faultsRecord[1];
		faultsDTCbytes[faultsDTCcount][2] = faultsRecord[2];
		faultsDTCcount++;
	}
}
#endif

#if defined(C2baccable)
//readFaults ABS 10/10/2026 - same decoding as faultsConsumePayloadByte on C1, for the ABS faults read by C2 for C1
static void absFaultsConsumePayloadByte(uint8_t b){
	uint16_t pos = absFaultsRxReceived++;
	if (pos < 3) return; // 59 02 availMask: already checked by the caller
	absFaultsRecord[absFaultsRecordFill++] = b;
	if (absFaultsRecordFill < 4) return;
	absFaultsRecordFill = 0;
	if ((absFaultsRecord[3] & ABS_FAULTS_STATUS_MASK) == 0) return;
	if (absFaultsDTCtotal < 0xFFFF) absFaultsDTCtotal++;
	if (absFaultsDTCcount < ABS_FAULTS_DTC_MAX) {
		absFaultsDTCbytes[absFaultsDTCcount][0] = absFaultsRecord[0];
		absFaultsDTCbytes[absFaultsDTCcount][1] = absFaultsRecord[1];
		absFaultsDTCbytes[absFaultsDTCcount][2] = absFaultsRecord[2];
		absFaultsDTCcount++;
	}
}
#endif

void processingExtendedMessage(){
	#if defined(C1baccable)
		if(immobilizerEnabled && (engineOnSinceMoreThan5seconds<500)){ //if immo enabled and engine is off
			//if it is a message of connection to RFHUB, reset the connection periodically, but start the panic alarm only once
			if(floodTheBus==0){ //if we are not flooding the bus
				uint8_t responseOffset=rx_msg_data[0]>>4; //0=single frame , 1=first fragmented frame 2=fragmented frame, 3=frame ack
				if((rx_msg_header.ExtId & 0xFFFFFFF0)==0x18DAC7F0){ 		//if it is message from the thief
					if(responseOffset<2){ //we pass this if, in case of single frame and first fragmented frame
						switch(rx_msg_data[responseOffset+1]){
							case 0x10: //diagnostic session
							case 0x27: //security access
							case 0x29: //authentication
							case 0x3E: //tester presence
							//case 0x1A: //??
							case 0x2E: //write data by identifier
							case 0x3D: //write memory by address
								floodTheBus=1; //reset the RFHUB and start the alarm
								break;
							default:
								break;
						}
					}
				}else if((rx_msg_header.ExtId & 0xFFFFF0FF)==0x18DAF0C7) { 	//if it is a reply from rfhub
					//if(floodTheBusStartTime==0){ //this allows to read rfhub messages only if it was the first time
						if(responseOffset<2){ //we pass this if, in case of single frame and first fragmented frame
							switch(rx_msg_data[responseOffset+1]){
								case 0x50: //diagnostic session	//
								case 0x67: //security access
								case 0x69: //authentication
								case 0x7E: //tester presence 	//
								//case 0x1A: //??
								case 0x6E: //write data by identifier
								case 0x7D: //write memory by address
									floodTheBus=1; //reset the RFHUB and start the alarm
									break;
								default:
									break;
							}
						}
					//}
				}
				if(floodTheBus==1){ //if we engaged the immobilizer
					floodTheBusStartTime=currentTime; //set initial time we started to flood the bus
					onboardLed_blue_on(); //light a led
				}

			}
		} //end of immobilizer section

		if ((rx_msg_header.ExtId==single_uds_params_array[uds_params_array[function_is_diesel_enabled][dashboardPageIndex].udsParamId[currentParamElementSelection]].replyId) && baccableDashboardMenuVisible){ //if we received UDS message with current selected parameter, let's aquire it
			if(dashboard_menu_indent_level==1 && main_dashboardPageIndex==1){ //if we are in show params menu
				onboardLed_blue_on();
				if (rx_msg_header.DLC>=4+single_uds_params_array[uds_params_array[function_is_diesel_enabled][dashboardPageIndex].udsParamId[currentParamElementSelection]].replyOffset+single_uds_params_array[uds_params_array[function_is_diesel_enabled][dashboardPageIndex].udsParamId[currentParamElementSelection]].replyLen){
					uint8_t numberOfBytesToRead=single_uds_params_array[uds_params_array[function_is_diesel_enabled][dashboardPageIndex].udsParamId[currentParamElementSelection]].replyLen;
					// Limita il numero di byte a un massimo di 4 per evitare overflow
					if (numberOfBytesToRead > 4) {
						numberOfBytesToRead = 4;
					}
					uint32_t tmpVal=0; //take value of received parameter

					// Costruisce il valore a partire dai byte ricevuti
					for (size_t i = 0; i < numberOfBytesToRead; i++) {
						tmpVal |= ((uint32_t)rx_msg_data[4+single_uds_params_array[uds_params_array[function_is_diesel_enabled][dashboardPageIndex].udsParamId[currentParamElementSelection]].replyOffset+i]) << (8 * (numberOfBytesToRead - 1 - i));
					}

					tmpVal+=single_uds_params_array[uds_params_array[function_is_diesel_enabled][dashboardPageIndex].udsParamId[currentParamElementSelection]].replyValOffset;
					float tmpVal2 =tmpVal * single_uds_params_array[uds_params_array[function_is_diesel_enabled][dashboardPageIndex].udsParamId[currentParamElementSelection]].replyScale;
					tmpVal2 +=single_uds_params_array[uds_params_array[function_is_diesel_enabled][dashboardPageIndex].udsParamId[currentParamElementSelection]].replyScaleOffset;

					if(uds_params_array[function_is_diesel_enabled][dashboardPageIndex].udsParamId[currentParamElementSelection]== uds_params_array[function_is_diesel_enabled][dashboardPageIndex].udsParamId[!currentParamElementSelection]){
						currentParamElementSelection=0; //single param
					}

					if(maxHold_enabled){
						if(isnan(dashboardParamCouple[currentParamElementSelection])){
							dashboardParamMaxHold[currentParamElementSelection]=tmpVal2; //first update after navigation: reset max hold
						}else if(tmpVal2 > dashboardParamMaxHold[currentParamElementSelection]){
							dashboardParamMaxHold[currentParamElementSelection]=tmpVal2; //new maximum found
						}
						dashboardParamCouple[currentParamElementSelection]=dashboardParamMaxHold[currentParamElementSelection];
					}else{
						dashboardParamCouple[currentParamElementSelection]=tmpVal2; //normal behavior
					}
					sendDashboardPageToSlaveBaccable();//send parameters to BH
				}
			}
		}
		/*
		if(seatbeltAlarmDisabled==0xfe){ //if seatbelt status acquisition is in progress
			if(rx_msg_header.ExtId==0x18DAF160){ //if received message comes from IPC
				if (rx_msg_header.DLC>=5){ //if at least 5 bytes
					if(rx_msg_data[1]==0x62){ //if param read reply successful
						if((rx_msg_data[2]==0x55) && (rx_msg_data[3]==0xA0 )){ //if param. 55A0 (seat belt alarm status)
							seatbeltAlarmDisabled= !(rx_msg_data[4]); //coherce to boolean and negate
						}
					}
				}
			}
		}
		*/

		if((seatbeltAlarmDisabled==0x11) || (seatbeltAlarmDisabled==0x21)){ //if write param was sent (seatbelt disabling or enabling in progress)
			if(rx_msg_header.ExtId==0x18DAF160){ //if received message comes from IPC
				if (rx_msg_header.DLC>=4){ //if at least 4 bytes
					if(rx_msg_data[1]==0x6F){ //if write param reply successful
						if((rx_msg_data[2]==0x55) && (rx_msg_data[3]==0xA0)){ //if param wrote was 55A0 (en/dis seatbelt alam)
							if(seatbeltAlarmDisabled==0x11){ // if seatbelt disabling
								seatbeltAlarmDisabled=1; //seatbelt disabled
							}
							if(seatbeltAlarmDisabled==0x21){ // if seatbelt enabling
								seatbeltAlarmDisabled=0; //seatbelt enabled
							}
						}
					}
				}
			}
		}


		if((seatbeltAlarmDisabled==0x10) || (seatbeltAlarmDisabled==0x20)){ //if diag session was sent (seatbelt disabling or enabling is in progress)
			if(rx_msg_header.ExtId==0x18DAF160){ //if received message comes from IPC
				if (rx_msg_header.DLC>=2){ //if at least 2 bytes
					if(rx_msg_data[1]==0x50){ //if diag session reply successful
						// Send enable/disable seatbelt alarm message
						uds_parameter_request_msg_header.ExtId=0x18DA60F1;
						uds_parameter_request_msg_header.DLC=6;
						uds_parameter_request_msg_data[0]=0x05;
						uds_parameter_request_msg_data[1]=0x2F;
						uds_parameter_request_msg_data[2]=0x55;
						uds_parameter_request_msg_data[3]=0xA0;
						uds_parameter_request_msg_data[4]=0x03;

						if(seatbeltAlarmDisabled==0x10){ // if seatbelt disabling
							uds_parameter_request_msg_data[5]=0x00; //set byte to disable alarm
						}
						if(seatbeltAlarmDisabled==0x20){ // if seatbelt enabling
							uds_parameter_request_msg_data[5]=0x01; //send msg to enable alarm
						}
						// send message
						can_tx(&uds_parameter_request_msg_header, uds_parameter_request_msg_data); //transmit the diag session request

						seatbeltAlarmDisabled++; //record that operation was executed
						seatbeltAlarmStatusRequestTime=currentTime;
						last_sent_uds_parameter_request_Time=currentTime;
					}
				}
			}
		}



		if(function_route_msg_enabled==1){
			if (rx_msg_header.ExtId==0x18DABAF1){ //if route request and dashboard menu not shown to avoid conflicts
				if (rx_msg_header.DLC>=7){
					routeStdIdMsg=!(rx_msg_data[2]>>4); //standard or extended msgID route request
					routeOffset=(rx_msg_data[2] & 0x0F); //offset from which start to copy
					routeMsgData[2]=rx_msg_data[2]; //copy in the response

					routeMsgId=	((uint32_t)rx_msg_data[3] << 24) |  // MSB
								((uint32_t)rx_msg_data[4] << 16) |
								((uint32_t)rx_msg_data[5] << 8)  |
								((uint32_t)rx_msg_data[6]);       	 // LSB



					onboardLed_blue_on();
				}
			}

			if(baccableDashboardMenuVisible) routeStdIdMsg=0xff; //disables the route request, to avoid conflicts with show params functionality

			if(routeStdIdMsg==0){ //if we have to do it (ext id route request)
				if(rx_msg_header.ExtId==routeMsgId){ //received msg to route
					routeStdIdMsg=0xFF; //set this to disable the request. only one message is routed to avoid bus flood
					if(routeOffset<rx_msg_header.DLC){ //send only if offset is correct
						uint8_t sizeToCopy=5; //
						if((rx_msg_header.DLC - routeOffset )<sizeToCopy) sizeToCopy=rx_msg_header.DLC - routeOffset;
						memcpy(&routeMsgData[3],&rx_msg_data[routeOffset],sizeToCopy);
						if(sizeToCopy<5) memset(&routeMsgData[3+sizeToCopy],0x00, 5-sizeToCopy);

						//send it
						can_tx(&routeMsgHeader, routeMsgData);
						onboardLed_blue_on();
					}

				}
			}
		}

		//pumpForce test25/07/2026 - BEGIN
		// -----------------------------------------------------------------------
		// PUMP FORCE — Gestione risposte ECM (ECU 0x10, ExtId risposta 0x18DAF110)
		//
		// Sequenza UDS attesa:
		//   Stato 0: ricezione 50 03  → invia 27 01 (request seed)        → stato 1
		//   Stato 1: ricezione 67 01  → calcola key MM10JA, invia 27 02   → stato 2
		//   Stato 2: ricezione 67 02  → prepara frame IO Control           → stato 3
		//   Stato 3: invio periodico 2F 50 11 03 FF gestito in C1baccablePeriodicCheck()
		//   Qualsiasi 7F: abort incondizionato (no retry)
		//
		// Formato ISO-TP single-frame (tutti i messaggi di questa sequenza):
		//   byte[0] = PCI  (nibble alto=0 → single frame; nibble basso = n byte dati)
		//   byte[1] = SID risposta (SID richiesta + 0x40)
		//   byte[2] = subfunction o DID high
		//   byte[3..] = payload (seed, key, DID low, controlOption, controlValue)
		// -----------------------------------------------------------------------
		if (rx_msg_header.ExtId == 0x18DAF110 && pumpForceStateMachine != 0xFF) {

			// Risposta negativa (0x7F xx xx): la ECM ha rifiutato l'ultima richiesta
			if (rx_msg_header.DLC >= 3 && rx_msg_data[1] == 0x7F) {
				pumpForceStateMachine = 0xFF; // abort definitivo, nessun retry automatico

			// Stato 0 → 1: conferma sessione estesa ricevuta ([06, 50, 03, 00, 32, 01, F4])
			} else if (pumpForceStateMachine == 0 &&
					   rx_msg_header.DLC >= 3 &&
					   rx_msg_data[1] == 0x50 && rx_msg_data[2] == 0x03) {
				// Sessione aperta: richiedi seed per security access livello 1
				pumpForceTxHeader.DLC = 3;
				pumpForceTxData[0] = 0x02; // PCI: single frame, 2 byte dati
				pumpForceTxData[1] = 0x27; // SID: SecurityAccess
				pumpForceTxData[2] = 0x01; // subfunction: requestSeed livello 1
				can_tx(&pumpForceTxHeader, pumpForceTxData);
				lastPumpForceMsgTime = currentTime; // aggiorna timestamp per calcolo timeout
				pumpForceStateMachine = 1;

			// Stato 1 → 2: seed ricevuto ([06, 67, 01, s0, s1, s2, s3], DLC=7)
			// Il seed è a 4 byte big-endian a partire da byte[3]
			} else if (pumpForceStateMachine == 1 &&
					   rx_msg_header.DLC >= 7 &&
					   rx_msg_data[1] == 0x67 && rx_msg_data[2] == 0x01) {
				ecmSeed[0] = rx_msg_data[3];
				ecmSeed[1] = rx_msg_data[4];
				ecmSeed[2] = rx_msg_data[5];
				ecmSeed[3] = rx_msg_data[6];
				// Calcola la key con algoritmo S1_FGA_ORIGINAL_ECU_Sup0002 (costante interna 0x17591215)
				uint8_t ecmKey[4];
				mm10ja_compute_key(ecmSeed, ecmKey);
				// Invia key: 27 02 + 4 byte key (6 byte dati totali → DLC=7)
				pumpForceTxHeader.DLC = 7;
				pumpForceTxData[0] = 0x06; // PCI: single frame, 6 byte dati
				pumpForceTxData[1] = 0x27; // SID: SecurityAccess
				pumpForceTxData[2] = 0x02; // subfunction: sendKey livello 1
				pumpForceTxData[3] = ecmKey[0];
				pumpForceTxData[4] = ecmKey[1];
				pumpForceTxData[5] = ecmKey[2];
				pumpForceTxData[6] = ecmKey[3];
				can_tx(&pumpForceTxHeader, pumpForceTxData);
				lastPumpForceMsgTime = currentTime;
				pumpForceStateMachine = 2;

			// Stato 2 → 3: accesso sicurezza concesso ([02, 67, 02])
			} else if (pumpForceStateMachine == 2 &&
					   rx_msg_header.DLC >= 3 &&
					   rx_msg_data[1] == 0x67 && rx_msg_data[2] == 0x02) {
				// Prepara il frame IO Control che verrà inviato periodicamente in C1baccablePeriodicCheck()
				// InputOutputControlByIdentifier DID=0x5011, shortTermAdjustment (0x03), val=0xFF (max flow)
				pumpForceTxHeader.DLC = 6;
				pumpForceTxData[0] = 0x05; // PCI: single frame, 5 byte dati
				pumpForceTxData[1] = 0x2F; // SID: InputOutputControlByIdentifier
				pumpForceTxData[2] = 0x50; // DID high byte
				pumpForceTxData[3] = 0x11; // DID low byte
				pumpForceTxData[4] = 0x03; // controlOption: shortTermAdjustment
				pumpForceTxData[5] = 0xFF; // controlValue: massima portata (0xFF)
				lastPumpForceMsgTime = 0;   // azzera il timer → il primo invio avviene al loop successivo
				pumpForceStateMachine = 3;
			}
		}
		//pumpForce test25/07/2026 - END

		//readFaults 12/08/2026 - BEGIN
		// -----------------------------------------------------------------------
		// READ FAULTS — Gestione risposte Body ECU (ECU 0x40, ExtId risposta 0x18DAF140) e poi ECM (ECU 0x10, ExtId risposta
		// 0x18DAF110): stessa sequenza, l'ECM viene letta dopo il BODY se la lista non e' piena (faultsEcuEnded) //readFaults ECM 10/10/2026
		//
		// Sequenza UDS:
		//   Stato 0: ricezione 50 03  → invia 19 02 FF (ReadDTCByStatusMask) → stato 1
		//   Stato 1: single frame (PCI nibble alto=0, SID=59, sub=02) → parsa DTC  → faultsEcuEnded (ECM o stato 3) //readFaults ECM 10/10/2026
		//   Stato 1: first frame  (PCI nibble alto=1, SID=59, sub=02) → invia FC   → stato 2
		//   Stato 2: consecutive frames (PCI nibble alto=2) → accumula buffer      → faultsEcuEnded (ECM o stato 3) //readFaults ECM 10/10/2026
		//   Risposta negativa (SID=7F): BODY → stato 4 (errore/timeout display), ECM → lista con i soli guasti BODY //readFaults ECM 10/10/2026
		//   eccetto 7F xx 78 (responsePending): si resta in attesa, timeout esteso a 5 s // readFaults fix 05/10/2026
		//
		// Formato payload risposta ReadDTCByStatusMask (0x59 0x02):
		//   [59][02][availMask][DTChi][DTCmid][DTClo][DTCstatus] x N record
		//   Ogni record = 4 byte; parsing: offset 3 = primo DTC high byte
		//
		// readFaults fix 05/10/2026 - con statusMask FF la Body ECU rispondeva con 539 byte (134 record): 132 con stato
		// 0x40 (testNotCompletedSinceLastClear, NON sono guasti) e solo 2 guasti veri, in fondo. Il firmware teneva i primi
		// 90 byte e non guardava lo stato: mostrava 20 codici che non erano guasti e perdeva quelli veri. Ora:
		//   - si chiede statusMask 09 (testFailed | confirmedDTC): la ECU manda solo i guasti presenti o memorizzati;
		//   - il byte di stato viene controllato comunque (FAULTS_STATUS_MASK), se una ECU ignorasse la maschera;
		//   - i record si decodificano man mano che arrivano (faultsConsumePayloadByte), senza limite sulla lunghezza
		//     della risposta: si tengono i primi FAULTS_DTC_MAX guasti validi.
		// -----------------------------------------------------------------------
		if (faultsEcu != FAULTS_ECU_ABS && rx_msg_header.ExtId == ((faultsEcu==FAULTS_ECU_ECM) ? 0x18DAF110 : 0x18DAF140) && faultsStateMachine != 0xFF) { //readFaults ECM 10/10/2026 - the ABS is read by C2 //readFaults ABS 10/10/2026

			uint8_t pci      = rx_msg_data[0];
			uint8_t pci_type = (pci >> 4) & 0x0F;
			uint8_t faultsDiscardReason = 0; //readFaults debug 05/10/2026 - !=0: frame ignored, reason traced below (0x2504)

			SNIFFER_DEBUG2(0x2501, ((uint32_t)rx_msg_data[0])|((uint32_t)rx_msg_data[1]<<8)|((uint32_t)rx_msg_data[2]<<16)|((uint32_t)rx_msg_data[3]<<24), ((uint32_t)rx_msg_data[4])|((uint32_t)rx_msg_data[5]<<8)|((uint32_t)rx_msg_data[6]<<16)|((uint32_t)rx_msg_data[7]<<24)); //read faults: frame from the ECU being read (BODY or ECM, see 0x2509). v1=byte 0..3, v2=byte 4..7 //readFaults debug 05/10/2026

			// readFaults fix 05/10/2026 - 7F xx 78 (responsePending) non e' un rifiuto: la ECU chiede tempo e la risposta
			// positiva arriva dopo. Prima veniva trattato come errore e mostrava TIMEOUT. Si resta nello stato corrente,
			// riavviando il timeout ed estendendolo a P2*server (vedi C1baccablePeriodicCheck).
			if (rx_msg_header.DLC >= 4 && rx_msg_data[1] == 0x7F && rx_msg_data[3] == 0x78 && faultsStateMachine < 3) {
				SNIFFER_DEBUG2(0x2503, faultsStateMachine, rx_msg_data[2]); //read faults: responsePending, keep waiting. v1=state, v2=service id //readFaults debug 05/10/2026
				faultsResponsePending = 1;
				faultsTimer           = currentTime;

			// Risposta negativa (0x7F): BODY → display TIMEOUT, ECM → lista con i soli guasti BODY //readFaults ECM 10/10/2026
			} else if (rx_msg_header.DLC >= 2 && rx_msg_data[1] == 0x7F && faultsStateMachine < 3) { // a 7F after the end is ignored (reason 5) //readFaults ECM 10/10/2026
				SNIFFER_DEBUG2(0x2502, faultsStateMachine, ((uint32_t)rx_msg_data[2]<<8)|rx_msg_data[3]); //read faults: request refused. v1=state, v2=byte1 service id, byte0 NRC //readFaults debug 05/10/2026
				faultsEcuEnded(1); // BODY: TIMEOUT display. ECM: list with the BODY faults //readFaults ECM 10/10/2026

			// Stato 0: conferma sessione estesa (50 03) → invia ReadDTC
			} else if (faultsStateMachine == 0) {
				if (rx_msg_header.DLC >= 3 && rx_msg_data[1] == 0x50 && rx_msg_data[2] == 0x03) {
					faultsTxHeader.DLC = 4;
					faultsTxData[0]    = 0x03; // PCI: single frame, 3 byte dati
					faultsTxData[1]    = 0x19; // SID: ReadDTCInformation
					faultsTxData[2]    = 0x02; // subfunction: reportDTCByStatusMask
					faultsTxData[3]    = FAULTS_STATUS_MASK; // statusMask: solo guasti presenti (0x01) o confermati (0x08) //readFaults fix 05/10/2026 - era 0xFF
					can_tx(&faultsTxHeader, faultsTxData);
					faultsResponsePending = 0;
				faultsTimer        = currentTime; // riavvia timeout per la risposta ReadDTC
				faultsStateMachine = 1;
				} else {
					faultsDiscardReason = 1; // non e' la conferma di sessione 50 03
				}

			// Stato 1 + single frame (PCI type 0): parsa DTC direttamente
			} else if (faultsStateMachine == 1 && pci_type == 0) {
				uint8_t payloadLen = pci & 0x0F;
				if (payloadLen >= 3 && rx_msg_header.DLC >= 4 &&
					rx_msg_data[1] == 0x59 && rx_msg_data[2] == 0x02) {
					faultsRxReceived = 0; // faultsDTCcount/faultsDTCtotal are not reset: the ECM faults follow the BODY ones //readFaults ECM 10/10/2026
					faultsRecordFill = 0;
					for (uint8_t i = 0; i < payloadLen && (i + 1) < rx_msg_header.DLC; i++) {
						faultsConsumePayloadByte(rx_msg_data[1 + i]); // [0]=59 [1]=02 [2]=avail [3..]=record DTC
					}
					SNIFFER_DEBUG2(0x2506, ((uint32_t)faultsDTCtotal<<16)|faultsDTCcount, faultsRxReceived); //read faults: DTC parsed from a single frame. v1=low 16 bit DTC kept in the list, high 16 bit valid DTC in total, v2=payload bytes //readFaults debug 05/10/2026
					faultsEcuEnded(0); // BODY: read the ECM too if the list has room. ECM: list ready //readFaults ECM 10/10/2026
				} else {
					faultsDiscardReason = 2; // single frame che non e' una risposta 59 02 valida
				}

			// Stato 1 + first frame (PCI type 1): avvia riassemblaggio multiframe
			} else if (faultsStateMachine == 1 && pci_type == 1) {
				uint16_t totalLen = ((uint16_t)(pci & 0x0F) << 8) | rx_msg_data[1];
				SNIFFER_DEBUG2(0x2505, totalLen, totalLen); //read faults: first frame. v1=declared length, v2=same (whole response decoded, no 90 byte limit since 05/10/2026) //readFaults debug 05/10/2026
				faultsRxExpected  = totalLen;
				faultsRxReceived  = 0;
				faultsRecordFill  = 0; // faultsDTCcount/faultsDTCtotal are not reset: the ECM faults follow the BODY ones //readFaults ECM 10/10/2026
				faultsRxNextSN    = 1;
				// primi 6 byte di payload (data[2..7]): 59 02 availMask e l'inizio del primo record
				uint8_t toCopy = (totalLen < 6) ? (uint8_t)totalLen : 6;
				for (uint8_t i = 0; i < toCopy; i++) {
					faultsConsumePayloadByte(rx_msg_data[2 + i]);
				}
				// Flow Control: ContinueToSend, BlockSize=0, STmin=0ms
				faultsTxHeader.DLC = 3;
				faultsTxData[0]    = 0x30;
				faultsTxData[1]    = 0x00;
				faultsTxData[2]    = 0x00;
				can_tx(&faultsTxHeader, faultsTxData);
				faultsResponsePending = 0;
				faultsStateMachine = 2;

			// Stato 2 + consecutive frame (PCI type 2): accumula e verifica completezza
			} else if (faultsStateMachine == 2 && pci_type == 2) {
				uint8_t sn = pci & 0x0F;
				if (sn == faultsRxNextSN) {
					faultsRxNextSN = (uint8_t)((faultsRxNextSN + 1) & 0x0F);
					for (uint8_t i = 1; i < rx_msg_header.DLC && faultsRxReceived < faultsRxExpected; i++) {
						faultsConsumePayloadByte(rx_msg_data[i]); // i record vengono decodificati man mano
					}
					if (faultsRxReceived >= faultsRxExpected) {
						// Payload completo: i guasti validi sono gia' in faultsDTCbytes
						SNIFFER_DEBUG2(0x2506, ((uint32_t)faultsDTCtotal<<16)|faultsDTCcount, faultsRxReceived); //read faults: DTC parsed from a multiframe. v1=low 16 bit DTC kept in the list (max FAULTS_DTC_MAX), high 16 bit valid DTC in total, v2=payload bytes //readFaults debug 05/10/2026
						faultsEcuEnded(0); // BODY: read the ECM too if the list has room. ECM: list ready //readFaults ECM 10/10/2026
					}
				} else {
					faultsDiscardReason = 4; // numero di sequenza inatteso: il frame viene ignorato e si arrivera' al timeout
				}

			} else {
				faultsDiscardReason = (faultsStateMachine >= 3) ? 5 : 3; // 5 = frame arrivato a sequenza conclusa, 3 = tipo PCI inatteso per lo stato
			}

			if (faultsDiscardReason) {
				SNIFFER_DEBUG2(0x2504, faultsStateMachine, ((uint32_t)pci<<16)|((uint32_t)faultsRxNextSN<<8)|faultsDiscardReason); //read faults: frame ignored. v1=state, v2=byte2 PCI, byte1 expected SN, byte0 reason (1 no 50 03, 2 bad single frame, 3 unexpected PCI type, 4 wrong SN, 5 sequence already ended) //readFaults debug 05/10/2026
			}
		}
		//readFaults 12/08/2026 - END

	#endif //end define

	#if defined(C2baccable)
		//readFaults ABS 10/10/2026 - ABS faults read for C1: same UDS sequence as Read Faults on C1 (10 03, 19 02 09, single
		//frame or first frame + flow control + consecutive frames). Only while the ABS is not used by dyno or front brake
		//(they talk to the same ECU, 0x18DA28F1): absFaultsProcess (functions_C2baccable.c) stops the reading if they start.
		if (rx_msg_header.ExtId==0x18DAF128 && absFaultsState<3 && DynoStateMachine==0xff && DynoModeEnabled==0 && front_brake_forced==0) {
			uint8_t pci      = rx_msg_data[0];
			uint8_t pci_type = (pci >> 4) & 0x0F;
			if (rx_msg_header.DLC >= 4 && rx_msg_data[1] == 0x7F && rx_msg_data[3] == 0x78) { //responsePending: keep waiting, up to 5 s
				absFaultsResponsePending = 1;
				absFaultsTimer           = currentTime;
			} else if (rx_msg_header.DLC >= 2 && rx_msg_data[1] == 0x7F) { //refused
				SNIFFER_DEBUG2(0x2301, absFaultsState, ((uint32_t)rx_msg_data[2]<<8)|rx_msg_data[3]); //ABS faults: request refused by the ABS. v1=state, v2=byte1 service id, byte0 NRC
				absFaultsState = 4;
			} else if (absFaultsState == 0) {
				if (rx_msg_header.DLC >= 3 && rx_msg_data[1] == 0x50 && rx_msg_data[2] == 0x03) {
					absFaultsTxHeader.DLC = 4;
					absFaultsTxData[0]    = 0x03; // PCI: single frame, 3 byte dati
					absFaultsTxData[1]    = 0x19; // SID: ReadDTCInformation
					absFaultsTxData[2]    = 0x02; // subfunction: reportDTCByStatusMask
					absFaultsTxData[3]    = ABS_FAULTS_STATUS_MASK;
					can_tx(&absFaultsTxHeader, absFaultsTxData);
					absFaultsResponsePending = 0;
					absFaultsTimer = currentTime;
					absFaultsState = 1;
				}
			} else if (absFaultsState == 1 && pci_type == 0) { //single frame
				uint8_t payloadLen = pci & 0x0F;
				if (payloadLen >= 3 && rx_msg_header.DLC >= 4 && rx_msg_data[1] == 0x59 && rx_msg_data[2] == 0x02) {
					absFaultsRxReceived = 0;
					absFaultsRecordFill = 0;
					for (uint8_t i = 0; i < payloadLen && (i + 1) < rx_msg_header.DLC; i++) {
						absFaultsConsumePayloadByte(rx_msg_data[1 + i]);
					}
					absFaultsState = 3;
				}
			} else if (absFaultsState == 1 && pci_type == 1) { //first frame
				absFaultsRxExpected = ((uint16_t)(pci & 0x0F) << 8) | rx_msg_data[1];
				absFaultsRxReceived = 0;
				absFaultsRecordFill = 0;
				absFaultsRxNextSN   = 1;
				uint8_t toCopy = (absFaultsRxExpected < 6) ? (uint8_t)absFaultsRxExpected : 6;
				for (uint8_t i = 0; i < toCopy; i++) {
					absFaultsConsumePayloadByte(rx_msg_data[2 + i]);
				}
				absFaultsTxHeader.DLC = 3; // Flow Control: ContinueToSend, BlockSize=0, STmin=0ms
				absFaultsTxData[0]    = 0x30;
				absFaultsTxData[1]    = 0x00;
				absFaultsTxData[2]    = 0x00;
				can_tx(&absFaultsTxHeader, absFaultsTxData);
				absFaultsResponsePending = 0;
				absFaultsTimer = currentTime;
				absFaultsState = 2;
			} else if (absFaultsState == 2 && pci_type == 2) { //consecutive frame
				if ((pci & 0x0F) == absFaultsRxNextSN) {
					absFaultsRxNextSN = (uint8_t)((absFaultsRxNextSN + 1) & 0x0F);
					for (uint8_t i = 1; i < rx_msg_header.DLC && absFaultsRxReceived < absFaultsRxExpected; i++) {
						absFaultsConsumePayloadByte(rx_msg_data[i]);
					}
					absFaultsTimer = currentTime;
					if (absFaultsRxReceived >= absFaultsRxExpected) absFaultsState = 3;
				}
			}
		}

		//dyno debug 04/10/2026 - every ABS diagnostic reply is traced: byte 0..3 in v1, byte 4..7 in v2 (DLC and state are in the rx frame and in 0x2200)
		if (rx_msg_header.ExtId==0x18DAF128){
			if(DynoStateMachine!=0xff){
				SNIFFER_DEBUG2(0x2201, ((uint32_t)rx_msg_data[0])|((uint32_t)rx_msg_data[1]<<8)|((uint32_t)rx_msg_data[2]<<16)|((uint32_t)rx_msg_data[3]<<24), ((uint32_t)rx_msg_data[4])|((uint32_t)rx_msg_data[5]<<8)|((uint32_t)rx_msg_data[6]<<16)|((uint32_t)rx_msg_data[7]<<24)); //dyno: ABS reply while the state machine runs //dyno debug 04/10/2026
			}else{
				SNIFFER_DEBUG2(0x2203, ((uint32_t)rx_msg_data[0])|((uint32_t)rx_msg_data[1]<<8)|((uint32_t)rx_msg_data[2]<<16)|((uint32_t)rx_msg_data[3]<<24), ((uint32_t)rx_msg_data[4])|((uint32_t)rx_msg_data[5]<<8)|((uint32_t)rx_msg_data[6]<<16)|((uint32_t)rx_msg_data[7]<<24)); //dyno: ABS reply while the state machine is idle (unsolicited, or late reply after a timeout) //dyno debug 04/10/2026
			}
		}
		if (rx_msg_header.ExtId==0x18DAF128 && DynoStateMachine!=0xff ){ //if message from ABS ECU and Dyno state machine is in progress
			if (DynoStateMachine==0 && rx_msg_header.DLC>=3){ //we received a reply to diagnostic session request msg
				if(rx_msg_data[0]==0x06 && rx_msg_data[1]==0x50 && rx_msg_data[2]==0x03){ //if request was successful
					DynoStateMachine++; //send dyno sts msg
				}
			}
			if (DynoStateMachine==1 && rx_msg_header.DLC>=5){ //we received a reply to dyno status msg
				if(rx_msg_data[0]==0x05 && rx_msg_data[1]==0x62 && rx_msg_data[2]==0x30 && rx_msg_data[3]==0x02){ //if request was successful
					DynoStateMachine++; //send dyno disable
					if(rx_msg_data[4]==0x00){ //if it is disabled, we shall enable it
						DynoModeEnabled=0;//refresh current status
						DynoStateMachine++;//send dyno enable
					}else{ //it is enabled, we shall disable it
						DynoModeEnabled=1;//refresh current status
					}
				}
			}
			if (DynoStateMachine==2 && rx_msg_header.DLC>=4){ //we received a reply to dyno disable msg
				if(rx_msg_data[0]==0x03 && rx_msg_data[1]==0x6E && rx_msg_data[2]==0x30 && rx_msg_data[3]==0x02){ //if request was successful
					SNIFFER_DEBUG(0x2210); //dyno: ABS confirmed dyno DISABLED //dyno debug 04/10/2026
					DynoModeEnabled=0;//success change complete
					DynoStateMachine=0xff; //disable state machine

					//send message to master to inform about the status of Dyno
					uint8_t tmpArr2[2]={C1BusID,C1cmdDynoNotActive};
					if(DynoModeEnabled) tmpArr2[1]=C1cmdDynoActive;
					addToUARTSendQueue(tmpArr2, 2);

					onboardLed_blue_on();
				}
			}
			if (DynoStateMachine==3 && rx_msg_header.DLC>=4){ //we received a reply to dyno enable msg
				if(rx_msg_data[0]==0x03 && rx_msg_data[1]==0x6E && rx_msg_data[2]==0x30 && rx_msg_data[3]==0x02){ //if request was successful
					SNIFFER_DEBUG(0x2211); //dyno: ABS confirmed dyno ENABLED //dyno debug 04/10/2026
					DynoModeEnabled=1;//success change complete

					DynoStateMachine=0xff; //disable state machine

					//send message to master to inform about the status of Dyno
					uint8_t tmpArr2[2]={C1BusID,C1cmdDynoNotActive};
					if(DynoModeEnabled) tmpArr2[1]=C1cmdDynoActive;
					addToUARTSendQueue(tmpArr2, 2);

					onboardLed_blue_on();
				}
			}

			if (DynoStateMachine!=0xff && rx_msg_header.DLC>=3){ //in any case
				if( rx_msg_data[1]==0x7F ){ //if request refused, abort all
					SNIFFER_DEBUG2(0x2212, DynoStateMachine, ((uint32_t)rx_msg_data[2]<<8)|rx_msg_data[3]); //dyno: ABS refused the request. v1=step, v2=byte1 service id, byte0 NRC //dyno debug 04/10/2026
					DynoStateMachine=0xff; //disable state machine

					//send message to master to inform about the status of Dyno
					uint8_t tmpArr2[2]={C1BusID,C1cmdDynoNotActive};
					if(DynoModeEnabled) tmpArr2[1]=C1cmdDynoActive;
					addToUARTSendQueue(tmpArr2, 2);

					onboardLed_blue_on();

				}
			}
			if(DynoStateMachine!=0xff){ //if we are running, send next message
				SNIFFER_DEBUG1(0x2213, DynoStateMachine); //dyno: sending the request of the next step //dyno debug 04/10/2026
				DYNO_msg_header.DLC=DYNO_msg_data[DynoStateMachine][0]+1;
				can_tx(&DYNO_msg_header, DYNO_msg_data[DynoStateMachine]); //add to the transmission queue
				onboardLed_blue_on();
				DynoStateMachineLastUpdateTime=currentTime;//save last time it was updated
			}
		}
	#endif


}
